MiSTer-devel/Arcade-SlapFight_MiSTer/docs/KiCAD/SlapFight/CPUA.kicad_sch

## KiCad design docs/KiCAD/SlapFight/CPUA.kicad_sch (2022-12-26)

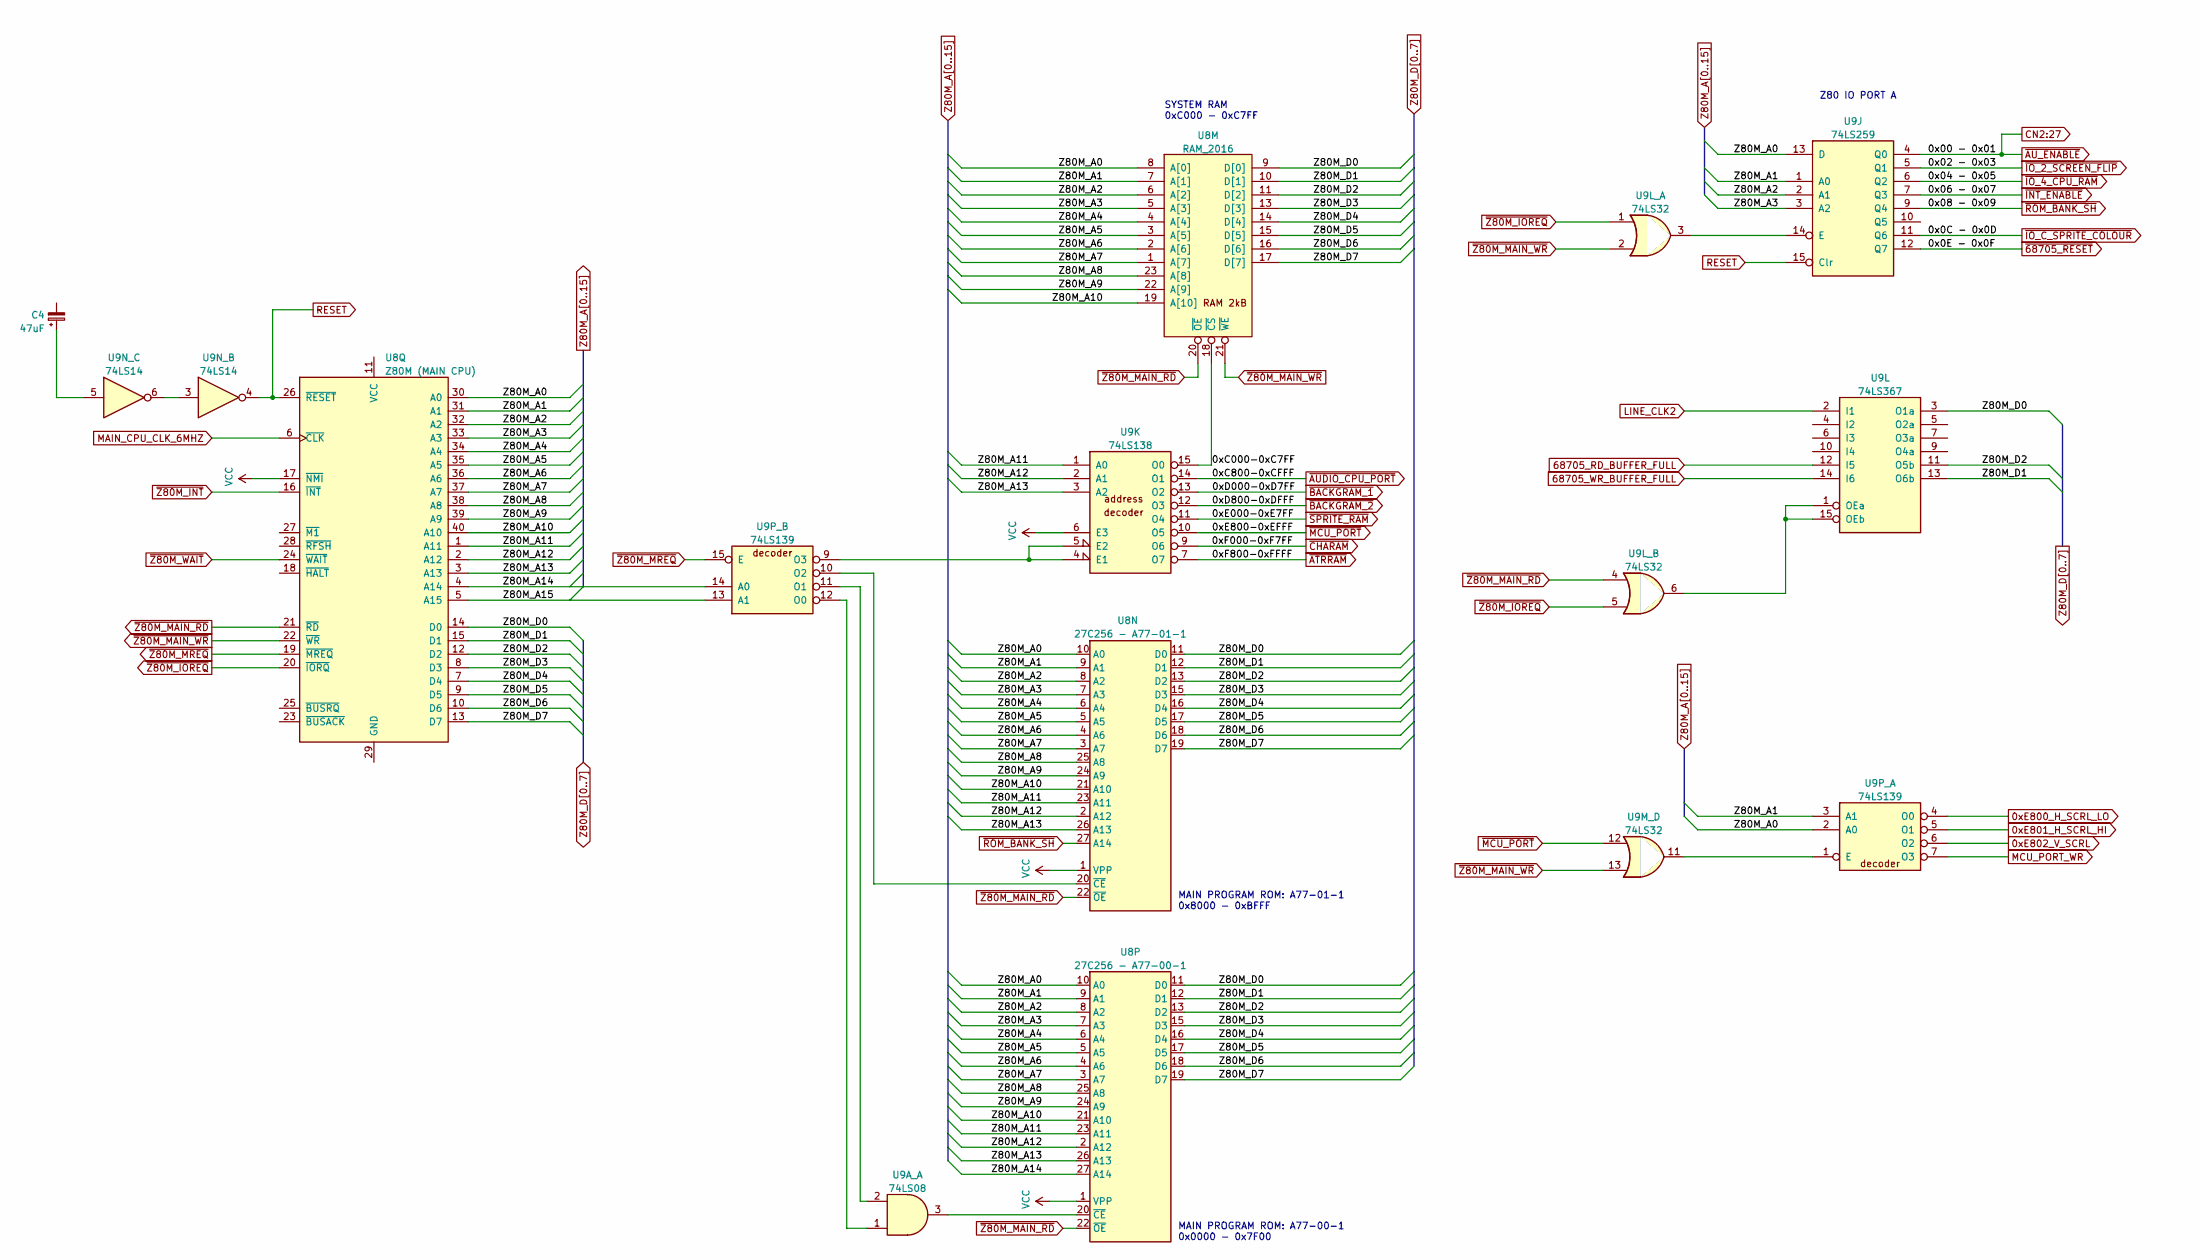
[picture p16: schematic CPUA.kicad_sch]

Parts:
C4: 47uF
U8M: RAM_2016
U8N: 27C256 - A77-01-1; DIP-28_W15.24mm
U8P: 27C256 - A77-00-1; DIP-28_W15.24mm
U8Q: Z80M (MAIN CPU)
U9A_: 74LS08
U9J: 74LS259
U9K: 74LS138
U9L: 74LS367
U9L_, U9M_: 74LS32
U9N_: 74LS14
U9P_: 74LS139

Connections:
0xC000-0xC7FF: U8M.18 (~CS), U9K.15 (O0)
0xE800_H_SCRL_LO: U9P_.4 (O0)
0xE801_H_SCRL_HI: U9P_.5 (O1)
0xE802_V_SCRL: U9P_.6 (O2)
68705_RD_BUFFER_FULL: U9L.12 (I5)
68705_WR_BUFFER_FULL: U9L.14 (I6)
CN2:27: U9J.4 (Q0)
LINE_CLK2: U9L.2 (I1)
MAIN_CPU_CLK_6MHZ: U8Q.6 (~CLK)
MCU_PORT_WR: U9P_.7 (O3)
unnamed: C4.1, U9N_.5
unnamed: U8N.20 (~CE), U9P_.10 (O2)
unnamed: U8P.20 (~CE), U9A_.3
unnamed: U9A_.1, U9P_.12 (O0)
unnamed: U9A_.2, U9P_.11 (O1)
unnamed: U9J.14 (E), U9L_.3
unnamed: U9K.4 (E1), U9K.5 (E2), U9P_.9 (O3)
unnamed: U9L.1 (OEa), U9L.15 (OEb), U9L_.6
unnamed: U9M_.11, U9P_.1 (E)
unnamed: U9N_.3, U9N_.6
RESET: U8Q.26 (~RESET), U9J.15 (Clr), U9N_.4
VCC: U8N.1 (VPP), U8P.1 (VPP), U8Q.17 (~NMI), U9K.6 (E3)
Z80M_A0: U8M.8 (A[0]), U8N.10 (A0), U8P.10 (A0), U8Q.30 (A0), U9J.13 (D), U9P_.2 (A0)
Z80M_A1: U8M.7 (A[1]), U8N.9 (A1), U8P.9 (A1), U8Q.31 (A1), U9J.1 (A0), U9P_.3 (A1)
Z80M_A2: U8M.6 (A[2]), U8N.8 (A2), U8P.8 (A2), U8Q.32 (A2), U9J.2 (A1)
Z80M_A3: U8M.5 (A[3]), U8N.7 (A3), U8P.7 (A3), U8Q.33 (A3), U9J.3 (A2)
Z80M_A4: U8M.4 (A[4]), U8N.6 (A4), U8P.6 (A4), U8Q.34 (A4)
Z80M_A5: U8M.3 (A[5]), U8N.5 (A5), U8P.5 (A5), U8Q.35 (A5)
Z80M_A6: U8M.2 (A[6]), U8N.4 (A6), U8P.4 (A6), U8Q.36 (A6)
Z80M_A7: U8M.1 (A[7]), U8N.3 (A7), U8P.3 (A7), U8Q.37 (A7)
Z80M_A8: U8M.23 (A[8]), U8N.25 (A8), U8P.25 (A8), U8Q.38 (A8)
Z80M_A9: U8M.22 (A[9]), U8N.24 (A9), U8P.24 (A9), U8Q.39 (A9)
Z80M_A10: U8M.19 (A[10]), U8N.21 (A10), U8P.21 (A10), U8Q.40 (A10)
Z80M_A11: U8N.23 (A11), U8P.23 (A11), U8Q.1 (A11), U9K.1 (A0)
Z80M_A12: U8N.2 (A12), U8P.2 (A12), U8Q.2 (A12), U9K.2 (A1)
Z80M_A13: U8N.26 (A13), U8P.26 (A13), U8Q.3 (A13), U9K.3 (A2)
Z80M_A14: U8P.27 (A14), U8Q.4 (A14), U9P_.14 (A0)
Z80M_A15: U8Q.5 (A15), U9P_.13 (A1)
Z80M_D0: U8M.9 (D[0]), U8N.11 (D0), U8P.11 (D0), U8Q.14 (D0), U9L.3 (O1a)
Z80M_D1: U8M.10 (D[1]), U8N.12 (D1), U8P.12 (D1), U8Q.15 (D1), U9L.13 (O6b)
Z80M_D2: U8M.11 (D[2]), U8N.13 (D2), U8P.13 (D2), U8Q.12 (D2), U9L.11 (O5b)
Z80M_D3: U8M.13 (D[3]), U8N.15 (D3), U8P.15 (D3), U8Q.8 (D3)
Z80M_D4: U8M.14 (D[4]), U8N.16 (D4), U8P.16 (D4), U8Q.7 (D4)
Z80M_D5: U8M.15 (D[5]), U8N.17 (D5), U8P.17 (D5), U8Q.9 (D5)
Z80M_D6: U8M.16 (D[6]), U8N.18 (D6), U8P.18 (D6), U8Q.10 (D6)
Z80M_D7: U8M.17 (D[7]), U8N.19 (D7), U8P.19 (D7), U8Q.13 (D7)
~68705_RESET: U9J.12 (Q7)
~ATRRAM: U9K.7 (O7)
~AUDIO_CPU_PORT: U9K.14 (O1)
~BACKGRAM_1: U9K.13 (O2)
~BACKGRAM_2: U9K.12 (O3)
~CHARAM: U9K.9 (O6)
~INT_ENABLE: U9J.7 (Q3)
~IO_2_SCREEN_FLIP: U9J.5 (Q1)
~IO_4_CPU_RAM: U9J.6 (Q2)
~IO_C_SPRITE_COLOUR: U9J.11 (Q6)
~MCU_PORT: U9K.10 (O5), U9M_.12
~ROM_BANK_SH: U8N.27 (A14), U9J.9 (Q4)
~SPRITE_RAM: U9K.11 (O4)
~Z80M_INT: U8Q.16 (~INT)
~Z80M_IOREQ: U8Q.20 (~IORQ), U9L_.1, U9L_.5
~Z80M_MAIN_RD: U8M.20 (~OE), U8N.22 (~OE), U8P.22 (~OE), U8Q.21 (~RD), U9L_.4
~Z80M_MAIN_WR: U8M.21 (~WE), U8Q.22 (~WR), U9L_.2, U9M_.13
~Z80M_MREQ: U8Q.19 (~MREQ), U9P_.15 (E)
~Z80M_WAIT: U8Q.24 (~WAIT)

Notes on the sheet:
MAIN PROGRAM ROM: A77-01-1 0x8000 - 0xBFFF
MAIN PROGRAM ROM: A77-00-1 0x0000 - 0x7F00
SYSTEM RAM 0xC000 - 0xC7FF
Z80 IO PORT A
