MiSTer-devel/Arcade-SlapFight_MiSTer/docs/KiCAD/SlapFight/SpriteRAM.kicad_sch

## KiCad design docs/KiCAD/SlapFight/SpriteRAM.kicad_sch (2022-12-26)

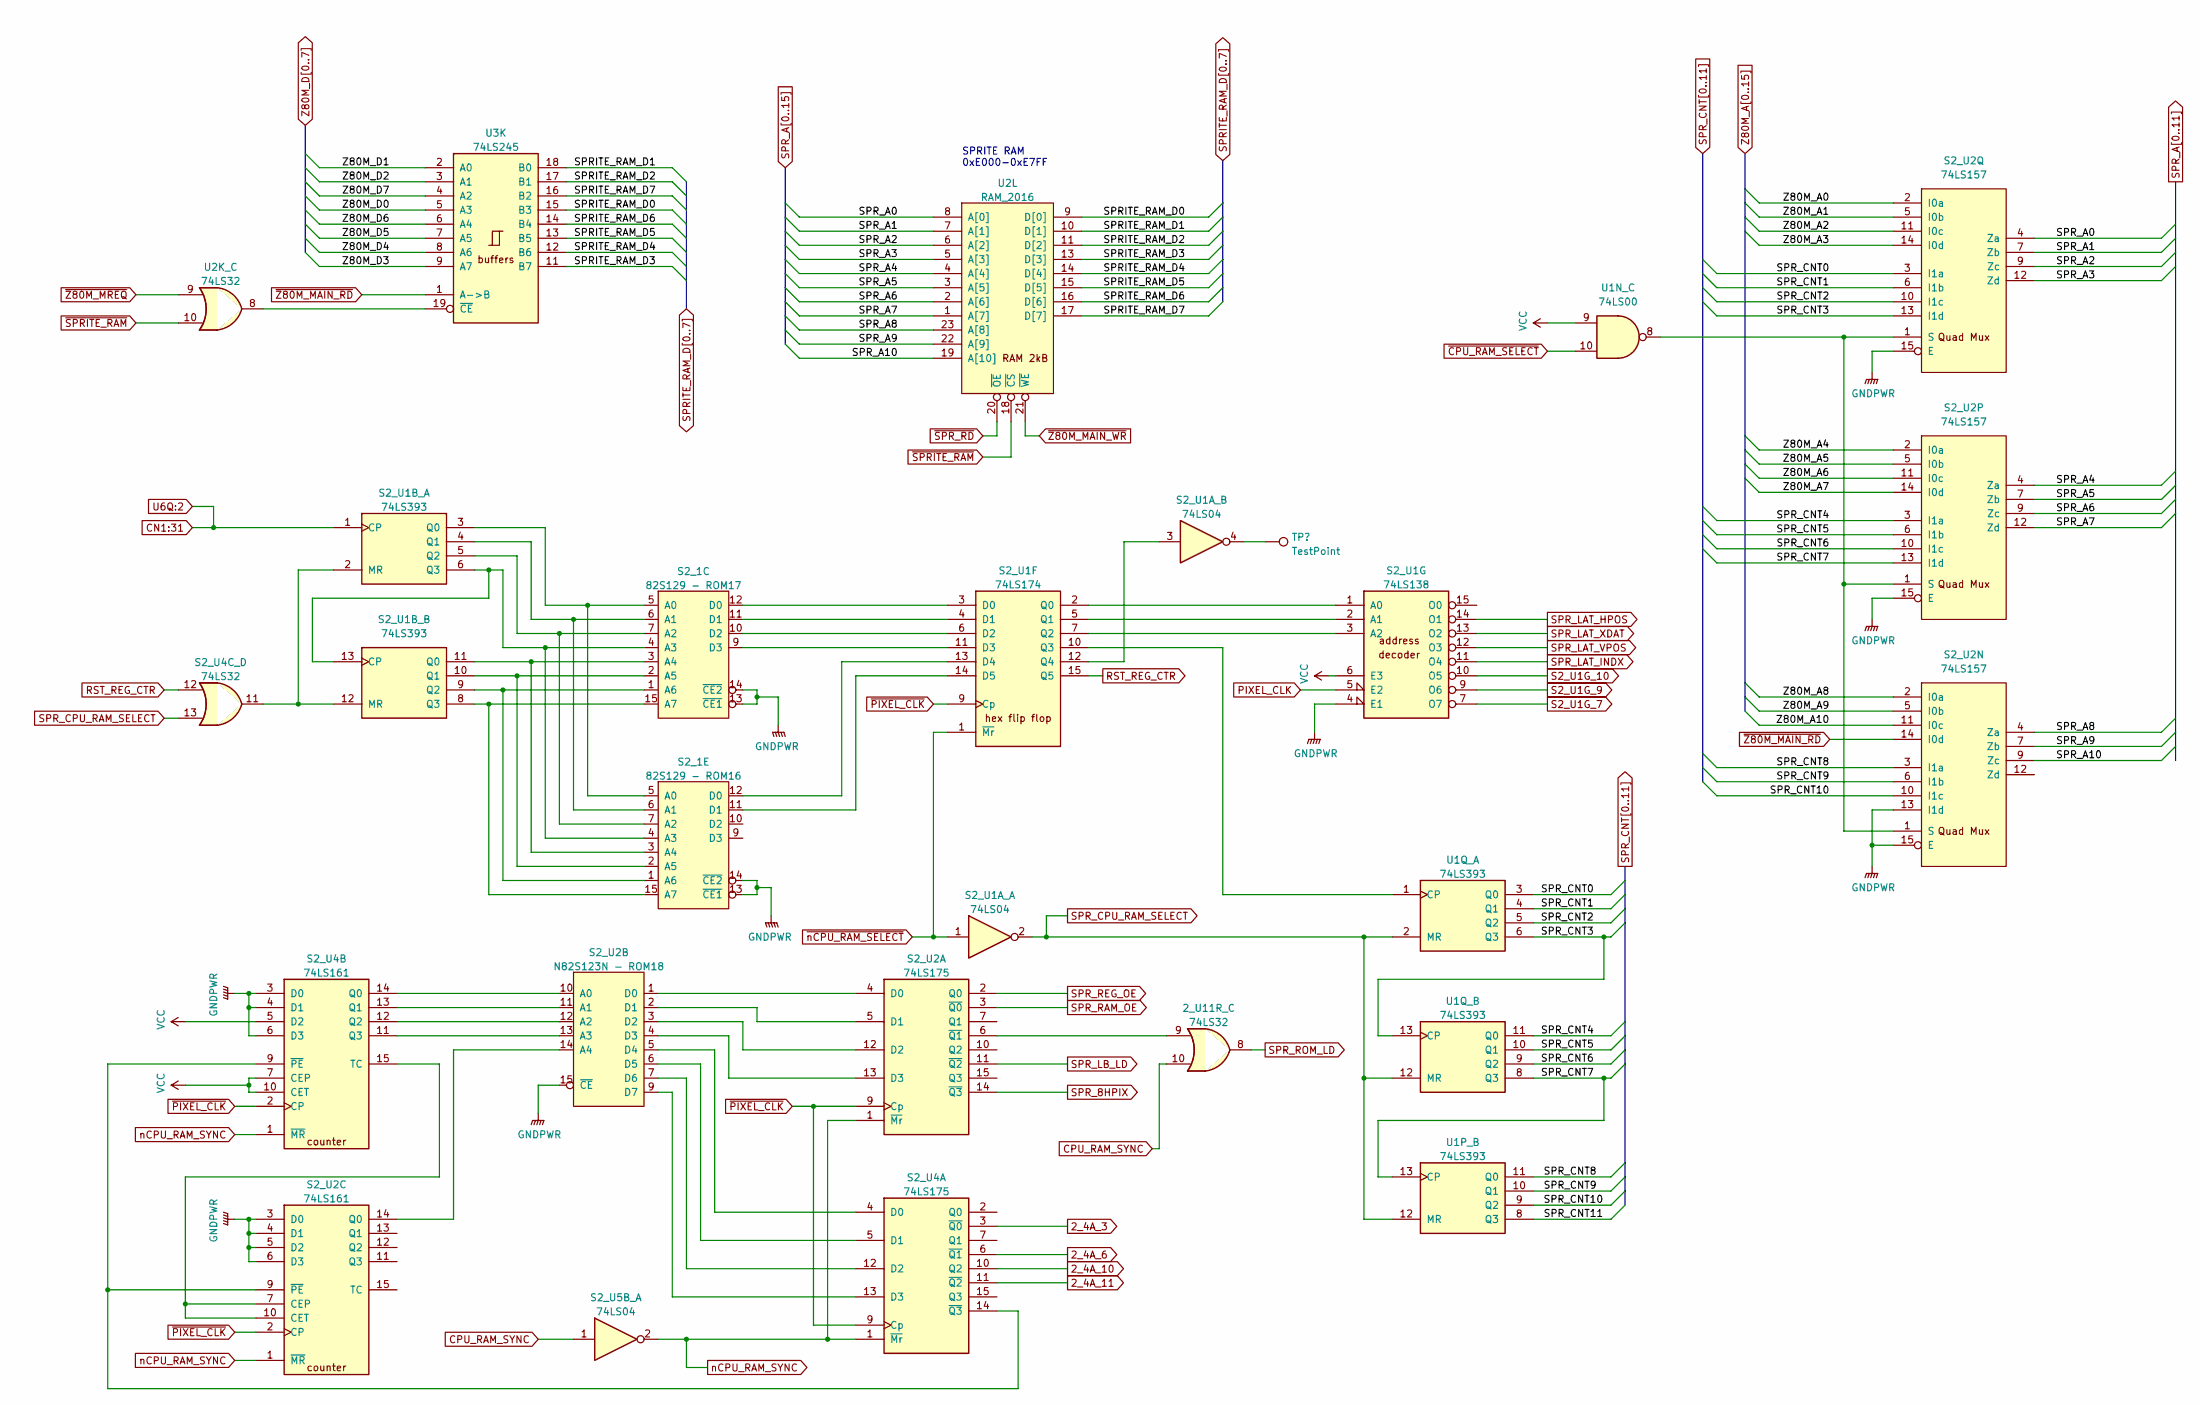
[picture p17: schematic SpriteRAM.kicad_sch]

Parts:
2_U11R_: 74LS32
S2_1C: 82S129 - ROM17
S2_1E: 82S129 - ROM16
S2_U1A_, S2_U5B_: 74LS04
S2_U1B_: 74LS393
S2_U1F: 74LS174
S2_U1G: 74LS138
S2_U2A, S2_U4A: 74LS175
S2_U2B: N82S123N - ROM18
S2_U2C, S2_U4B: 74LS161
S2_U2N, S2_U2P, S2_U2Q: 74LS157
S2_U4C_: 74LS32
U1N_: 74LS00
U1P_, U1Q_: 74LS393
U2K_: 74LS32
U2L: RAM_2016
U3K: 74LS245

Connections:
2_4A_3: S2_U4A.3 (~Q0)
2_4A_6: S2_U4A.6 (~Q1)
2_4A_10: S2_U4A.10 (Q2)
2_4A_11: S2_U4A.11 (~Q2)
CN1:31: S2_U1B_.1 (CP)
CPU_RAM_SYNC: 2_U11R_.10, S2_U5B_.1
unnamed: 2_U11R_.9, S2_U2A.6 (~Q1)
unnamed: S2_1C.1 (A6), S2_1E.1 (A6), S2_U1B_.9 (Q2)
unnamed: S2_1C.2 (A5), S2_1E.2 (A5), S2_U1B_.10 (Q1)
unnamed: S2_1C.3 (A4), S2_1E.3 (A4), S2_U1B_.11 (Q0)
unnamed: S2_1C.4 (A3), S2_1E.4 (A3), S2_U1B_.6 (Q3), S2_U1B_.13 (CP)
unnamed: S2_1C.5 (A0), S2_1E.5 (A0), S2_U1B_.3 (Q0)
unnamed: S2_1C.6 (A1), S2_1E.6 (A1), S2_U1B_.4 (Q1)
unnamed: S2_1C.7 (A2), S2_1E.7 (A2), S2_U1B_.5 (Q2)
unnamed: S2_1C.9 (D3), S2_U1F.11 (D3)
unnamed: S2_1C.10 (D2), S2_U1F.6 (D2)
unnamed: S2_1C.11 (D1), S2_U1F.4 (D1)
unnamed: S2_1C.12 (D0), S2_U1F.3 (D0)
unnamed: S2_1C.13 (~CE1), S2_1C.14 (~CE2)
unnamed: S2_1C.15 (A7), S2_1E.15 (A7), S2_U1B_.8 (Q3)
unnamed: S2_1E.11 (D1), S2_U1F.14 (D5)
unnamed: S2_1E.12 (D0), S2_U1F.13 (D4)
unnamed: S2_1E.13 (~CE1), S2_1E.14 (~CE2)
unnamed: S2_U1A_.3, S2_U1F.12 (Q4)
unnamed: S2_U1B_.2 (MR), S2_U1B_.12 (MR), S2_U4C_.11
unnamed: S2_U1F.2 (Q0), S2_U1G.1 (A0)
unnamed: S2_U1F.5 (Q1), S2_U1G.2 (A1)
unnamed: S2_U1F.7 (Q2), S2_U1G.3 (A2)
unnamed: S2_U1F.10 (Q3), U1Q_.1 (CP)
unnamed: S2_U2A.4 (D0), S2_U2B.1 (D0)
unnamed: S2_U2A.5 (D1), S2_U2B.2 (D1)
unnamed: S2_U2A.12 (D2), S2_U2B.3 (D2)
unnamed: S2_U2A.13 (D3), S2_U2B.4 (D3)
unnamed: S2_U2B.5 (D4), S2_U4A.4 (D0)
unnamed: S2_U2B.6 (D5), S2_U4A.5 (D1)
unnamed: S2_U2B.7 (D6), S2_U4A.12 (D2)
unnamed: S2_U2B.9 (D7), S2_U4A.13 (D3)
unnamed: S2_U2B.10 (A0), S2_U4B.14 (Q0)
unnamed: S2_U2B.11 (A1), S2_U4B.13 (Q1)
unnamed: S2_U2B.12 (A2), S2_U4B.12 (Q2)
unnamed: S2_U2B.13 (A3), S2_U4B.11 (Q3)
unnamed: S2_U2B.14 (A4), S2_U2C.14 (Q0)
unnamed: S2_U2C.3 (D0), S2_U2C.4 (D1), S2_U2C.5 (D2), S2_U2C.6 (D3)
unnamed: S2_U2C.9 (~PE), S2_U4A.14 (~Q3), S2_U4B.9 (~PE)
unnamed: S2_U2C.7 (CEP), S2_U2C.10 (CET), S2_U4B.15 (TC)
unnamed: S2_U2N.1 (S), S2_U2P.1 (S), S2_U2Q.1 (S), U1N_.8
unnamed: S2_U2N.13 (I1d), S2_U2N.15 (E)
unnamed: S2_U4B.3 (D0), S2_U4B.4 (D1), S2_U4B.6 (D3)
unnamed: S2_U4B.7 (CEP), S2_U4B.10 (CET)
unnamed: U2K_.8, U3K.19 (~CE)
PIXEL_CLK: S2_U1G.5 (E2)
RST_REG_CTR: S2_U1F.15 (Q5), S2_U4C_.12
S2_U1G_7: S2_U1G.7 (O7)
S2_U1G_9: S2_U1G.9 (O6)
S2_U1G_10: S2_U1G.10 (O5)
SPRITE_RAM_D0: U2L.9 (D[0]), U3K.15 (B3)
SPRITE_RAM_D1: U2L.10 (D[1]), U3K.18 (B0)
SPRITE_RAM_D2: U2L.11 (D[2]), U3K.17 (B1)
SPRITE_RAM_D3: U2L.13 (D[3]), U3K.11 (B7)
SPRITE_RAM_D4: U2L.14 (D[4]), U3K.12 (B6)
SPRITE_RAM_D5: U2L.15 (D[5]), U3K.13 (B5)
SPRITE_RAM_D6: U2L.16 (D[6]), U3K.14 (B4)
SPRITE_RAM_D7: U2L.17 (D[7]), U3K.16 (B2)
SPR_8HPIX: S2_U2A.14 (~Q3)
SPR_A0: S2_U2Q.4 (Za), U2L.8 (A[0])
SPR_A1: S2_U2Q.7 (Zb), U2L.7 (A[1])
SPR_A2: S2_U2Q.9 (Zc), U2L.6 (A[2])
SPR_A3: S2_U2Q.12 (Zd), U2L.5 (A[3])
SPR_A4: S2_U2P.4 (Za), U2L.4 (A[4])
SPR_A5: S2_U2P.7 (Zb), U2L.3 (A[5])
SPR_A6: S2_U2P.9 (Zc), U2L.2 (A[6])
SPR_A7: S2_U2P.12 (Zd), U2L.1 (A[7])
SPR_A8: S2_U2N.4 (Za), U2L.23 (A[8])
SPR_A9: S2_U2N.7 (Zb), U2L.22 (A[9])
SPR_A10: S2_U2N.9 (Zc), U2L.19 (A[10])
SPR_CNT0: S2_U2Q.3 (I1a), U1Q_.3 (Q0)
SPR_CNT1: S2_U2Q.6 (I1b), U1Q_.4 (Q1)
SPR_CNT2: S2_U2Q.10 (I1c), U1Q_.5 (Q2)
SPR_CNT3: S2_U2Q.13 (I1d), U1Q_.6 (Q3), U1Q_.13 (CP)
SPR_CNT4: S2_U2P.3 (I1a), U1Q_.11 (Q0)
SPR_CNT5: S2_U2P.6 (I1b), U1Q_.10 (Q1)
SPR_CNT6: S2_U2P.10 (I1c), U1Q_.9 (Q2)
SPR_CNT7: S2_U2P.13 (I1d), U1P_.13 (CP), U1Q_.8 (Q3)
SPR_CNT8: S2_U2N.3 (I1a), U1P_.11 (Q0)
SPR_CNT9: S2_U2N.6 (I1b), U1P_.10 (Q1)
SPR_CNT10: S2_U2N.10 (I1c), U1P_.9 (Q2)
SPR_CNT11: U1P_.8 (Q3)
SPR_CPU_RAM_SELECT: S2_U1A_.2, S2_U4C_.13, U1P_.12 (MR), U1Q_.2 (MR), U1Q_.12 (MR)
SPR_LAT_HPOS: S2_U1G.14 (O1)
SPR_LAT_INDX: S2_U1G.11 (O4)
SPR_LAT_VPOS: S2_U1G.12 (O3)
SPR_LAT_XDAT: S2_U1G.13 (O2)
SPR_LB_LD: S2_U2A.11 (~Q2)
SPR_RAM_OE: S2_U2A.3 (~Q0)
SPR_REG_OE: S2_U2A.2 (Q0)
SPR_ROM_LD: 2_U11R_.8
Z80M_A0: S2_U2Q.2 (I0a)
Z80M_A1: S2_U2Q.5 (I0b)
Z80M_A2: S2_U2Q.11 (I0c)
Z80M_A3: S2_U2Q.14 (I0d)
Z80M_A4: S2_U2P.2 (I0a)
Z80M_A5: S2_U2P.5 (I0b)
Z80M_A6: S2_U2P.11 (I0c)
Z80M_A7: S2_U2P.14 (I0d)
Z80M_A8: S2_U2N.2 (I0a)
Z80M_A9: S2_U2N.5 (I0b)
Z80M_A10: S2_U2N.11 (I0c)
Z80M_D0: U3K.5 (A3)
Z80M_D1: U3K.2 (A0)
Z80M_D2: U3K.3 (A1)
Z80M_D3: U3K.9 (A7)
Z80M_D4: U3K.8 (A6)
Z80M_D5: U3K.7 (A5)
Z80M_D6: U3K.6 (A4)
Z80M_D7: U3K.4 (A2)
nCPU_RAM_SYNC: S2_U2A.1 (~Mr), S2_U2C.1 (~MR), S2_U4A.1 (~Mr), S2_U4B.1 (~MR), S2_U5B_.2
~CPU_RAM_SELECT: U1N_.10
~PIXEL_CLK: S2_U1F.9 (Cp), S2_U2A.9 (Cp), S2_U2C.2 (CP), S2_U4A.9 (Cp), S2_U4B.2 (CP)
~SPRITE_RAM: U2K_.10, U2L.18 (~CS)
~SPR_RD: U2L.20 (~OE)
~Z80M_MAIN_RD: S2_U2N.14 (I0d), U3K.1 (A->B)
~Z80M_MAIN_WR: U2L.21 (~WE)
~Z80M_MREQ: U2K_.9
~nCPU_RAM_SELECT: S2_U1A_.1, S2_U1F.1 (~Mr)

Notes on the sheet:
SPRITE RAM 0xE000-0xE7FF
