MiSTer-devel/Arcade-SlapFight_MiSTer/docs/KiCAD/SlapFight/SpriteROM.kicad_sch

## KiCad design docs/KiCAD/SlapFight/SpriteROM.kicad_sch (2022-12-26)

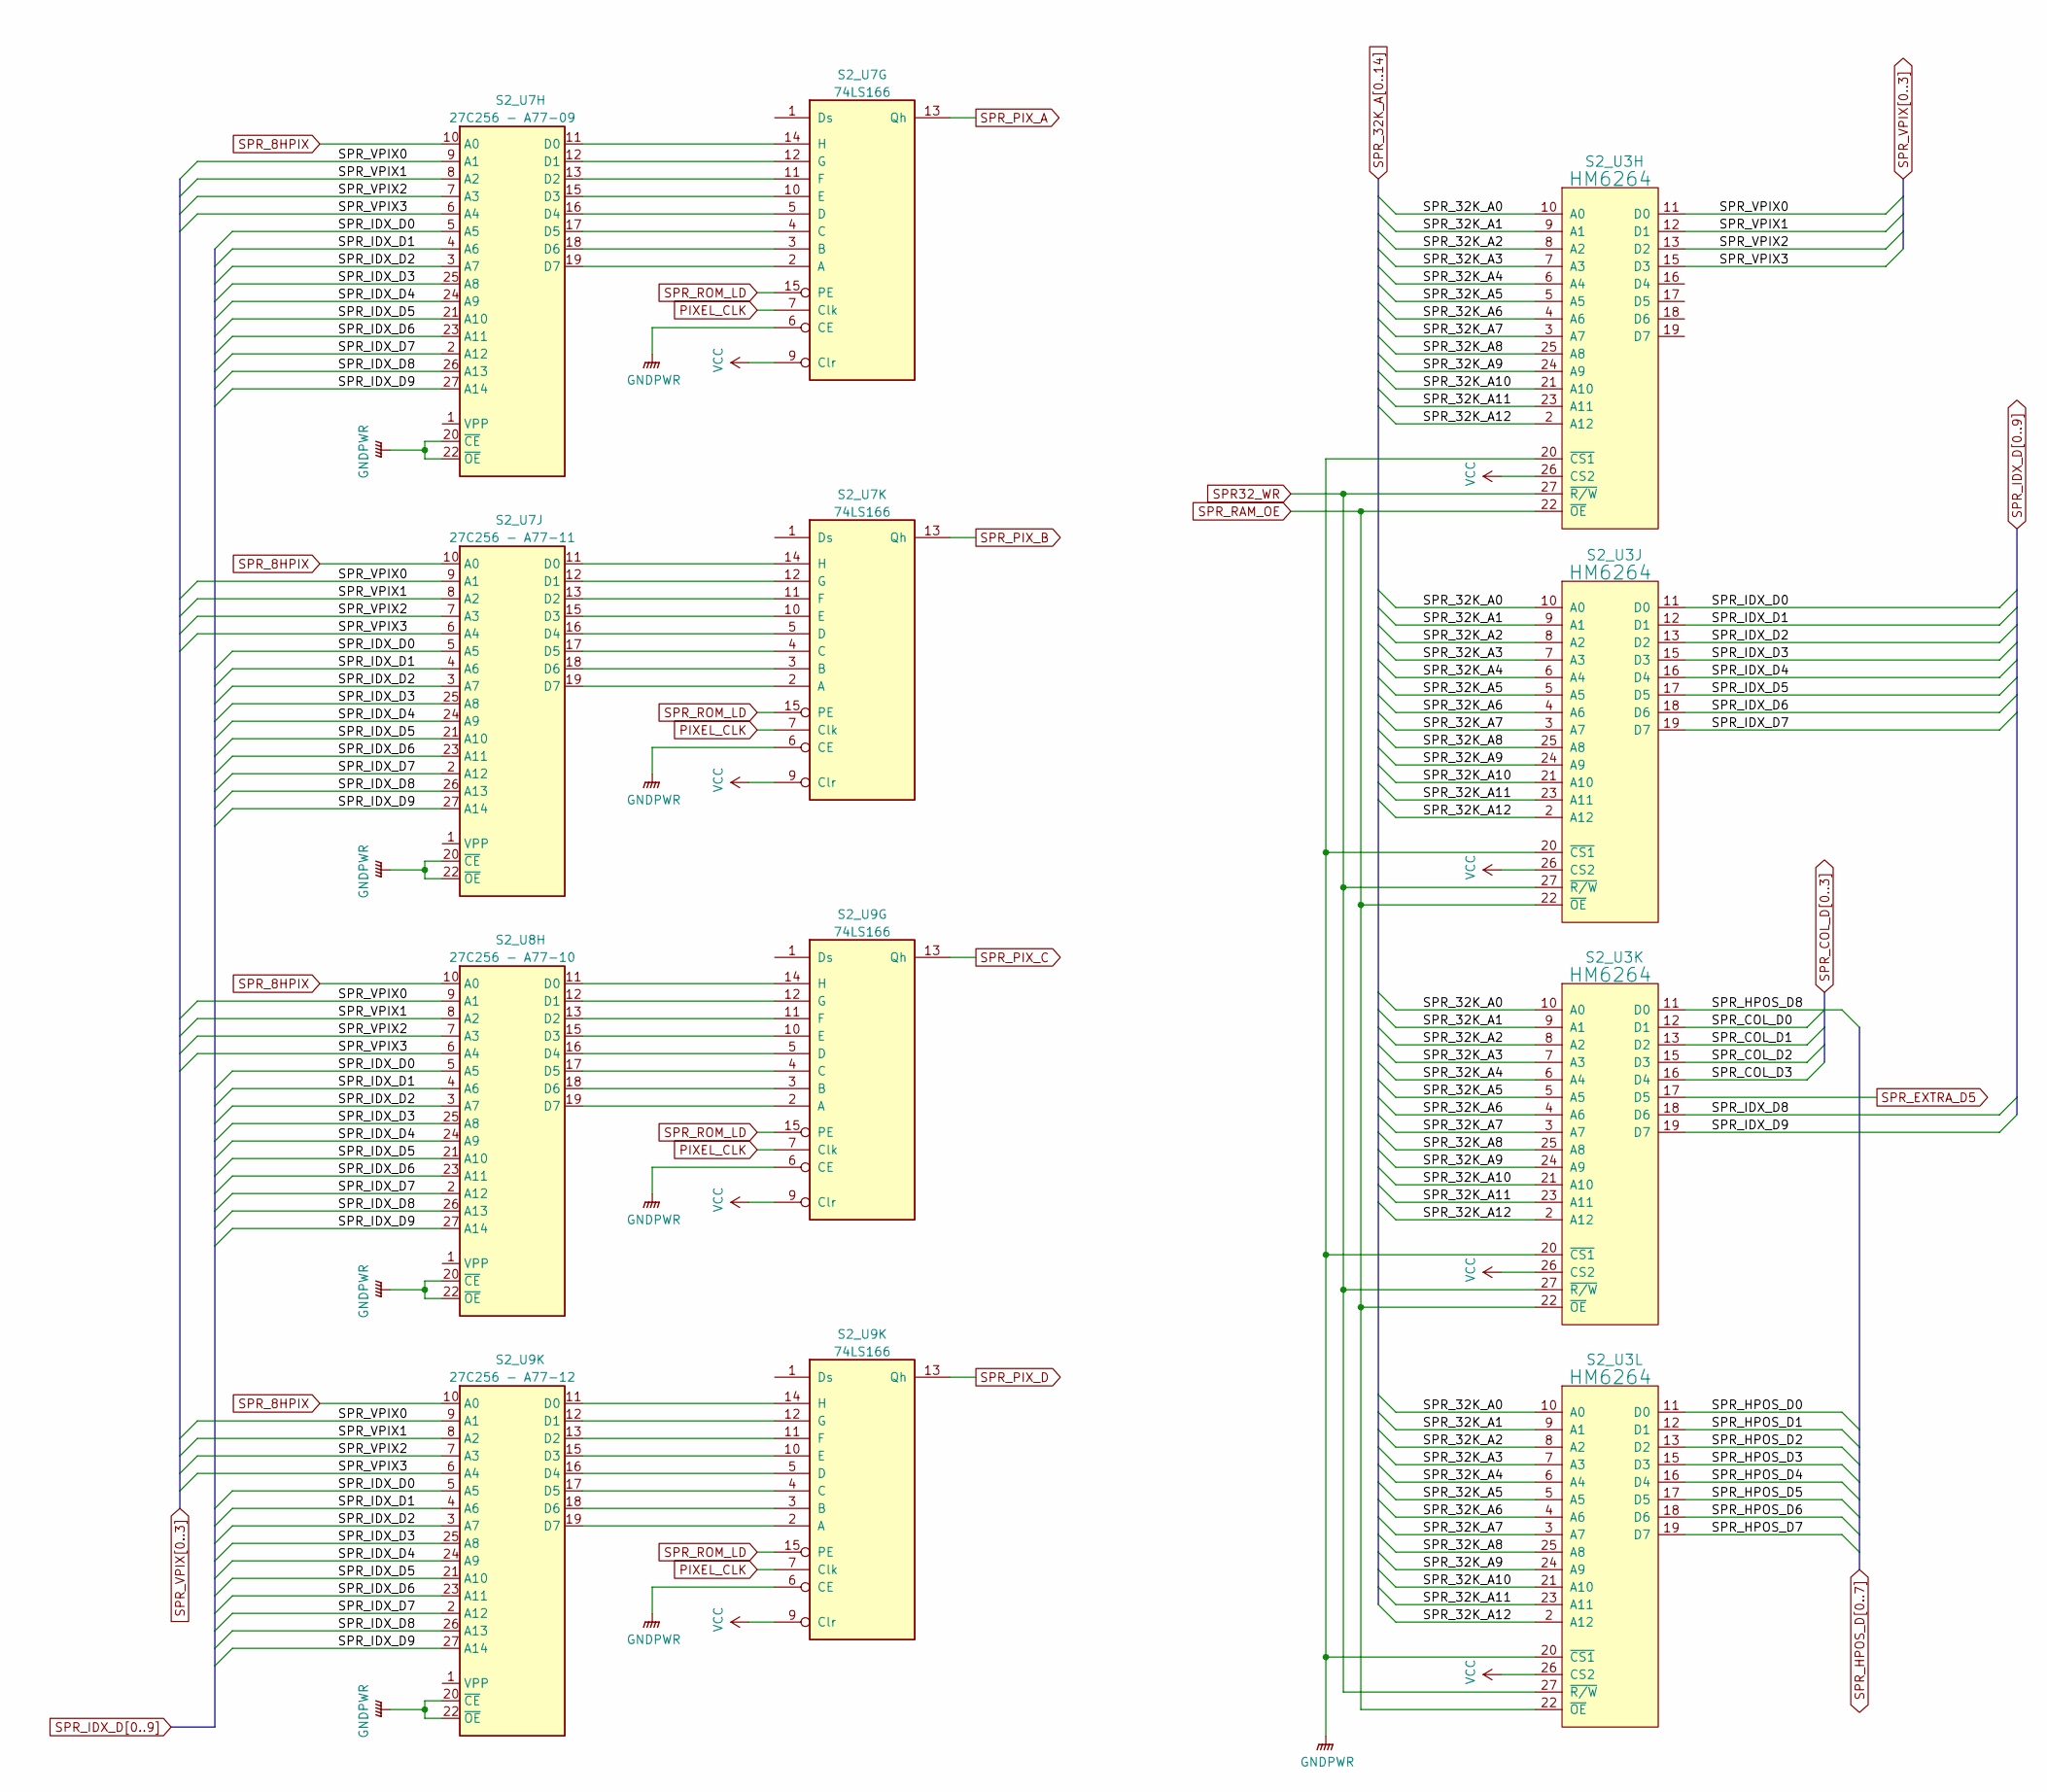
[picture p18: schematic SpriteROM.kicad_sch]

Parts:
S2_U3H, S2_U3J, S2_U3K, S2_U3L: HM6264
S2_U7G, S2_U7K, S2_U9G, S2_U9K: 74LS166
S2_U7H: 27C256 - A77-09; DIP-28_W15.24mm
S2_U7J: 27C256 - A77-11; DIP-28_W15.24mm
S2_U8H: 27C256 - A77-10; DIP-28_W15.24mm

Connections:
unnamed: S2_U3H.20 (~CS1), S2_U3J.20 (~CS1), S2_U3K.20 (~CS1), S2_U3L.20 (~CS1)
unnamed: S2_U7G.2 (A), S2_U7H.19 (D7)
unnamed: S2_U7G.3 (B), S2_U7H.18 (D6)
unnamed: S2_U7G.4 (C), S2_U7H.17 (D5)
unnamed: S2_U7G.5 (D), S2_U7H.16 (D4)
unnamed: S2_U7G.10 (E), S2_U7H.15 (D3)
unnamed: S2_U7G.11 (F), S2_U7H.13 (D2)
unnamed: S2_U7G.12 (G), S2_U7H.12 (D1)
unnamed: S2_U7G.14 (H), S2_U7H.11 (D0)
unnamed: S2_U7H.20 (~CE), S2_U7H.22 (~OE)
unnamed: S2_U7J.11 (D0), S2_U7K.14 (H)
unnamed: S2_U7J.12 (D1), S2_U7K.12 (G)
unnamed: S2_U7J.13 (D2), S2_U7K.11 (F)
unnamed: S2_U7J.15 (D3), S2_U7K.10 (E)
unnamed: S2_U7J.16 (D4), S2_U7K.5 (D)
unnamed: S2_U7J.17 (D5), S2_U7K.4 (C)
unnamed: S2_U7J.18 (D6), S2_U7K.3 (B)
unnamed: S2_U7J.19 (D7), S2_U7K.2 (A)
unnamed: S2_U7J.20 (~CE), S2_U7J.22 (~OE)
unnamed: S2_U8H.11 (D0), S2_U9G.14 (H)
unnamed: S2_U8H.12 (D1), S2_U9G.12 (G)
unnamed: S2_U8H.13 (D2), S2_U9G.11 (F)
unnamed: S2_U8H.15 (D3), S2_U9G.10 (E)
unnamed: S2_U8H.16 (D4), S2_U9G.5 (D)
unnamed: S2_U8H.17 (D5), S2_U9G.4 (C)
unnamed: S2_U8H.18 (D6), S2_U9G.3 (B)
unnamed: S2_U8H.19 (D7), S2_U9G.2 (A)
unnamed: S2_U8H.20 (~CE), S2_U8H.22 (~OE)
unnamed: S2_U9K.10 (A0), S2_U9K.15 (D3)
unnamed: S2_U9K.11 (D0), S2_U9K.13 (D2), S2_U9K.14 (GND)
unnamed: S2_U9K.5 (A5), S2_U9K.16 (D4)
unnamed: S2_U9K.4 (A6), S2_U9K.17 (D5)
unnamed: S2_U9K.3 (A7), S2_U9K.18 (D6)
unnamed: S2_U9K.2 (A12), S2_U9K.19 (D7)
unnamed: S2_U9K.20 (~CE), S2_U9K.22 (~OE)
PIXEL_CLK: S2_U7G.7 (Clk), S2_U7K.7 (Clk), S2_U9G.7 (Clk), S2_U9K.7 (A3)
SPR32_WR: S2_U3H.27 (~R/W), S2_U3J.27 (~R/W), S2_U3K.27 (~R/W), S2_U3L.27 (~R/W)
SPR_8HPIX: S2_U7H.10 (A0), S2_U7J.10 (A0), S2_U8H.10 (A0), S2_U9K.10 (A0)
SPR_32K_A0: S2_U3H.10 (A0), S2_U3J.10 (A0), S2_U3K.10 (A0), S2_U3L.10 (A0)
SPR_32K_A1: S2_U3H.9 (A1), S2_U3J.9 (A1), S2_U3K.9 (A1), S2_U3L.9 (A1)
SPR_32K_A2: S2_U3H.8 (A2), S2_U3J.8 (A2), S2_U3K.8 (A2), S2_U3L.8 (A2)
SPR_32K_A3: S2_U3H.7 (A3), S2_U3J.7 (A3), S2_U3K.7 (A3), S2_U3L.7 (A3)
SPR_32K_A4: S2_U3H.6 (A4), S2_U3J.6 (A4), S2_U3K.6 (A4), S2_U3L.6 (A4)
SPR_32K_A5: S2_U3H.5 (A5), S2_U3J.5 (A5), S2_U3K.5 (A5), S2_U3L.5 (A5)
SPR_32K_A6: S2_U3H.4 (A6), S2_U3J.4 (A6), S2_U3K.4 (A6), S2_U3L.4 (A6)
SPR_32K_A7: S2_U3H.3 (A7), S2_U3J.3 (A7), S2_U3K.3 (A7), S2_U3L.3 (A7)
SPR_32K_A8: S2_U3H.25 (A8), S2_U3J.25 (A8), S2_U3K.25 (A8), S2_U3L.25 (A8)
SPR_32K_A9: S2_U3H.24 (A9), S2_U3J.24 (A9), S2_U3K.24 (A9), S2_U3L.24 (A9)
SPR_32K_A10: S2_U3H.21 (A10), S2_U3J.21 (A10), S2_U3K.21 (A10), S2_U3L.21 (A10)
SPR_32K_A11: S2_U3H.23 (A11), S2_U3J.23 (A11), S2_U3K.23 (A11), S2_U3L.23 (A11)
SPR_32K_A12: S2_U3H.2 (A12), S2_U3J.2 (A12), S2_U3K.2 (A12), S2_U3L.2 (A12)
SPR_COL_D0: S2_U3K.12 (D1)
SPR_COL_D1: S2_U3K.13 (D2)
SPR_COL_D2: S2_U3K.15 (D3)
SPR_COL_D3: S2_U3K.16 (D4)
SPR_EXTRA_D5: S2_U3K.17 (D5)
SPR_HPOS_D0: S2_U3L.11 (D0)
SPR_HPOS_D1: S2_U3L.12 (D1)
SPR_HPOS_D2: S2_U3L.13 (D2)
SPR_HPOS_D3: S2_U3L.15 (D3)
SPR_HPOS_D4: S2_U3L.16 (D4)
SPR_HPOS_D5: S2_U3L.17 (D5)
SPR_HPOS_D6: S2_U3L.18 (D6)
SPR_HPOS_D7: S2_U3L.19 (D7)
SPR_HPOS_D8: S2_U3K.11 (D0)
SPR_IDX_D0: S2_U3J.11 (D0), S2_U7H.5 (A5), S2_U7J.5 (A5), S2_U8H.5 (A5), S2_U9K.5 (A5)
SPR_IDX_D1: S2_U3J.12 (D1), S2_U7H.4 (A6), S2_U7J.4 (A6), S2_U8H.4 (A6), S2_U9K.4 (A6)
SPR_IDX_D2: S2_U3J.13 (D2), S2_U7H.3 (A7), S2_U7J.3 (A7), S2_U8H.3 (A7), S2_U9K.3 (A7)
SPR_IDX_D3: S2_U3J.15 (D3), S2_U7H.25 (A8), S2_U7J.25 (A8), S2_U8H.25 (A8), S2_U9K.25 (A8)
SPR_IDX_D4: S2_U3J.16 (D4), S2_U7H.24 (A9), S2_U7J.24 (A9), S2_U8H.24 (A9), S2_U9K.24 (A9)
SPR_IDX_D5: S2_U3J.17 (D5), S2_U7H.21 (A10), S2_U7J.21 (A10), S2_U8H.21 (A10), S2_U9K.21 (A10)
SPR_IDX_D6: S2_U3J.18 (D6), S2_U7H.23 (A11), S2_U7J.23 (A11), S2_U8H.23 (A11), S2_U9K.23 (A11)
SPR_IDX_D7: S2_U3J.19 (D7), S2_U7H.2 (A12), S2_U7J.2 (A12), S2_U8H.2 (A12), S2_U9K.2 (A12)
SPR_IDX_D8: S2_U3K.18 (D6), S2_U7H.26 (A13), S2_U7J.26 (A13), S2_U8H.26 (A13), S2_U9K.26 (A13)
SPR_IDX_D9: S2_U3K.19 (D7), S2_U7H.27 (A14), S2_U7J.27 (A14), S2_U8H.27 (A14), S2_U9K.27 (A14)
SPR_PIX_A: S2_U7G.13 (Qh)
SPR_PIX_B: S2_U7K.13 (Qh)
SPR_PIX_C: S2_U9G.13 (Qh)
SPR_PIX_D: S2_U9K.13 (D2)
SPR_RAM_OE: S2_U3H.22 (~OE), S2_U3J.22 (~OE), S2_U3K.22 (~OE), S2_U3L.22 (~OE)
SPR_ROM_LD: S2_U7G.15 (PE), S2_U7K.15 (PE), S2_U9G.15 (PE), S2_U9K.15 (D3)
SPR_VPIX0: S2_U3H.11 (D0), S2_U7H.9 (A1), S2_U7J.9 (A1), S2_U8H.9 (A1), S2_U9K.9 (A1)
SPR_VPIX1: S2_U3H.12 (D1), S2_U7H.8 (A2), S2_U7J.8 (A2), S2_U8H.8 (A2), S2_U9K.8 (A2)
SPR_VPIX2: S2_U3H.13 (D2), S2_U7H.7 (A3), S2_U7J.7 (A3), S2_U8H.7 (A3), S2_U9K.7 (A3)
SPR_VPIX3: S2_U3H.15 (D3), S2_U7H.6 (A4), S2_U7J.6 (A4), S2_U8H.6 (A4), S2_U9K.6 (A4)
