MiSTer-devel/Arcade-SlapFight_MiSTer/docs/KiCAD/SlapFight/aucpu.kicad_sch

## KiCad design docs/KiCAD/SlapFight/aucpu.kicad_sch (2022-12-28)

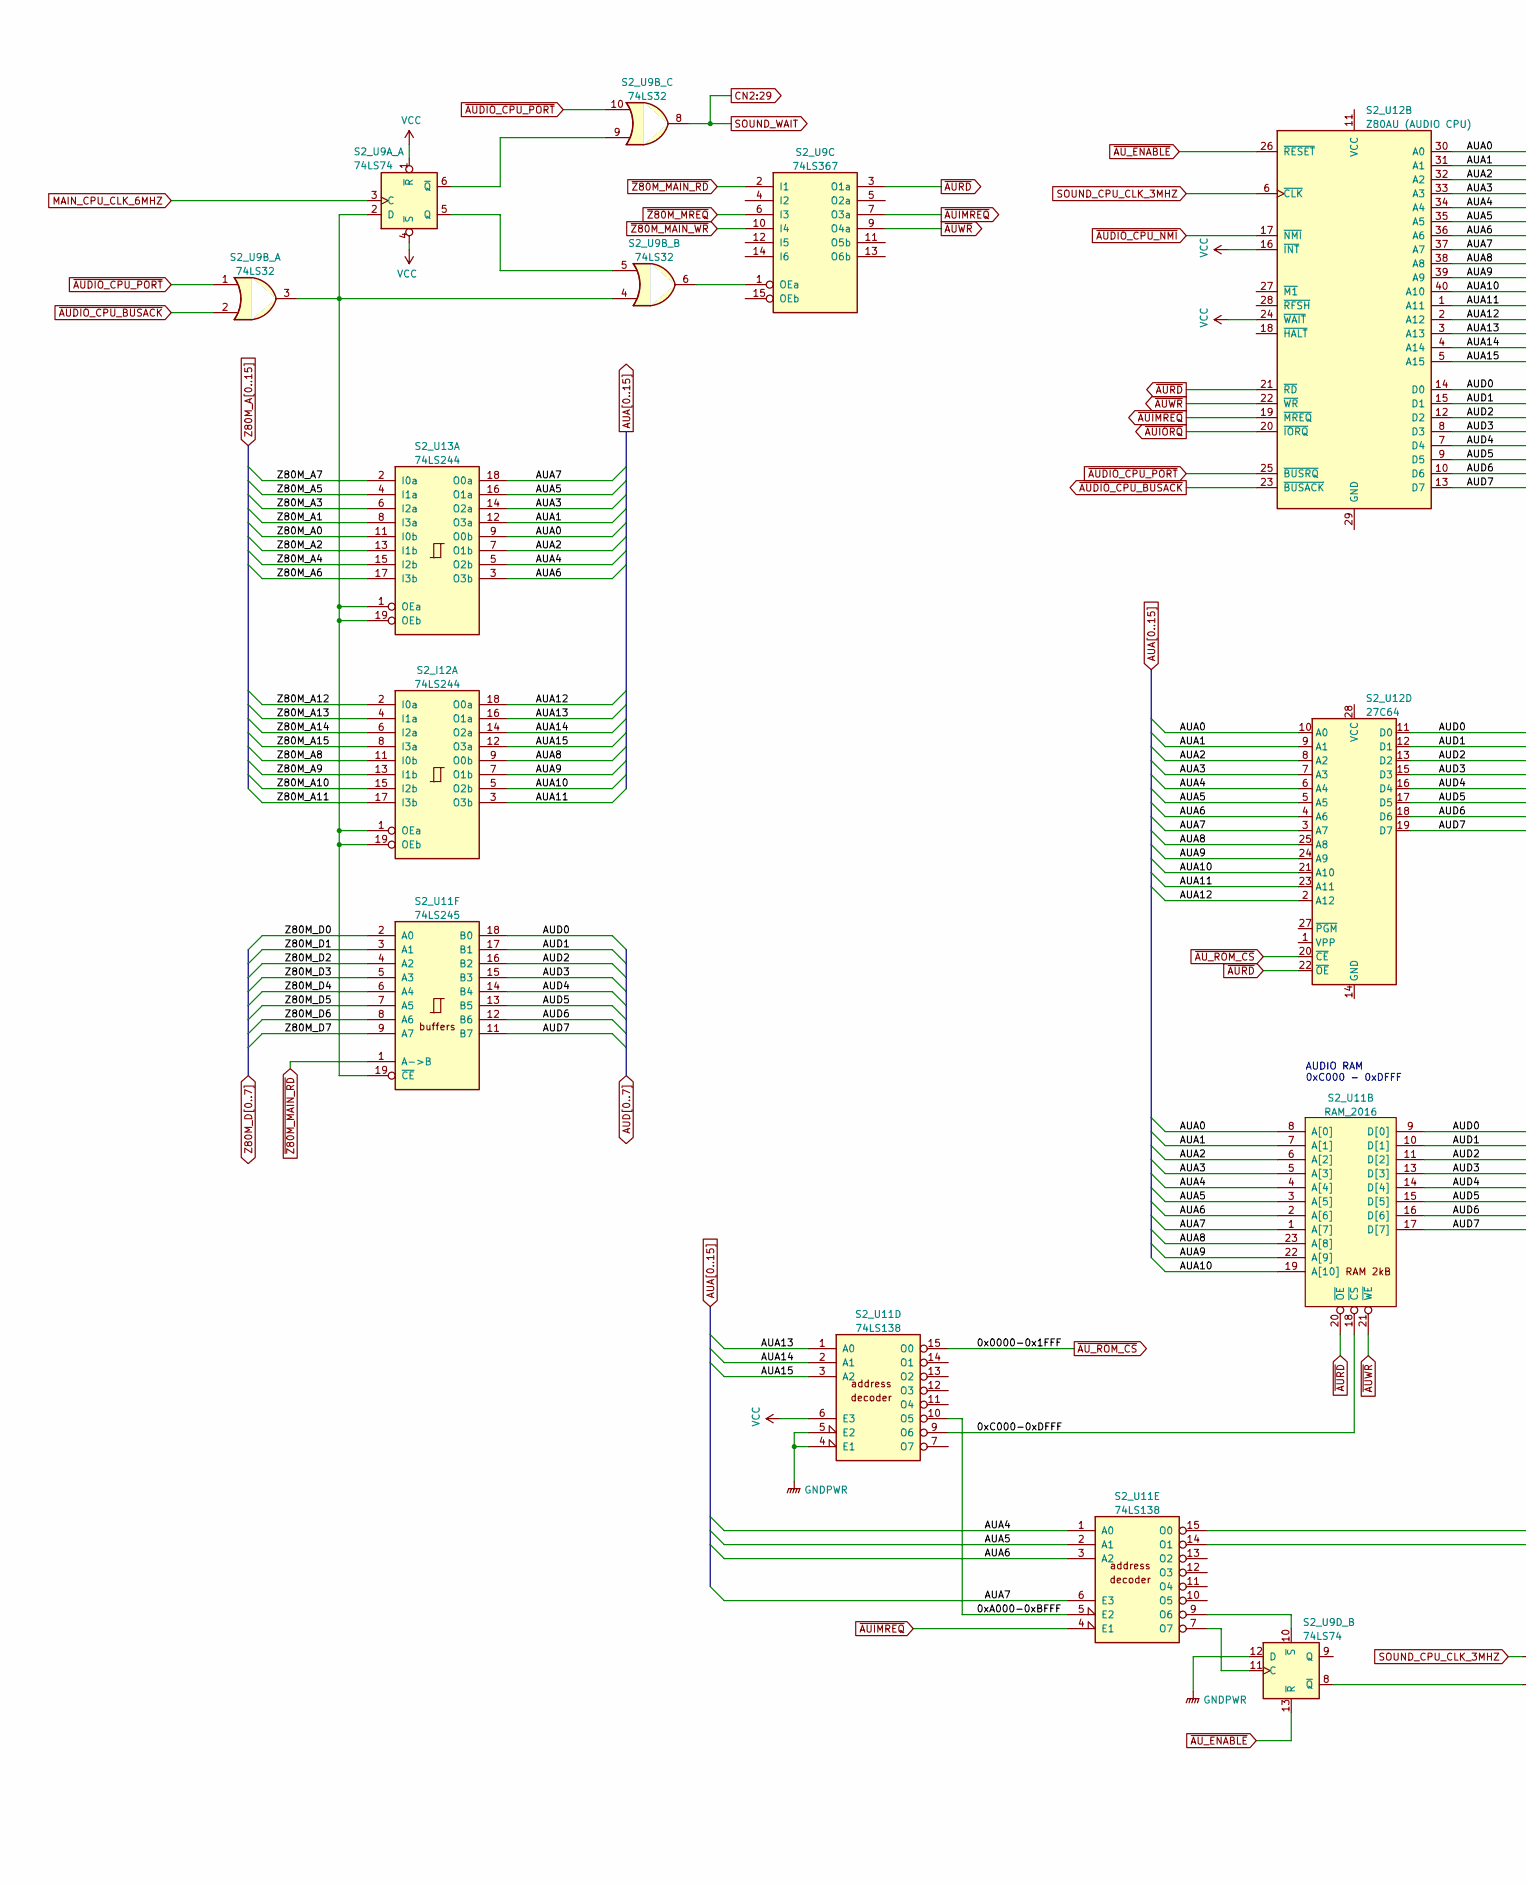
[picture p19: schematic aucpu.kicad_sch, part in row 1, column 1]

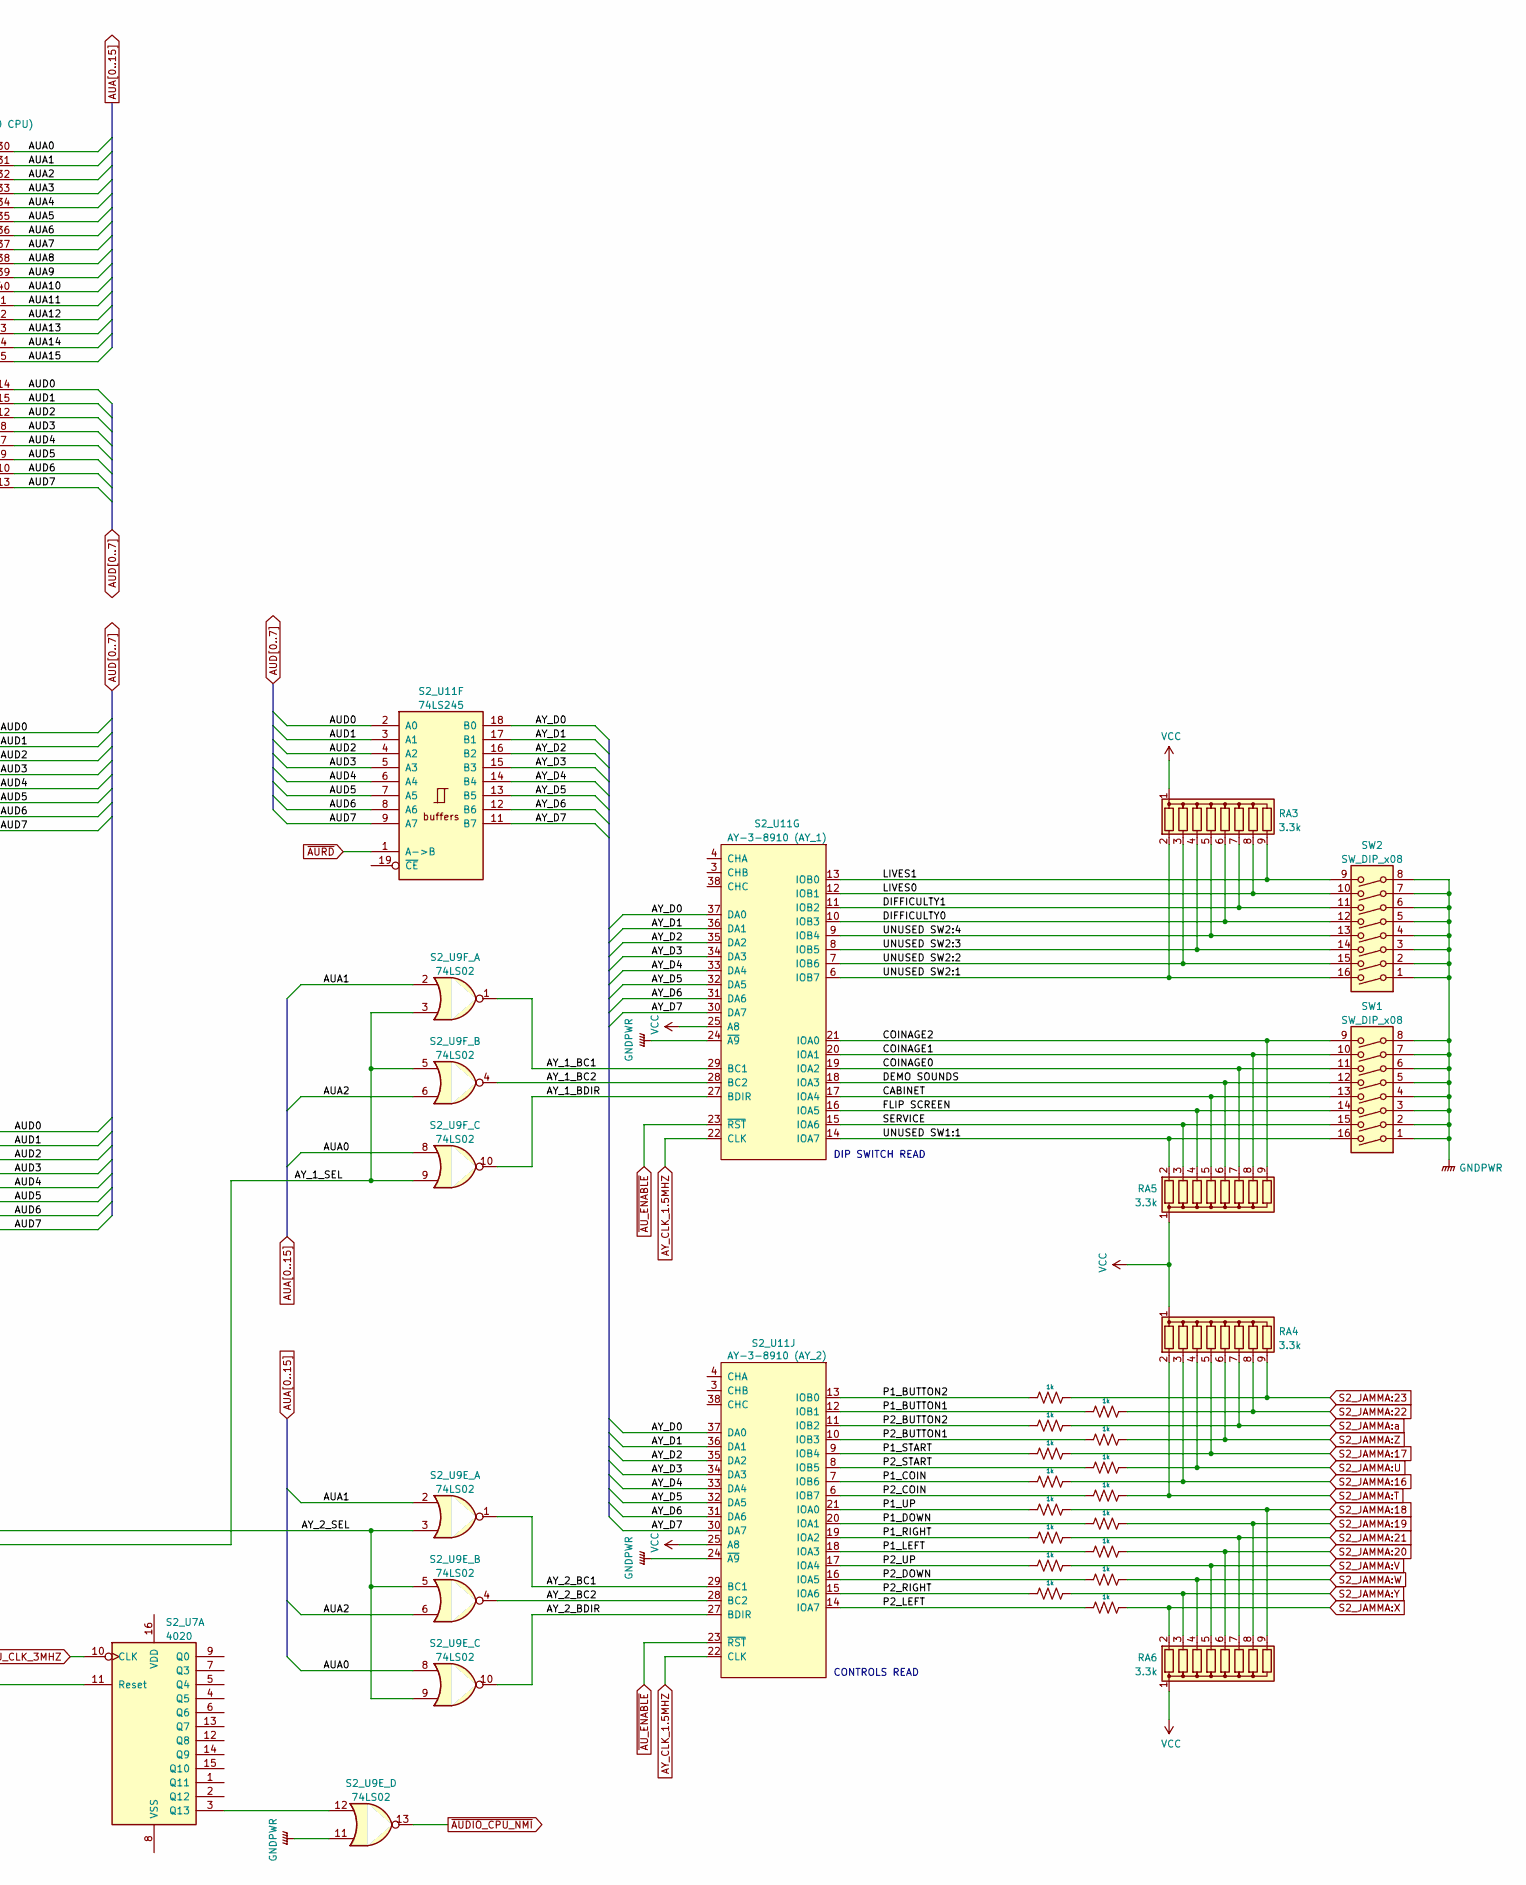
[picture p20: schematic aucpu.kicad_sch, part in row 1, column 2]

Parts:
RA3, RA4, RA5, RA6: 3.3k; R_Array_SIP9
S2_I12A, S2_U13A: 74LS244
S2_U7A: 4020
S2_U9A_, S2_U9D_: 74LS74
S2_U9B_: 74LS32
S2_U9C: 74LS367
S2_U9E_, S2_U9F_: 74LS02
S2_U11B: RAM_2016
S2_U11D, S2_U11E: 74LS138
S2_U11F: 74LS245
S2_U11G: AY-3-8910 (AY_1)
S2_U11J: AY-3-8910 (AY_2)
S2_U12B: Z80AU (AUDIO CPU)
S2_U12D: 27C64; DIP-28_W15.24mm
SW1, SW2: SW_DIP_x08

Connections:
0xA000-0xBFFF: S2_U11D.10 (O5), S2_U11E.5 (E2)
0xC000-0xDFFF: S2_U11B.18 (~CS), S2_U11D.9 (O6)
AUA0: S2_U9E_.8, S2_U9F_.8, S2_U11B.8 (A[0]), S2_U12B.30 (A0), S2_U12D.10 (A0), S2_U13A.9 (O0b)
AUA1: S2_U9E_.2, S2_U9F_.2, S2_U11B.7 (A[1]), S2_U12B.31 (A1), S2_U12D.9 (A1), S2_U13A.12 (O3a)
AUA2: S2_U9E_.6, S2_U9F_.6, S2_U11B.6 (A[2]), S2_U12B.32 (A2), S2_U12D.8 (A2), S2_U13A.7 (O1b)
AUA3: S2_U11B.5 (A[3]), S2_U12B.33 (A3), S2_U12D.7 (A3), S2_U13A.14 (O2a)
AUA4: S2_U11B.4 (A[4]), S2_U11E.1 (A0), S2_U12B.34 (A4), S2_U12D.6 (A4), S2_U13A.5 (O2b)
AUA5: S2_U11B.3 (A[5]), S2_U11E.2 (A1), S2_U12B.35 (A5), S2_U12D.5 (A5), S2_U13A.16 (O1a)
AUA6: S2_U11B.2 (A[6]), S2_U11E.3 (A2), S2_U12B.36 (A6), S2_U12D.4 (A6), S2_U13A.3 (O3b)
AUA7: S2_U11B.1 (A[7]), S2_U11E.6 (E3), S2_U12B.37 (A7), S2_U12D.3 (A7), S2_U13A.18 (O0a)
AUA8: S2_I12A.9 (O0b), S2_U11B.23 (A[8]), S2_U12B.38 (A8), S2_U12D.25 (A8)
AUA9: S2_I12A.7 (O1b), S2_U11B.22 (A[9]), S2_U12B.39 (A9), S2_U12D.24 (A9)
AUA10: S2_I12A.5 (O2b), S2_U11B.19 (A[10]), S2_U12B.40 (A10), S2_U12D.21 (A10)
AUA11: S2_I12A.3 (O3b), S2_U12B.1 (A11), S2_U12D.23 (A11)
AUA12: S2_I12A.18 (O0a), S2_U12B.2 (A12), S2_U12D.2 (A12)
AUA13: S2_I12A.16 (O1a), S2_U11D.1 (A0), S2_U12B.3 (A13)
AUA14: S2_I12A.14 (O2a), S2_U11D.2 (A1), S2_U12B.4 (A14)
AUA15: S2_I12A.12 (O3a), S2_U11D.3 (A2), S2_U12B.5 (A15)
AUD0: S2_U11B.9 (D[0]), S2_U11F.2 (A0), S2_U11F.18 (B0), S2_U12B.14 (D0), S2_U12D.11 (D0)
AUD1: S2_U11B.10 (D[1]), S2_U11F.3 (A1), S2_U11F.17 (B1), S2_U12B.15 (D1), S2_U12D.12 (D1)
AUD2: S2_U11B.11 (D[2]), S2_U11F.4 (A2), S2_U11F.16 (B2), S2_U12B.12 (D2), S2_U12D.13 (D2)
AUD3: S2_U11B.13 (D[3]), S2_U11F.5 (A3), S2_U11F.15 (B3), S2_U12B.8 (D3), S2_U12D.15 (D3)
AUD4: S2_U11B.14 (D[4]), S2_U11F.6 (A4), S2_U11F.14 (B4), S2_U12B.7 (D4), S2_U12D.16 (D4)
AUD5: S2_U11B.15 (D[5]), S2_U11F.7 (A5), S2_U11F.13 (B5), S2_U12B.9 (D5), S2_U12D.17 (D5)
AUD6: S2_U11B.16 (D[6]), S2_U11F.8 (A6), S2_U11F.12 (B6), S2_U12B.10 (D6), S2_U12D.18 (D6)
AUD7: S2_U11B.17 (D[7]), S2_U11F.9 (A7), S2_U11F.11 (B7), S2_U12B.13 (D7), S2_U12D.19 (D7)
AY_1_BC1: S2_U9F_.1, S2_U11G.29 (BC1)
AY_1_BC2: S2_U9F_.4, S2_U11G.28 (BC2)
AY_1_BDIR: S2_U9F_.10, S2_U11G.27 (BDIR)
AY_1_SEL: S2_U9F_.3, S2_U9F_.5, S2_U9F_.9, S2_U11E.14 (O1)
AY_2_BC1: S2_U9E_.1, S2_U11J.29 (BC1)
AY_2_BC2: S2_U9E_.4, S2_U11J.28 (BC2)
AY_2_BDIR: S2_U9E_.10, S2_U11J.27 (BDIR)
AY_2_SEL: S2_U9E_.3, S2_U9E_.5, S2_U9E_.9, S2_U11E.15 (O0)
AY_CLK_1.5MHZ: S2_U11G.22 (CLK), S2_U11J.22 (CLK)
AY_D0: S2_U11F.18 (B0), S2_U11G.37 (DA0), S2_U11J.37 (DA0)
AY_D1: S2_U11F.17 (B1), S2_U11G.36 (DA1), S2_U11J.36 (DA1)
AY_D2: S2_U11F.16 (B2), S2_U11G.35 (DA2), S2_U11J.35 (DA2)
AY_D3: S2_U11F.15 (B3), S2_U11G.34 (DA3), S2_U11J.34 (DA3)
AY_D4: S2_U11F.14 (B4), S2_U11G.33 (DA4), S2_U11J.33 (DA4)
AY_D5: S2_U11F.13 (B5), S2_U11G.32 (DA5), S2_U11J.32 (DA5)
AY_D6: S2_U11F.12 (B6), S2_U11G.31 (DA6), S2_U11J.31 (DA6)
AY_D7: S2_U11F.11 (B7), S2_U11G.30 (DA7), S2_U11J.30 (DA7)
CABINET: RA5.5 (R4), S2_U11G.17 (IOA4), SW1.13
CN2:29: S2_U9B_.8
COINAGE0: RA5.7 (R6), S2_U11G.19 (IOA2), SW1.11
COINAGE1: RA5.8 (R7), S2_U11G.20 (IOA1), SW1.10
COINAGE2: RA5.9 (R8), S2_U11G.21 (IOA0), SW1.9
DEMO SOUNDS: RA5.6 (R5), S2_U11G.18 (IOA3), SW1.12
DIFFICULTY0: RA3.6 (R5), S2_U11G.10 (IOB3), SW2.12
DIFFICULTY1: RA3.7 (R6), S2_U11G.11 (IOB2), SW2.11
FLIP SCREEN: RA5.4 (R3), S2_U11G.16 (IOA5), SW1.14
LIVES0: RA3.8 (R7), S2_U11G.12 (IOB1), SW2.10
LIVES1: RA3.9 (R8), S2_U11G.13 (IOB0), SW2.9
MAIN_CPU_CLK_6MHZ: S2_U9A_.3 (C)
unnamed: RA4.1 (common), RA5.1 (common)
unnamed: S2_I12A.1 (OEa), S2_I12A.19 (OEb), S2_U9A_.2 (D), S2_U9B_.3, S2_U9B_.4, S2_U11F.19 (~CE), S2_U13A.1 (OEa), S2_U13A.19 (OEb)
unnamed: S2_U7A.3 (Q13), S2_U9E_.12
unnamed: S2_U7A.11 (Reset), S2_U9D_.8 (~Q)
unnamed: S2_U9A_.5 (Q), S2_U9B_.5
unnamed: S2_U9A_.6 (~Q), S2_U9B_.9
unnamed: S2_U9B_.6, S2_U9C.1 (OEa)
unnamed: S2_U11D.4 (E1), S2_U11D.5 (E2)
unnamed: S2_U9D_.11 (C), S2_U11E.7 (O7)
unnamed: S2_U9D_.10 (~S), S2_U11E.9 (O6)
unnamed: SW1.1, SW1.2, SW1.3, SW1.4, SW1.5, SW1.6, SW1.7, SW1.8, SW2.1, SW2.2, SW2.3, SW2.4, SW2.5, SW2.6, SW2.7, SW2.8
P1_BUTTON1: S2_U11J.12 (IOB1)
P1_BUTTON2: S2_U11J.13 (IOB0)
P1_COIN: S2_U11J.7 (IOB6)
P1_DOWN: S2_U11J.20 (IOA1)
P1_LEFT: S2_U11J.18 (IOA3)
P1_RIGHT: S2_U11J.19 (IOA2)
P1_START: S2_U11J.9 (IOB4)
P1_UP: S2_U11J.21 (IOA0)
P2_BUTTON1: S2_U11J.10 (IOB3)
P2_BUTTON2: S2_U11J.11 (IOB2)
P2_COIN: S2_U11J.6 (IOB7)
P2_DOWN: S2_U11J.16 (IOA5)
P2_LEFT: S2_U11J.14 (IOA7)
P2_RIGHT: S2_U11J.15 (IOA6)
P2_START: S2_U11J.8 (IOB5)
P2_UP: S2_U11J.17 (IOA4)
S2_JAMMA:16: RA4.3 (R2)
S2_JAMMA:17: RA4.5 (R4)
S2_JAMMA:18: RA6.9 (R8)
S2_JAMMA:19: RA6.8 (R7)
S2_JAMMA:20: RA6.6 (R5)
S2_JAMMA:21: RA6.7 (R6)
S2_JAMMA:22: RA4.8 (R7)
S2_JAMMA:23: RA4.9 (R8)
S2_JAMMA:T: RA4.2 (R1)
S2_JAMMA:U: RA4.4 (R3)
S2_JAMMA:V: RA6.5 (R4)
S2_JAMMA:W: RA6.4 (R3)
S2_JAMMA:X: RA6.2 (R1)
S2_JAMMA:Y: RA6.3 (R2)
S2_JAMMA:Z: RA4.6 (R5)
S2_JAMMA:a: RA4.7 (R6)
SERVICE: RA5.3 (R2), S2_U11G.15 (IOA6), SW1.15
SOUND_CPU_CLK_3MHZ: S2_U7A.10 (CLK), S2_U12B.6 (~CLK)
UNUSED SW1:1: RA5.2 (R1), S2_U11G.14 (IOA7), SW1.16
UNUSED SW2:1: RA3.2 (R1), S2_U11G.6 (IOB7), SW2.16
UNUSED SW2:2: RA3.3 (R2), S2_U11G.7 (IOB6), SW2.15
UNUSED SW2:3: RA3.4 (R3), S2_U11G.8 (IOB5), SW2.14
UNUSED SW2:4: RA3.5 (R4), S2_U11G.9 (IOB4), SW2.13
Z80M_A0: S2_U13A.11 (I0b)
Z80M_A1: S2_U13A.8 (I3a)
Z80M_A2: S2_U13A.13 (I1b)
Z80M_A3: S2_U13A.6 (I2a)
Z80M_A4: S2_U13A.15 (I2b)
Z80M_A5: S2_U13A.4 (I1a)
Z80M_A6: S2_U13A.17 (I3b)
Z80M_A7: S2_U13A.2 (I0a)
Z80M_A8: S2_I12A.11 (I0b)
Z80M_A9: S2_I12A.13 (I1b)
Z80M_A10: S2_I12A.15 (I2b)
Z80M_A11: S2_I12A.17 (I3b)
Z80M_A12: S2_I12A.2 (I0a)
Z80M_A13: S2_I12A.4 (I1a)
Z80M_A14: S2_I12A.6 (I2a)
Z80M_A15: S2_I12A.8 (I3a)
Z80M_D0: S2_U11F.2 (A0)
Z80M_D1: S2_U11F.3 (A1)
Z80M_D2: S2_U11F.4 (A2)
Z80M_D3: S2_U11F.5 (A3)
Z80M_D4: S2_U11F.6 (A4)
Z80M_D5: S2_U11F.7 (A5)
Z80M_D6: S2_U11F.8 (A6)
Z80M_D7: S2_U11F.9 (A7)
~AUDIO_CPU_BUSACK: S2_U9B_.2, S2_U12B.23 (~BUSACK)
~AUDIO_CPU_NMI: S2_U9E_.13, S2_U12B.17 (~NMI)
~AUDIO_CPU_PORT: S2_U9B_.1, S2_U9B_.10, S2_U12B.25 (~BUSRQ)
~AUIMREQ: S2_U9C.7 (O3a), S2_U11E.4 (E1), S2_U12B.19 (~MREQ)
~AUIORQ: S2_U12B.20 (~IORQ)
~AURD: S2_U9C.3 (O1a), S2_U11B.20 (~OE), S2_U11F.1 (A->B), S2_U12B.21 (~RD), S2_U12D.22 (~OE)
~AUWR: S2_U9C.9 (O4a), S2_U11B.21 (~WE), S2_U12B.22 (~WR)
~AU_ENABLE: S2_U9D_.13 (~R), S2_U11G.23 (~RST), S2_U11J.23 (~RST), S2_U12B.26 (~RESET)
~AU_ROM_CS: S2_U11D.15 (O0), S2_U12D.20 (~CE)
~Z80M_MAIN_RD: S2_U9C.2 (I1), S2_U11F.1 (A->B)
~Z80M_MAIN_WR: S2_U9C.10 (I4)
~Z80M_MREQ: S2_U9C.6 (I3)

Notes on the sheet:
AUDIO RAM 0xC000 - 0xDFFF
CONTROLS READ
DIP SWITCH READ
