MiSTer-devel/Arcade-SlapFight_MiSTer/docs/KiCAD/SlapFight/background.kicad_sch

## KiCad design docs/KiCAD/SlapFight/background.kicad_sch (2022-12-26)

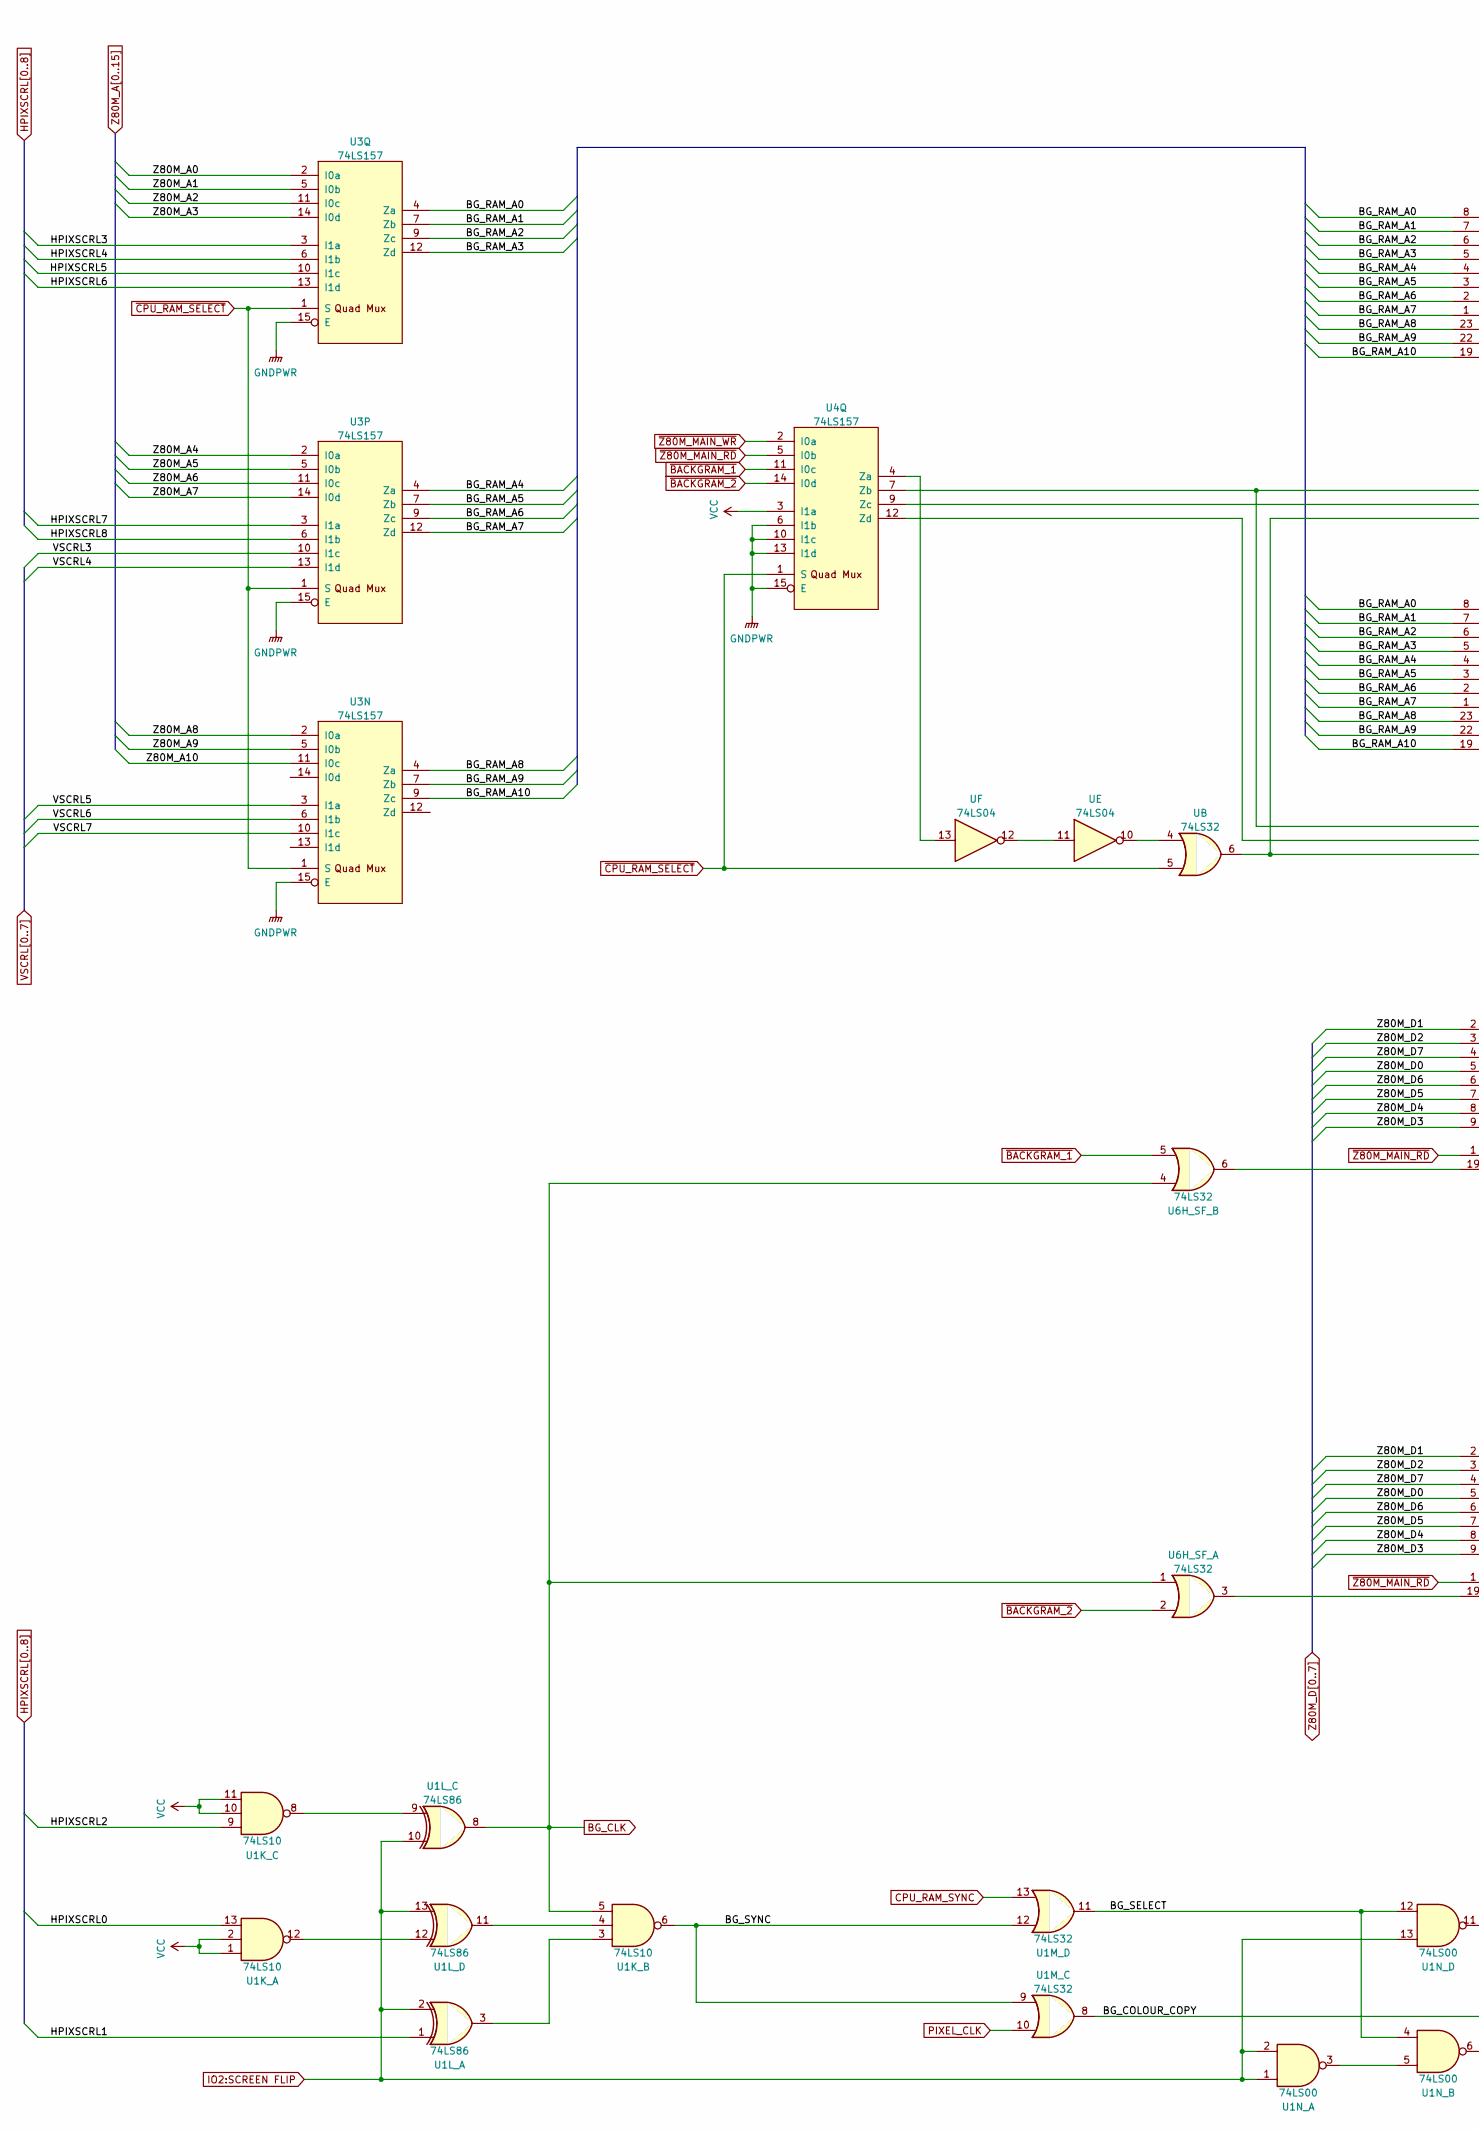
[picture p21: schematic background.kicad_sch, part in row 1, column 1]

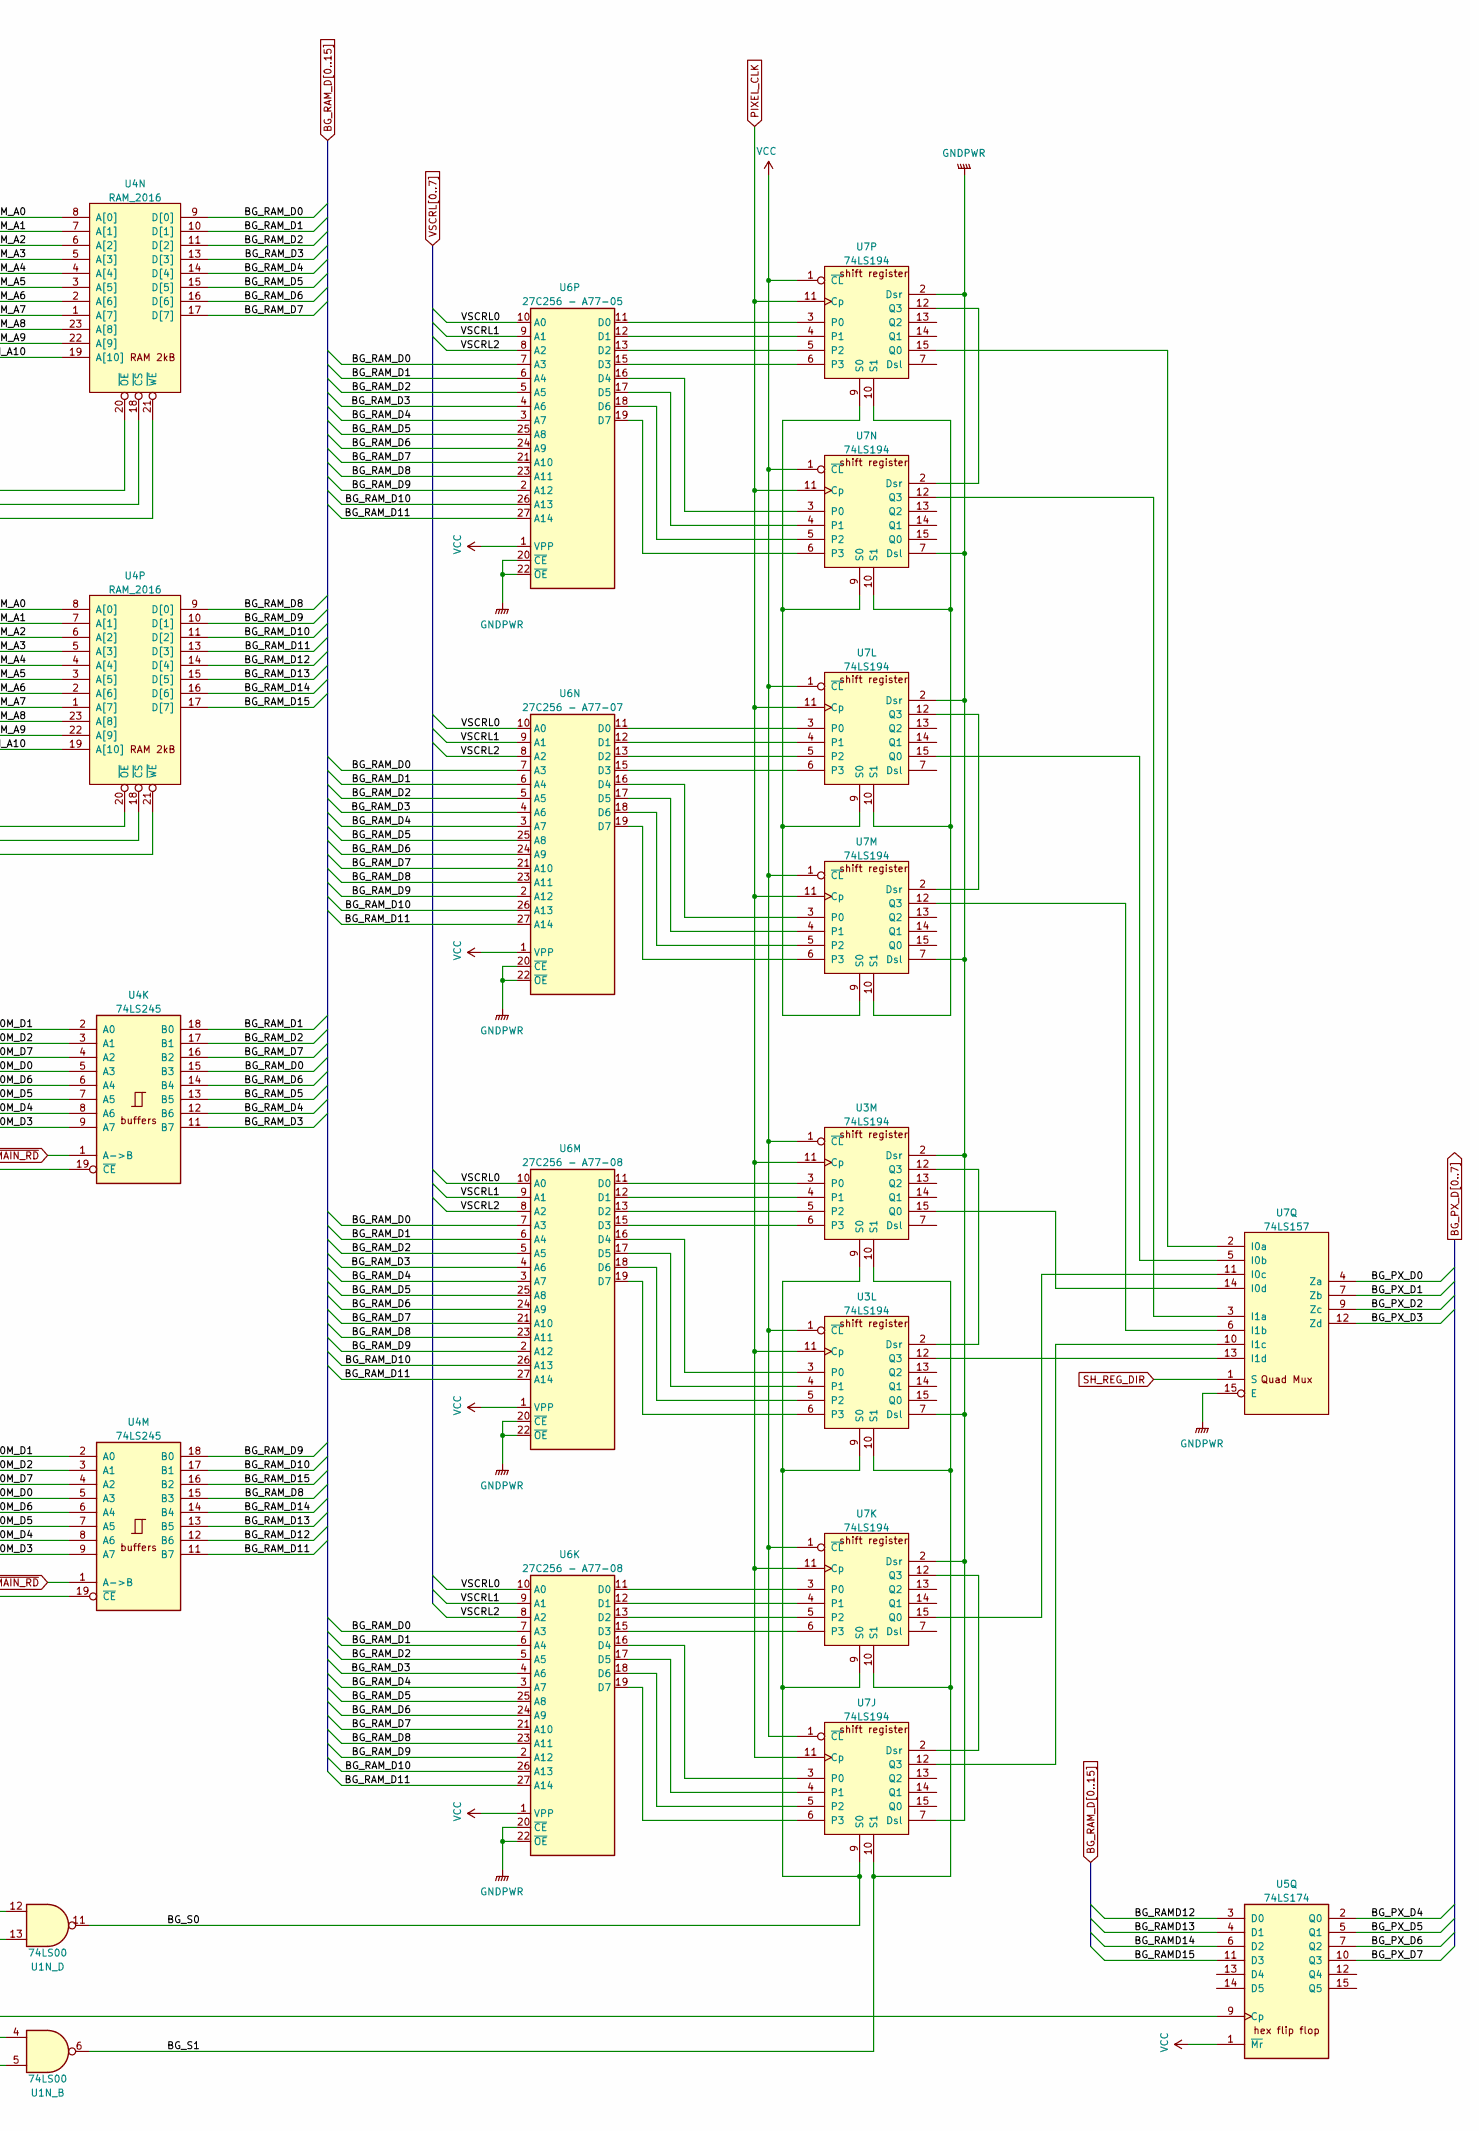
[picture p22: schematic background.kicad_sch, part in row 1, column 2]

Parts:
U: 74LS04
U1K_: 74LS10
U1L_: 74LS86
U1M_, U6H_SF_: 74LS32
U1N_: 74LS00
U3L, U3M, U7J, U7K, U7L, U7M, U7N, U7P: 74LS194
U3N, U3P, U3Q, U4Q, U7Q: 74LS157
U4K, U4M: 74LS245
U4N, U4P: RAM_2016
U5Q: 74LS174
U6K, U6M: 27C256 - A77-08; DIP-28_W15.24mm
U6N: 27C256 - A77-07; DIP-28_W15.24mm
U6P: 27C256 - A77-05; DIP-28_W15.24mm

Connections:
BG_CLK: U1K_.5, U1L_.8, U6H_SF_.1, U6H_SF_.4
BG_COLOUR_COPY: U1M_.8, U5Q.9 (Cp)
BG_PX_D0: U7Q.4 (Za)
BG_PX_D1: U7Q.7 (Zb)
BG_PX_D2: U7Q.9 (Zc)
BG_PX_D3: U7Q.12 (Zd)
BG_PX_D4: U5Q.2 (Q0)
BG_PX_D5: U5Q.5 (Q1)
BG_PX_D6: U5Q.7 (Q2)
BG_PX_D7: U5Q.10 (Q3)
BG_RAMD12: U5Q.3 (D0)
BG_RAMD13: U5Q.4 (D1)
BG_RAMD14: U5Q.6 (D2)
BG_RAMD15: U5Q.11 (D3)
BG_RAM_A0: U3Q.4 (Za), U4N.8 (A[0]), U4P.8 (A[0])
BG_RAM_A1: U3Q.7 (Zb), U4N.7 (A[1]), U4P.7 (A[1])
BG_RAM_A2: U3Q.9 (Zc), U4N.6 (A[2]), U4P.6 (A[2])
BG_RAM_A3: U3Q.12 (Zd), U4N.5 (A[3]), U4P.5 (A[3])
BG_RAM_A4: U3P.4 (Za), U4N.4 (A[4]), U4P.4 (A[4])
BG_RAM_A5: U3P.7 (Zb), U4N.3 (A[5]), U4P.3 (A[5])
BG_RAM_A6: U3P.9 (Zc), U4N.2 (A[6]), U4P.2 (A[6])
BG_RAM_A7: U3P.12 (Zd), U4N.1 (A[7]), U4P.1 (A[7])
BG_RAM_A8: U3N.4 (Za), U4N.23 (A[8]), U4P.23 (A[8])
BG_RAM_A9: U3N.7 (Zb), U4N.22 (A[9]), U4P.22 (A[9])
BG_RAM_A10: U3N.9 (Zc), U4N.19 (A[10]), U4P.19 (A[10])
BG_RAM_D0: U4K.15 (B3), U4N.9 (D[0]), U6K.7 (A3), U6M.7 (A3), U6N.7 (A3), U6P.7 (A3)
BG_RAM_D1: U4K.18 (B0), U4N.10 (D[1]), U6K.6 (A4), U6M.6 (A4), U6N.6 (A4), U6P.6 (A4)
BG_RAM_D2: U4K.17 (B1), U4N.11 (D[2]), U6K.5 (A5), U6M.5 (A5), U6N.5 (A5), U6P.5 (A5)
BG_RAM_D3: U4K.11 (B7), U4N.13 (D[3]), U6K.4 (A6), U6M.4 (A6), U6N.4 (A6), U6P.4 (A6)
BG_RAM_D4: U4K.12 (B6), U4N.14 (D[4]), U6K.3 (A7), U6M.3 (A7), U6N.3 (A7), U6P.3 (A7)
BG_RAM_D5: U4K.13 (B5), U4N.15 (D[5]), U6K.25 (A8), U6M.25 (A8), U6N.25 (A8), U6P.25 (A8)
BG_RAM_D6: U4K.14 (B4), U4N.16 (D[6]), U6K.24 (A9), U6M.24 (A9), U6N.24 (A9), U6P.24 (A9)
BG_RAM_D7: U4K.16 (B2), U4N.17 (D[7]), U6K.21 (A10), U6M.21 (A10), U6N.21 (A10), U6P.21 (A10)
BG_RAM_D8: U4M.15 (B3), U4P.9 (D[0]), U6K.23 (A11), U6M.23 (A11), U6N.23 (A11), U6P.23 (A11)
BG_RAM_D9: U4M.18 (B0), U4P.10 (D[1]), U6K.2 (A12), U6M.2 (A12), U6N.2 (A12), U6P.2 (A12)
BG_RAM_D10: U4M.17 (B1), U4P.11 (D[2]), U6K.26 (A13), U6M.26 (A13), U6N.26 (A13), U6P.26 (A13)
BG_RAM_D11: U4M.11 (B7), U4P.13 (D[3]), U6K.27 (A14), U6M.27 (A14), U6N.27 (A14), U6P.27 (A14)
BG_RAM_D12: U4M.12 (B6), U4P.14 (D[4])
BG_RAM_D13: U4M.13 (B5), U4P.15 (D[5])
BG_RAM_D14: U4M.14 (B4), U4P.16 (D[6])
BG_RAM_D15: U4M.16 (B2), U4P.17 (D[7])
BG_S0: U1N_.11, U3L.9 (S0), U3M.9 (S0), U7J.9 (S0), U7K.9 (S0)
BG_S1: U1N_.6, U3L.10 (S1), U3M.10 (S1), U7J.10 (S1), U7K.10 (S1)
BG_SELECT: U1M_.11, U1N_.4, U1N_.12
BG_SYNC: U1K_.6, U1M_.9, U1M_.12
CPU_RAM_SYNC: U1M_.13
HPIXSCRL0: U1K_.13
HPIXSCRL1: U1L_.1
HPIXSCRL2: U1K_.9
HPIXSCRL3: U3Q.3 (I1a)
HPIXSCRL4: U3Q.6 (I1b)
HPIXSCRL5: U3Q.10 (I1c)
HPIXSCRL6: U3Q.13 (I1d)
HPIXSCRL7: U3P.3 (I1a)
HPIXSCRL8: U3P.6 (I1b)
IO2:SCREEN FLIP: U1L_.2, U1L_.10, U1L_.13, U1N_.1, U1N_.2, U1N_.13
unnamed: U1K_.1, U1K_.2
unnamed: U1K_.3, U1L_.3
unnamed: U1K_.4, U1L_.11
unnamed: U1K_.8, U1L_.9
unnamed: U1K_.10, U1K_.11
unnamed: U1K_.12, U1L_.12
unnamed: U1N_.3, U1N_.5
unnamed: U3L.1 (~CL), U3M.1 (~CL), U7J.1 (~CL), U7K.1 (~CL), U7L.1 (~CL), U7M.1 (~CL), U7N.1 (~CL), U7P.1 (~CL)
unnamed: U3L.2 (Dsr), U3M.12 (Q3)
unnamed: U3L.3 (P0), U6M.16 (D4)
unnamed: U3L.4 (P1), U6M.17 (D5)
unnamed: U3L.5 (P2), U6M.18 (D6)
unnamed: U3L.6 (P3), U6M.19 (D7)
unnamed: U3L.7 (Dsl), U3M.2 (Dsr), U7J.7 (Dsl), U7K.2 (Dsr), U7L.2 (Dsr), U7M.7 (Dsl), U7N.7 (Dsl), U7P.2 (Dsr)
unnamed: U3L.12 (Q3), U7Q.13 (I1d)
unnamed: U3M.3 (P0), U6M.11 (D0)
unnamed: U3M.4 (P1), U6M.12 (D1)
unnamed: U3M.5 (P2), U6M.13 (D2)
unnamed: U3M.6 (P3), U6M.15 (D3)
unnamed: U3M.15 (Q0), U7Q.14 (I0d)
unnamed: U4K.19 (~CE), U6H_SF_.6
unnamed: U4M.19 (~CE), U6H_SF_.3
unnamed: U4N.18 (~CS), U4Q.9 (Zc)
unnamed: U4N.20 (~OE), U4P.20 (~OE), U4Q.7 (Zb)
unnamed: U4P.18 (~CS), U4Q.12 (Zd)
unnamed: U4Q.6 (I1b), U4Q.10 (I1c), U4Q.13 (I1d), U4Q.15 (E)
unnamed: U6K.11 (D0), U7K.3 (P0)
unnamed: U6K.12 (D1), U7K.4 (P1)
unnamed: U6K.13 (D2), U7K.5 (P2)
unnamed: U6K.15 (D3), U7K.6 (P3)
unnamed: U6K.16 (D4), U7J.3 (P0)
unnamed: U6K.17 (D5), U7J.4 (P1)
unnamed: U6K.18 (D6), U7J.5 (P2)
unnamed: U6K.19 (D7), U7J.6 (P3)
unnamed: U6K.20 (~CE), U6K.22 (~OE)
unnamed: U6M.20 (~CE), U6M.22 (~OE)
unnamed: U6N.11 (D0), U7L.3 (P0)
unnamed: U6N.12 (D1), U7L.4 (P1)
unnamed: U6N.13 (D2), U7L.5 (P2)
unnamed: U6N.15 (D3), U7L.6 (P3)
unnamed: U6N.16 (D4), U7M.3 (P0)
unnamed: U6N.17 (D5), U7M.4 (P1)
unnamed: U6N.18 (D6), U7M.5 (P2)
unnamed: U6N.19 (D7), U7M.6 (P3)
unnamed: U6N.20 (~CE), U6N.22 (~OE)
unnamed: U6P.11 (D0), U7P.3 (P0)
unnamed: U6P.12 (D1), U7P.4 (P1)
unnamed: U6P.13 (D2), U7P.5 (P2)
unnamed: U6P.15 (D3), U7P.6 (P3)
unnamed: U6P.16 (D4), U7N.3 (P0)
unnamed: U6P.17 (D5), U7N.4 (P1)
unnamed: U6P.18 (D6), U7N.5 (P2)
unnamed: U6P.19 (D7), U7N.6 (P3)
unnamed: U6P.20 (~CE), U6P.22 (~OE)
unnamed: U7J.2 (Dsr), U7K.12 (Q3)
unnamed: U7J.12 (Q3), U7Q.10 (I1c)
unnamed: U7K.15 (Q0), U7Q.11 (I0c)
unnamed: U7L.9 (S0), U7M.9 (S0), U7N.9 (S0), U7P.9 (S0)
unnamed: U7L.10 (S1), U7M.10 (S1), U7N.10 (S1), U7P.10 (S1)
unnamed: U7L.12 (Q3), U7M.2 (Dsr)
unnamed: U7L.15 (Q0), U7Q.5 (I0b)
unnamed: U7M.12 (Q3), U7Q.6 (I1b)
unnamed: U7N.2 (Dsr), U7P.12 (Q3)
unnamed: U7N.12 (Q3), U7Q.3 (I1a)
unnamed: U7P.15 (Q0), U7Q.2 (I0a)
unnamed: U.6, U4N.21 (~WE), U4P.21 (~WE)
unnamed: U.4, U.10
unnamed: U.11, U.12
unnamed: U.13, U4Q.4 (Za)
PIXEL_CLK: U1M_.10, U3L.11 (Cp), U3M.11 (Cp), U7J.11 (Cp), U7K.11 (Cp), U7L.11 (Cp), U7M.11 (Cp), U7N.11 (Cp), U7P.11 (Cp)
SH_REG_DIR: U7Q.1 (S)
VSCRL0: U6K.10 (A0), U6M.10 (A0), U6N.10 (A0), U6P.10 (A0)
VSCRL1: U6K.9 (A1), U6M.9 (A1), U6N.9 (A1), U6P.9 (A1)
VSCRL2: U6K.8 (A2), U6M.8 (A2), U6N.8 (A2), U6P.8 (A2)
VSCRL3: U3P.10 (I1c)
VSCRL4: U3P.13 (I1d)
VSCRL5: U3N.3 (I1a)
VSCRL6: U3N.6 (I1b)
VSCRL7: U3N.10 (I1c)
Z80M_A0: U3Q.2 (I0a)
Z80M_A1: U3Q.5 (I0b)
Z80M_A2: U3Q.11 (I0c)
Z80M_A3: U3Q.14 (I0d)
Z80M_A4: U3P.2 (I0a)
Z80M_A5: U3P.5 (I0b)
Z80M_A6: U3P.11 (I0c)
Z80M_A7: U3P.14 (I0d)
Z80M_A8: U3N.2 (I0a)
Z80M_A9: U3N.5 (I0b)
Z80M_A10: U3N.11 (I0c)
Z80M_D0: U4K.5 (A3), U4M.5 (A3)
Z80M_D1: U4K.2 (A0), U4M.2 (A0)
Z80M_D2: U4K.3 (A1), U4M.3 (A1)
Z80M_D3: U4K.9 (A7), U4M.9 (A7)
Z80M_D4: U4K.8 (A6), U4M.8 (A6)
Z80M_D5: U4K.7 (A5), U4M.7 (A5)
Z80M_D6: U4K.6 (A4), U4M.6 (A4)
Z80M_D7: U4K.4 (A2), U4M.4 (A2)
~BACKGRAM_1: U4Q.11 (I0c), U6H_SF_.5
~BACKGRAM_2: U4Q.14 (I0d), U6H_SF_.2
~CPU_RAM_SELECT: U.5, U3N.1 (S), U3P.1 (S), U3Q.1 (S), U4Q.1 (S)
~Z80M_MAIN_RD: U4K.1 (A->B), U4M.1 (A->B), U4Q.5 (I0b)
~Z80M_MAIN_WR: U4Q.2 (I0a)
