MiSTer-devel/Arcade-SlapFight_MiSTer/docs/KiCAD/SlapFight/clock.kicad_sch

## KiCad design docs/KiCAD/SlapFight/clock.kicad_sch (2022-12-26)

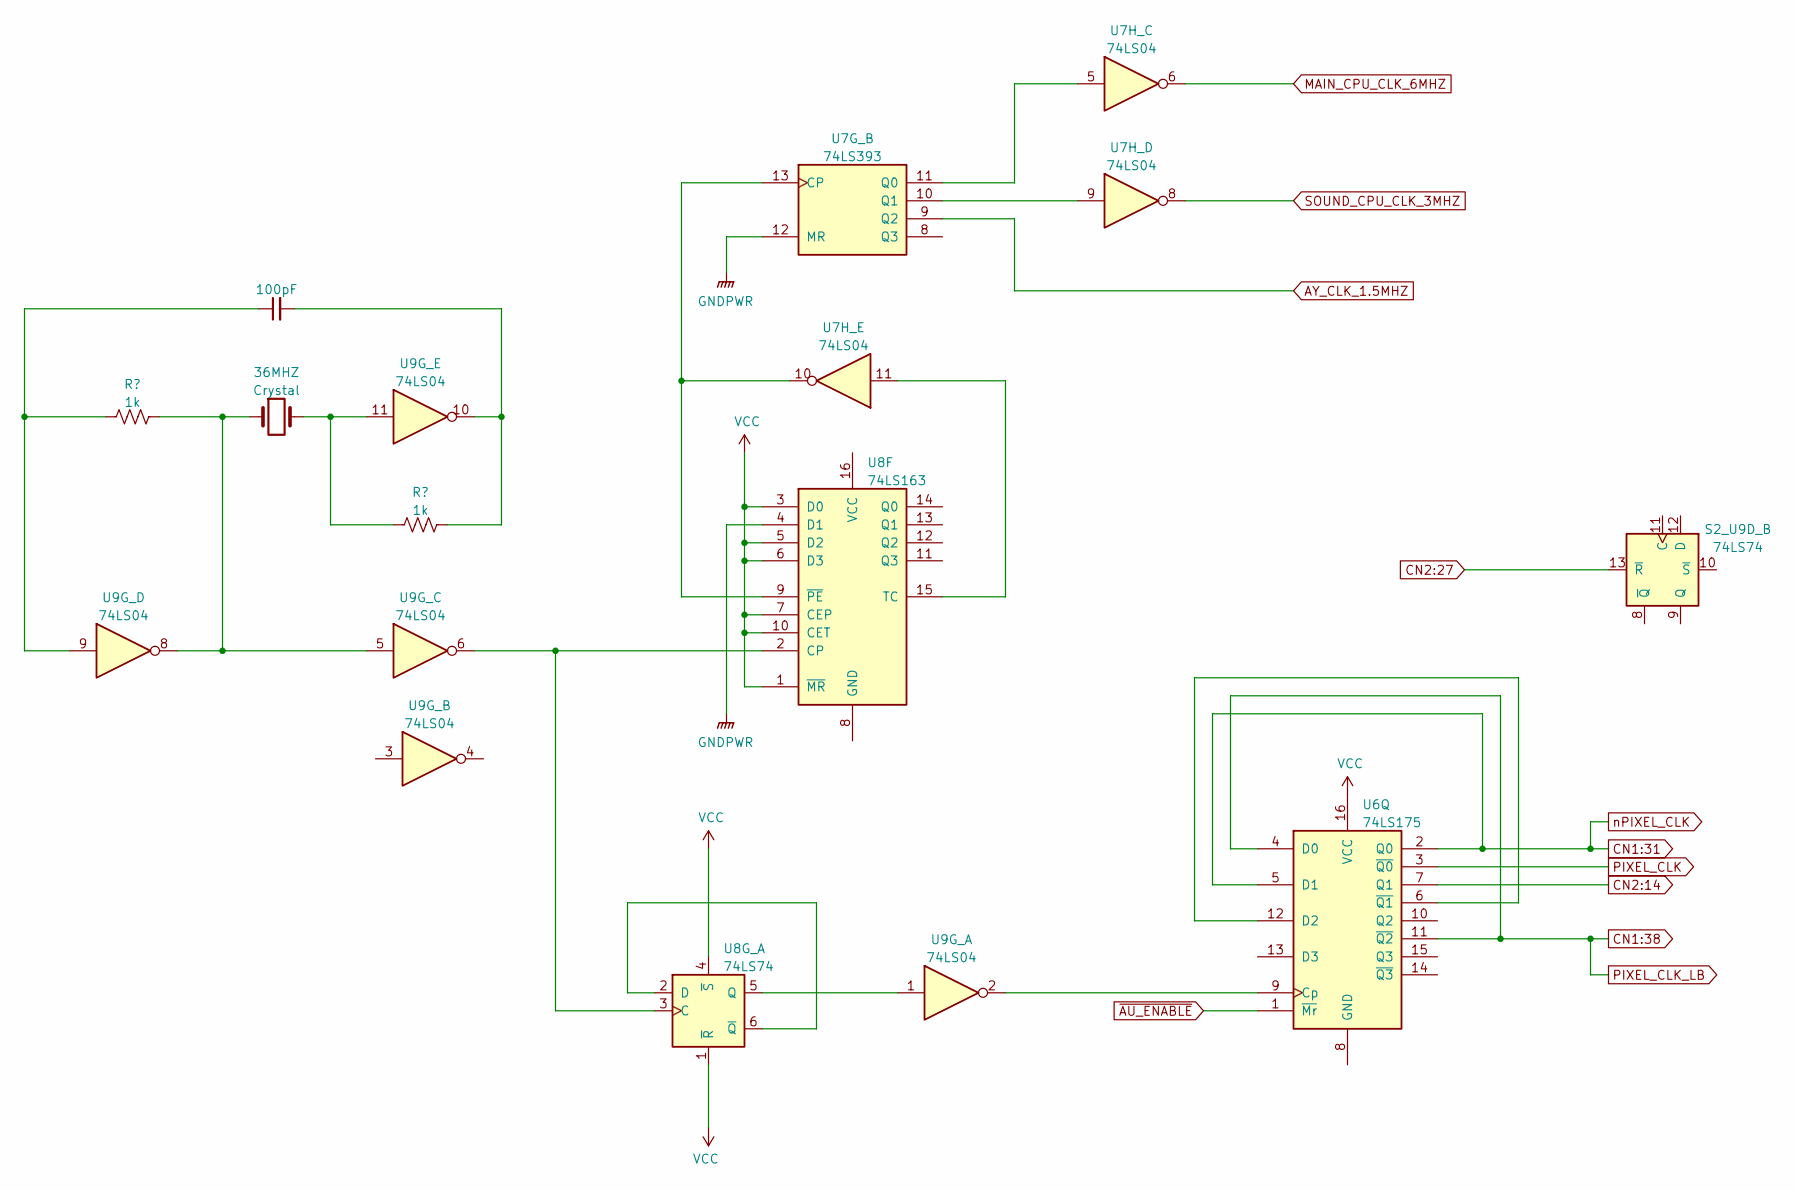
[picture p23: schematic clock.kicad_sch]

Parts:
36MHZ: Crystal
S2_U9D_: 74LS74
U6Q: 74LS175
U7G_: 74LS393
U7H_, U9G_: 74LS04
U8F: 74LS163
U8G_: 74LS74

Connections:
AY_CLK_1.5MHZ: U7G_.9 (Q2)
CN1:31: U6Q.2 (Q0), U6Q.5 (D1)
CN1:38: U6Q.4 (D0), U6Q.11 (~Q2)
CN2:14: U6Q.7 (Q1)
CN2:27: S2_U9D_.13 (~R)
GNDPWR: U7G_.12 (MR), U8F.4 (D1)
MAIN_CPU_CLK_6MHZ: U7H_.6
unnamed: 36MHZ.1, U9G_.5, U9G_.8
unnamed: 36MHZ.2, U9G_.11
unnamed: U6Q.9 (Cp), U9G_.2
unnamed: U6Q.6 (~Q1), U6Q.12 (D2)
unnamed: U7G_.10 (Q1), U7H_.9
unnamed: U7G_.11 (Q0), U7H_.5
unnamed: U7G_.13 (CP), U7H_.10, U8F.9 (~PE)
unnamed: U7H_.11, U8F.15 (TC)
unnamed: U8F.2 (CP), U8G_.3 (C), U9G_.6
unnamed: U8G_.2 (D), U8G_.6 (~Q)
unnamed: U8G_.5 (Q), U9G_.1
PIXEL_CLK: U6Q.3 (~Q0)
SOUND_CPU_CLK_3MHZ: U7H_.8
VCC: U6Q.16 (VCC), U8F.1 (~MR), U8F.3 (D0), U8F.5 (D2), U8F.6 (D3), U8F.7 (CEP), U8F.10 (CET), U8G_.1 (~R), U8G_.4 (~S)
~AU_ENABLE: U6Q.1 (~Mr)
