MiSTer-devel/Arcade-SlapFight_MiSTer/docs/KiCAD/SlapFight/cpu_wait.kicad_sch

## KiCad design docs/KiCAD/SlapFight/cpu_wait.kicad_sch (2022-12-28)

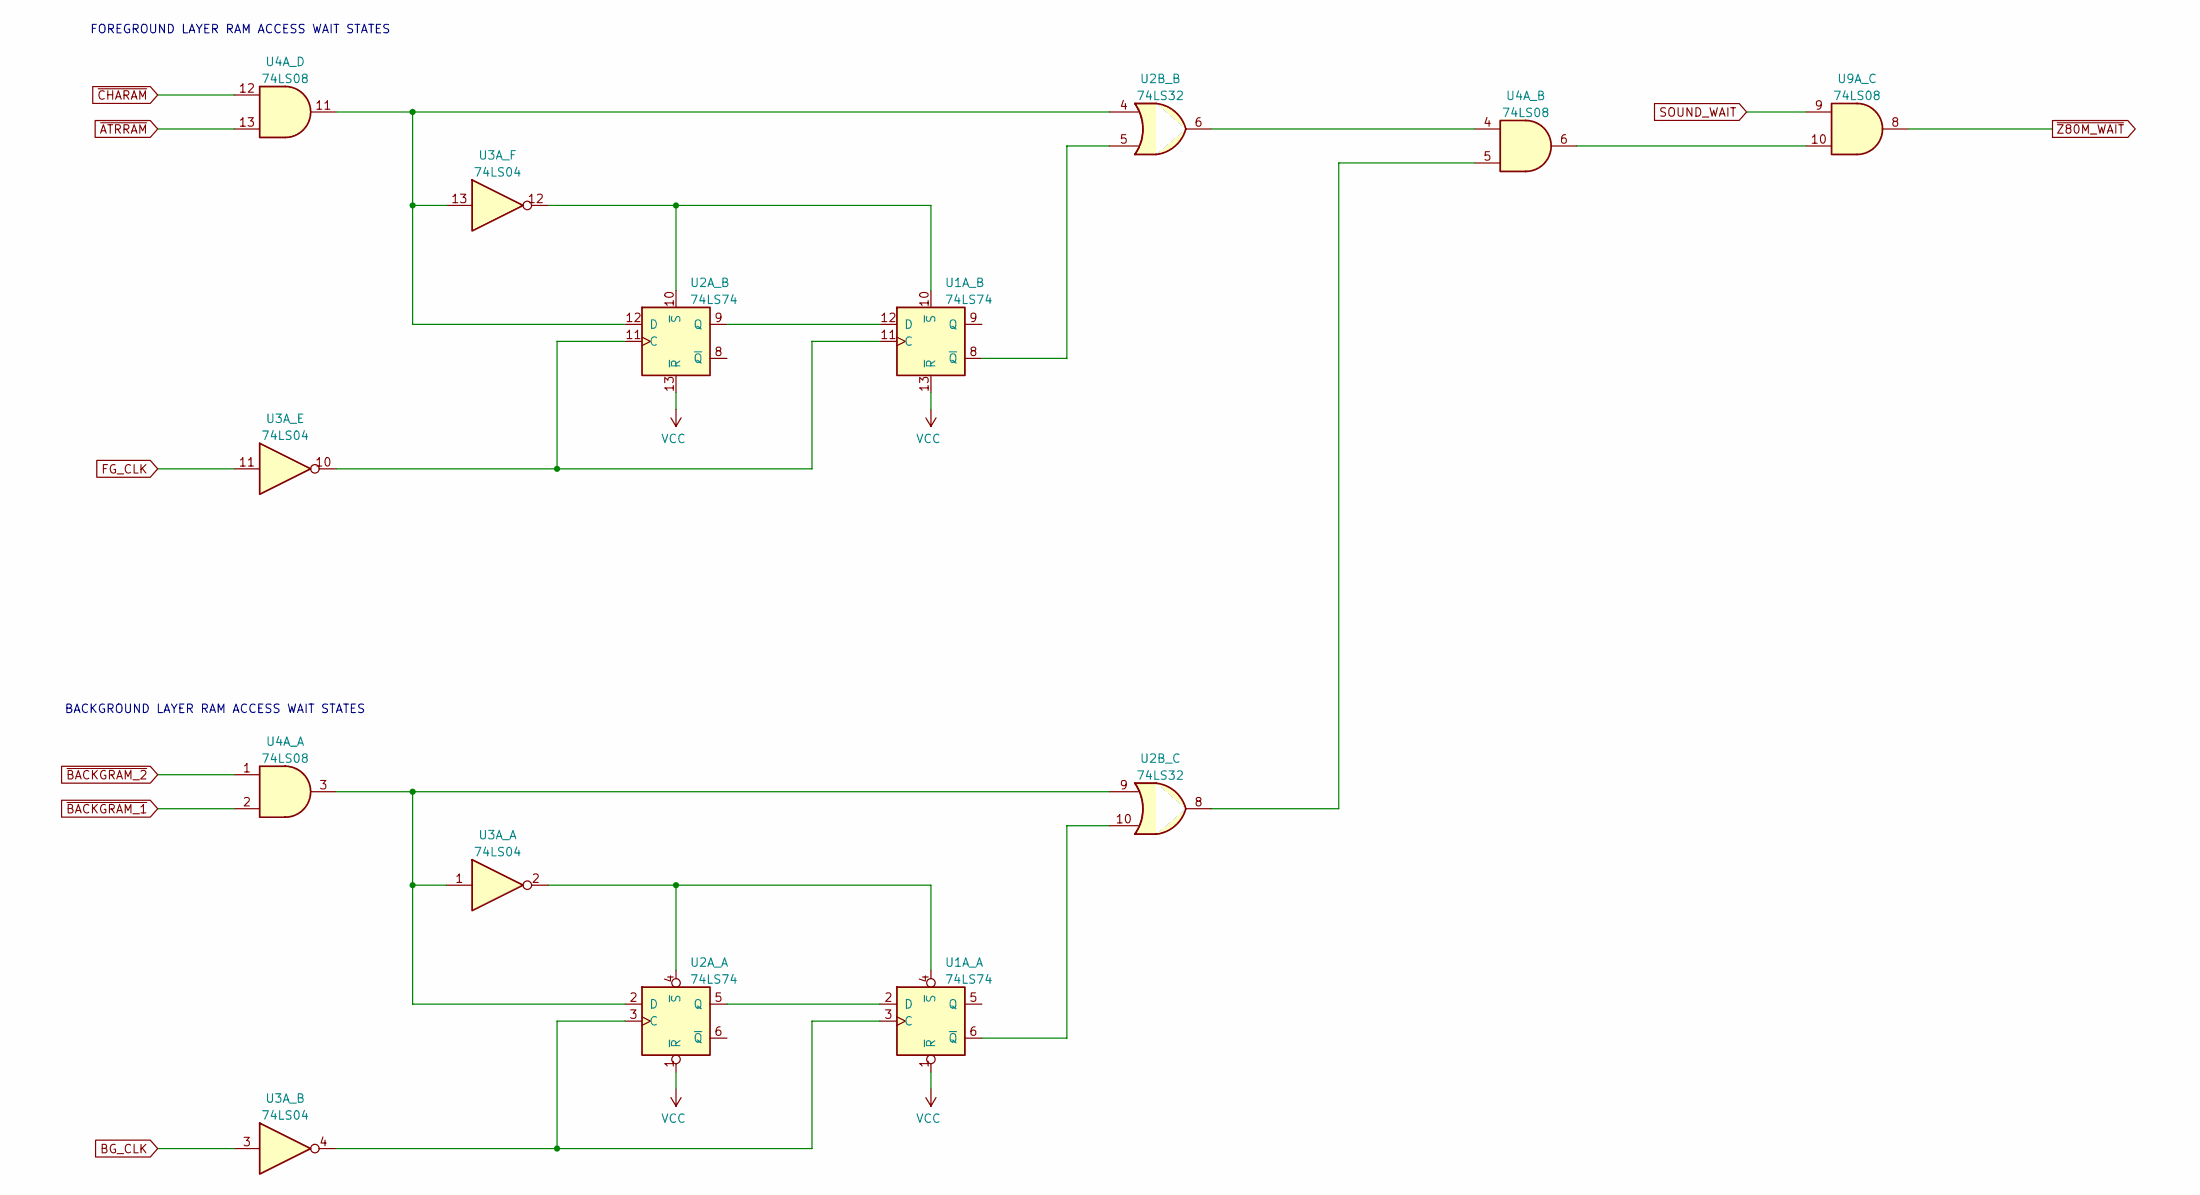
[picture p24: schematic cpu_wait.kicad_sch]

Parts:
U1A_, U2A_: 74LS74
U2B_: 74LS32
U3A_: 74LS04
U4A_, U9A_: 74LS08

Connections:
BG_CLK: U3A_.3
FG_CLK: U3A_.11
unnamed: U1A_.2 (D), U2A_.5 (Q)
unnamed: U1A_.3 (C), U2A_.3 (C), U3A_.4
unnamed: U1A_.4 (~S), U2A_.4 (~S), U3A_.2
unnamed: U1A_.6 (~Q), U2B_.10
unnamed: U1A_.8 (~Q), U2B_.5
unnamed: U1A_.10 (~S), U2A_.10 (~S), U3A_.12
unnamed: U1A_.11 (C), U2A_.11 (C), U3A_.10
unnamed: U1A_.12 (D), U2A_.9 (Q)
unnamed: U2A_.2 (D), U2B_.9, U3A_.1, U4A_.3
unnamed: U2A_.12 (D), U2B_.4, U3A_.13, U4A_.11
unnamed: U2B_.6, U4A_.4
unnamed: U2B_.8, U4A_.5
unnamed: U4A_.6, U9A_.10
SOUND_WAIT: U9A_.9
~ATRRAM: U4A_.13
~BACKGRAM_1: U4A_.2
~BACKGRAM_2: U4A_.1
~CHARAM: U4A_.12
~Z80M_WAIT: U9A_.8

Notes on the sheet:
FOREGROUND LAYER RAM ACCESS WAIT STATES
BACKGROUND LAYER RAM ACCESS WAIT STATES
