MiSTer-devel/Arcade-SlapFight_MiSTer/docs/KiCAD/SlapFight/foreground.kicad_sch

## KiCad design docs/KiCAD/SlapFight/foreground.kicad_sch (2022-12-26)

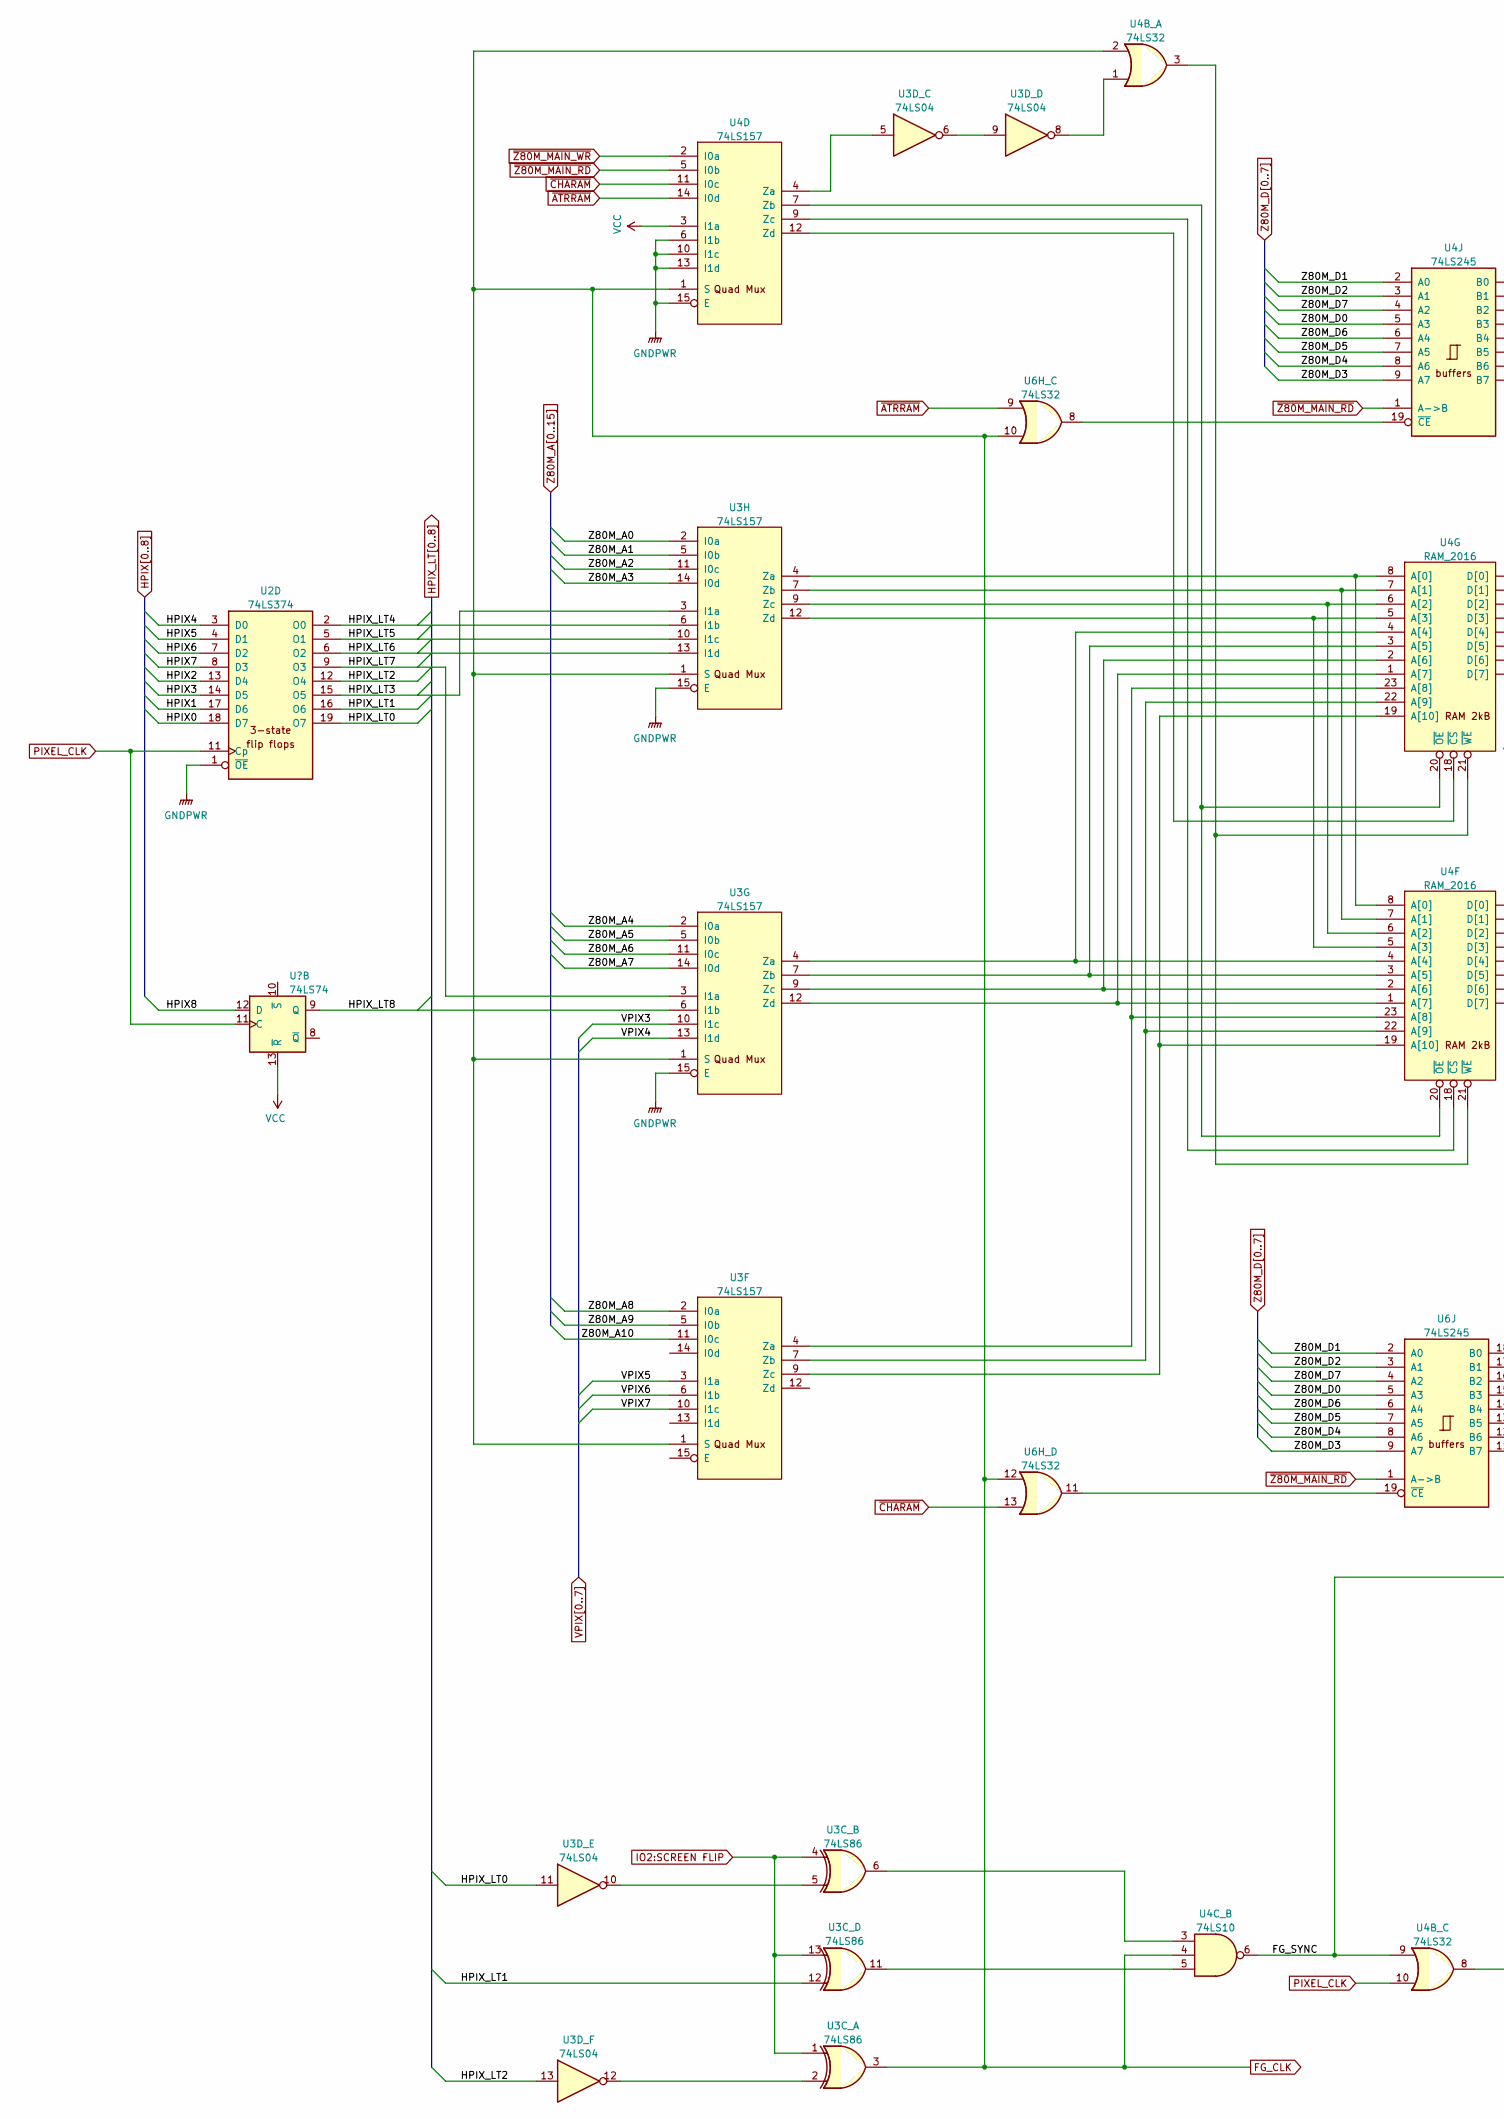
[picture p25: schematic foreground.kicad_sch, part in row 1, column 1]

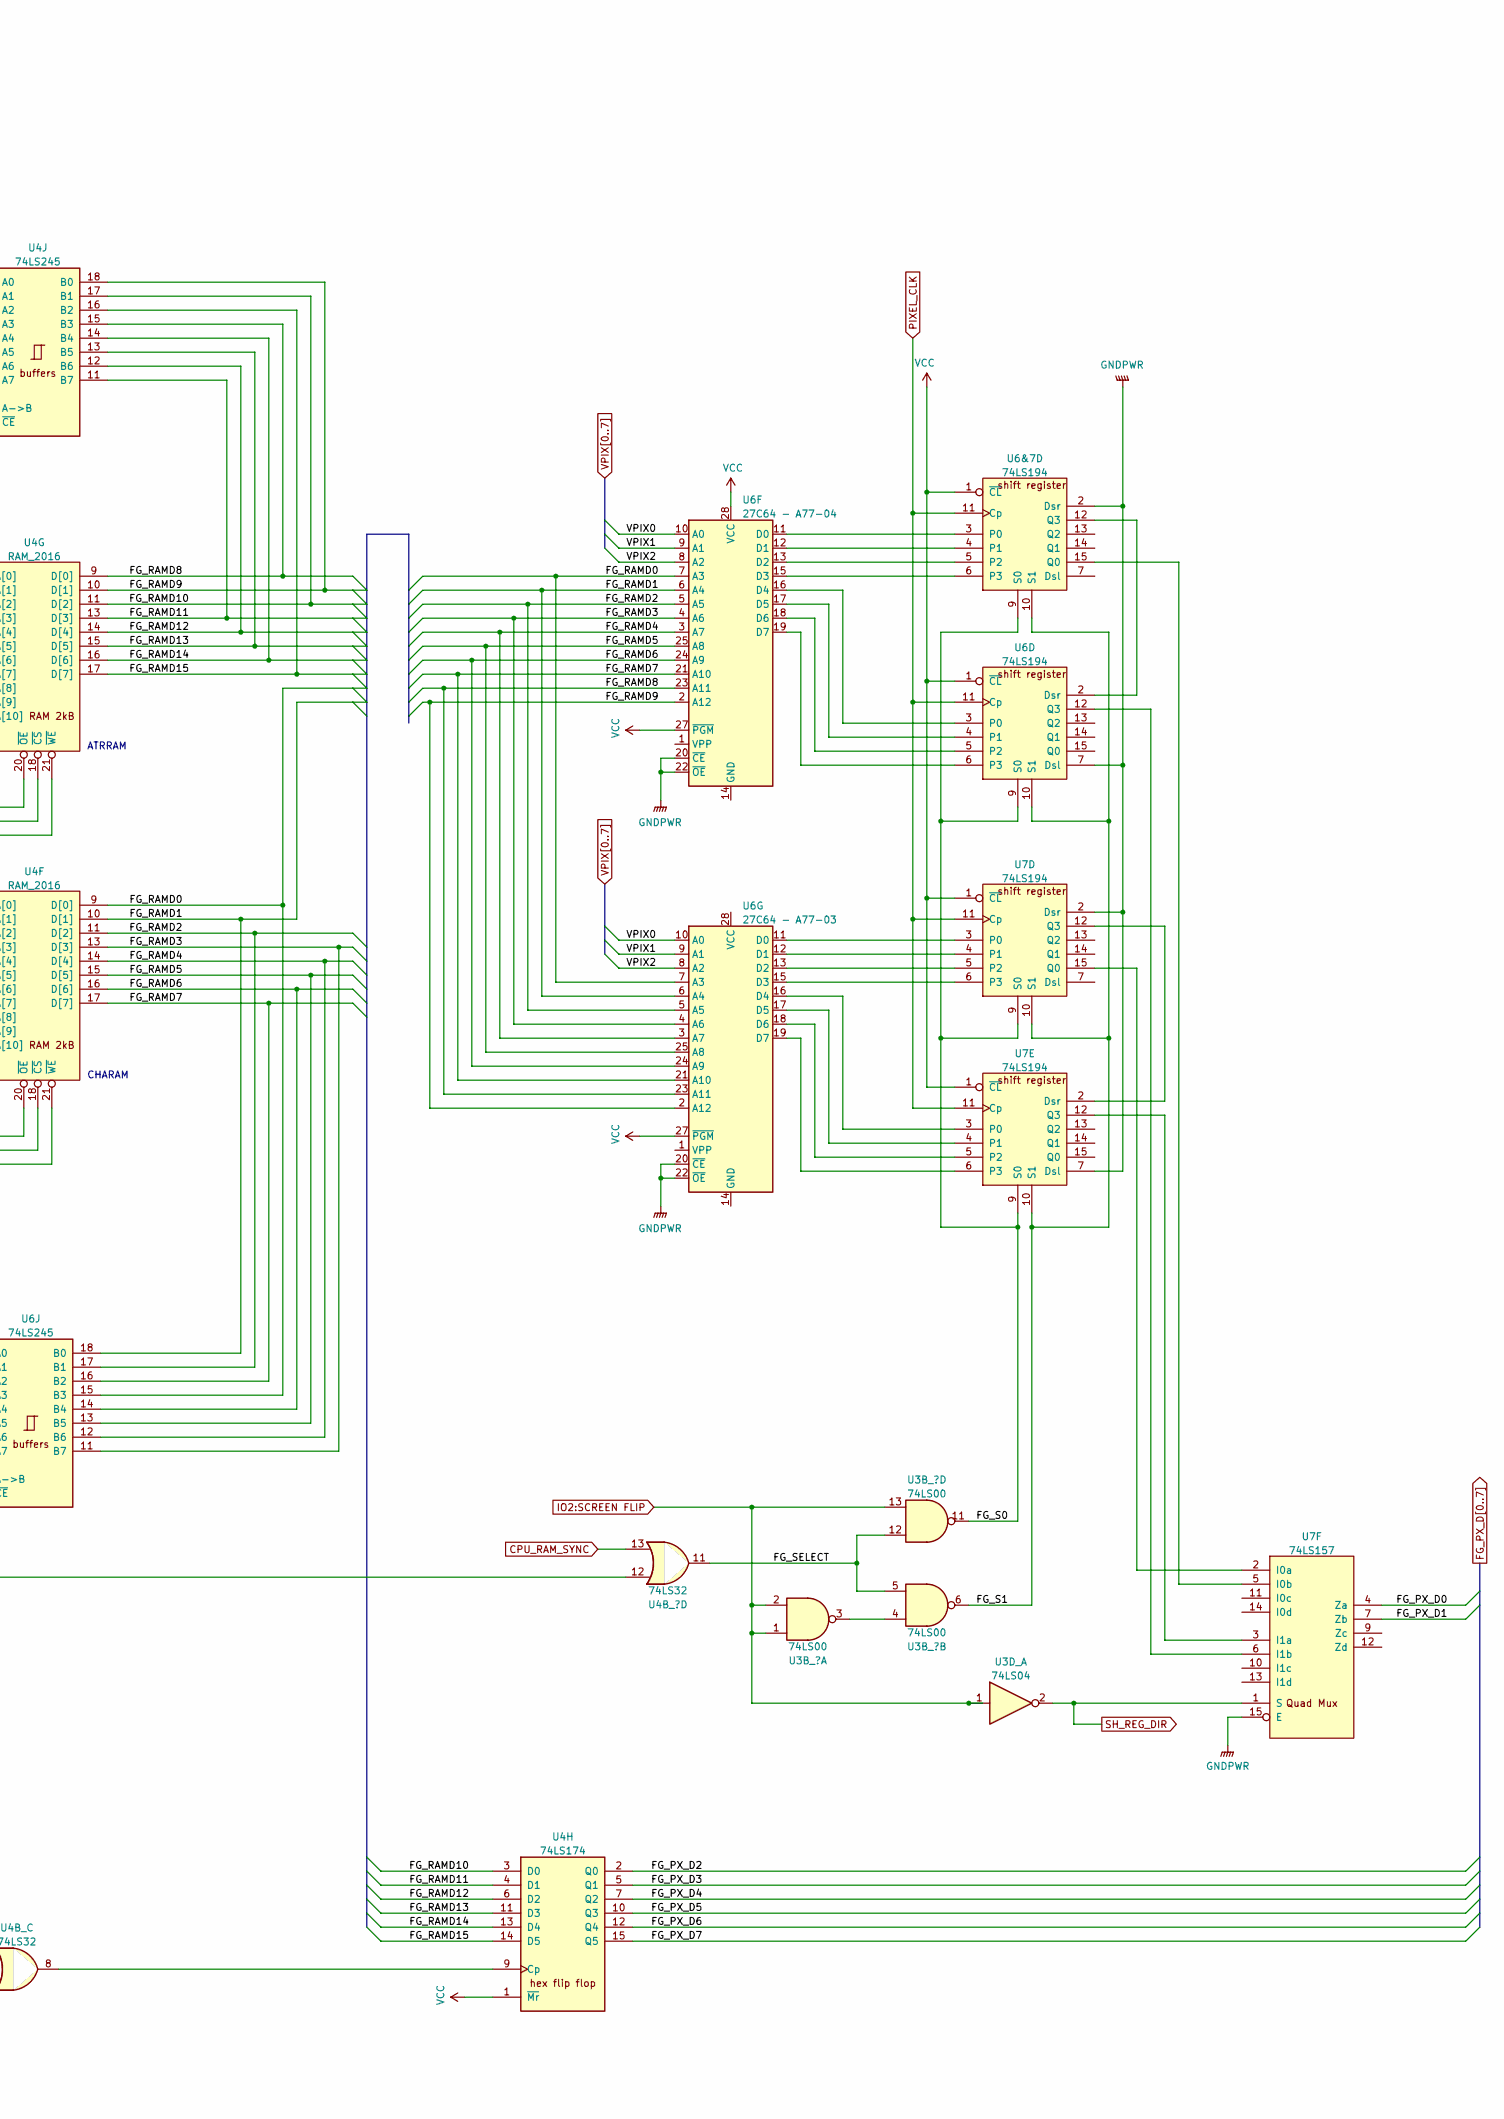
[picture p26: schematic foreground.kicad_sch, part in row 1, column 2]

Parts:
U2D: 74LS374
U3C_: 74LS86
U3D_: 74LS04
U3F, U3G, U3H, U4D, U7F: 74LS157
U4B_, U6H_: 74LS32
U4C_: 74LS10
U4F, U4G: RAM_2016
U4H: 74LS174
U4J, U6J: 74LS245
U6&7D, U6D, U7D, U7E: 74LS194
U6F: 27C64 - A77-04; DIP-28_W15.24mm
U6G: 27C64 - A77-03; DIP-28_W15.24mm

Connections:
FG_CLK: U3C_.3, U3F.1 (S), U3G.1 (S), U3H.1 (S), U4B_.2, U4C_.4, U4D.1 (S), U6H_.10, U6H_.12
FG_PX_D0: U7F.4 (Za)
FG_PX_D1: U7F.7 (Zb)
FG_PX_D2: U4H.2 (Q0)
FG_PX_D3: U4H.5 (Q1)
FG_PX_D4: U4H.7 (Q2)
FG_PX_D5: U4H.10 (Q3)
FG_PX_D6: U4H.12 (Q4)
FG_PX_D7: U4H.15 (Q5)
FG_RAMD0: U4F.9 (D[0]), U6F.7 (A3), U6G.7 (A3), U6J.15 (B3)
FG_RAMD1: U4F.10 (D[1]), U6F.6 (A4), U6G.6 (A4), U6J.18 (B0)
FG_RAMD2: U4F.11 (D[2]), U6F.5 (A5), U6G.5 (A5), U6J.17 (B1)
FG_RAMD3: U4F.13 (D[3]), U6F.4 (A6), U6G.4 (A6), U6J.11 (B7)
FG_RAMD4: U4F.14 (D[4]), U6F.3 (A7), U6G.3 (A7), U6J.12 (B6)
FG_RAMD5: U4F.15 (D[5]), U6F.25 (A8), U6G.25 (A8), U6J.13 (B5)
FG_RAMD6: U4F.16 (D[6]), U6F.24 (A9), U6G.24 (A9), U6J.14 (B4)
FG_RAMD7: U4F.17 (D[7]), U6F.21 (A10), U6G.21 (A10), U6J.16 (B2)
FG_RAMD8: U4G.9 (D[0]), U4J.15 (B3), U6F.23 (A11), U6G.23 (A11)
FG_RAMD9: U4G.10 (D[1]), U4J.18 (B0), U6F.2 (A12), U6G.2 (A12)
FG_RAMD10: U4G.11 (D[2]), U4H.3 (D0), U4J.17 (B1)
FG_RAMD11: U4G.13 (D[3]), U4H.4 (D1), U4J.11 (B7)
FG_RAMD12: U4G.14 (D[4]), U4H.6 (D2), U4J.12 (B6)
FG_RAMD13: U4G.15 (D[5]), U4H.11 (D3), U4J.13 (B5)
FG_RAMD14: U4G.16 (D[6]), U4H.13 (D4), U4J.14 (B4)
FG_RAMD15: U4G.17 (D[7]), U4H.14 (D5), U4J.16 (B2)
FG_S0: U6&7D.9 (S0), U6D.9 (S0), U7D.9 (S0), U7E.9 (S0)
FG_S1: U6&7D.10 (S1), U6D.10 (S1), U7D.10 (S1), U7E.10 (S1)
FG_SYNC: U4B_.9, U4C_.6
GNDPWR: U2D.1 (~OE), U3G.15 (E), U3H.15 (E), U4D.6 (I1b), U4D.10 (I1c), U4D.13 (I1d), U4D.15 (E), U6&7D.2 (Dsr), U6D.7 (Dsl), U6G.20 (~CE), U6G.22 (~OE), U7D.2 (Dsr), U7E.7 (Dsl), U7F.15 (E)
HPIX0: U2D.18 (D7)
HPIX1: U2D.17 (D6)
HPIX2: U2D.13 (D4)
HPIX3: U2D.14 (D5)
HPIX4: U2D.3 (D0)
HPIX5: U2D.4 (D1)
HPIX6: U2D.7 (D2)
HPIX7: U2D.8 (D3)
HPIX_LT0: U2D.19 (O7), U3D_.11
HPIX_LT1: U2D.16 (O6), U3C_.12
HPIX_LT2: U2D.12 (O4), U3D_.13
HPIX_LT3: U2D.15 (O5), U3H.3 (I1a)
HPIX_LT4: U2D.2 (O0), U3H.6 (I1b)
HPIX_LT5: U2D.5 (O1), U3H.10 (I1c)
HPIX_LT6: U2D.6 (O2), U3H.13 (I1d)
HPIX_LT7: U2D.9 (O3), U3G.3 (I1a)
HPIX_LT8: U3G.6 (I1b)
IO2:SCREEN FLIP: U3C_.1, U3C_.4, U3C_.13, U3D_.1
unnamed: U3C_.2, U3D_.12
unnamed: U3C_.5, U3D_.10
unnamed: U3C_.6, U4C_.3
unnamed: U3C_.11, U4C_.5
unnamed: U3D_.5, U4D.4 (Za)
unnamed: U3D_.6, U3D_.9
unnamed: U3D_.8, U4B_.1
unnamed: U3F.4 (Za), U4F.23 (A[8]), U4G.23 (A[8])
unnamed: U3F.7 (Zb), U4F.22 (A[9]), U4G.22 (A[9])
unnamed: U3F.9 (Zc), U4F.19 (A[10]), U4G.19 (A[10])
unnamed: U3G.4 (Za), U4F.4 (A[4]), U4G.4 (A[4])
unnamed: U3G.7 (Zb), U4F.3 (A[5]), U4G.3 (A[5])
unnamed: U3G.9 (Zc), U4F.2 (A[6]), U4G.2 (A[6])
unnamed: U3G.12 (Zd), U4F.1 (A[7]), U4G.1 (A[7])
unnamed: U3H.4 (Za), U4F.8 (A[0]), U4G.8 (A[0])
unnamed: U3H.7 (Zb), U4F.7 (A[1]), U4G.7 (A[1])
unnamed: U3H.9 (Zc), U4F.6 (A[2]), U4G.6 (A[2])
unnamed: U3H.12 (Zd), U4F.5 (A[3]), U4G.5 (A[3])
unnamed: U4B_.3, U4F.21 (~WE), U4G.21 (~WE)
unnamed: U4B_.8, U4H.9 (Cp)
unnamed: U4D.7 (Zb), U4F.20 (~OE), U4G.20 (~OE)
unnamed: U4D.9 (Zc), U4F.18 (~CS)
unnamed: U4D.12 (Zd), U4G.18 (~CS)
unnamed: U4J.19 (~CE), U6H_.8
unnamed: U6&7D.3 (P0), U6F.11 (D0)
unnamed: U6&7D.4 (P1), U6F.12 (D1)
unnamed: U6&7D.5 (P2), U6F.13 (D2)
unnamed: U6&7D.6 (P3), U6F.15 (D3)
unnamed: U6&7D.12 (Q3), U6D.2 (Dsr)
unnamed: U6&7D.15 (Q0), U7F.5 (I0b)
unnamed: U6D.3 (P0), U6F.16 (D4)
unnamed: U6D.4 (P1), U6F.17 (D5)
unnamed: U6D.5 (P2), U6F.18 (D6)
unnamed: U6D.6 (P3), U6F.19 (D7)
unnamed: U6D.12 (Q3), U7F.6 (I1b)
unnamed: U6F.20 (~CE), U6F.22 (~OE)
unnamed: U6G.11 (D0), U7D.3 (P0)
unnamed: U6G.12 (D1), U7D.4 (P1)
unnamed: U6G.13 (D2), U7D.5 (P2)
unnamed: U6G.15 (D3), U7D.6 (P3)
unnamed: U6G.16 (D4), U7E.3 (P0)
unnamed: U6G.17 (D5), U7E.4 (P1)
unnamed: U6G.18 (D6), U7E.5 (P2)
unnamed: U6G.19 (D7), U7E.6 (P3)
unnamed: U6H_.11, U6J.19 (~CE)
unnamed: U7D.12 (Q3), U7E.2 (Dsr)
unnamed: U7D.15 (Q0), U7F.2 (I0a)
unnamed: U7E.12 (Q3), U7F.3 (I1a)
PIXEL_CLK: U2D.11 (Cp), U4B_.10, U6&7D.11 (Cp), U6D.11 (Cp), U7D.11 (Cp), U7E.11 (Cp)
SH_REG_DIR: U3D_.2, U7F.1 (S)
VCC: U4D.3 (I1a), U4H.1 (~Mr), U6&7D.1 (~CL), U6D.1 (~CL), U6F.28 (VCC), U6G.27 (~PGM), U7D.1 (~CL), U7E.1 (~CL)
VPIX0: U6F.10 (A0), U6G.10 (A0)
VPIX1: U6F.9 (A1), U6G.9 (A1)
VPIX2: U6F.8 (A2), U6G.8 (A2)
VPIX3: U3G.10 (I1c)
VPIX4: U3G.13 (I1d)
VPIX5: U3F.3 (I1a)
VPIX6: U3F.6 (I1b)
VPIX7: U3F.10 (I1c)
Z80M_A0: U3H.2 (I0a)
Z80M_A1: U3H.5 (I0b)
Z80M_A2: U3H.11 (I0c)
Z80M_A3: U3H.14 (I0d)
Z80M_A4: U3G.2 (I0a)
Z80M_A5: U3G.5 (I0b)
Z80M_A6: U3G.11 (I0c)
Z80M_A7: U3G.14 (I0d)
Z80M_A8: U3F.2 (I0a)
Z80M_A9: U3F.5 (I0b)
Z80M_A10: U3F.11 (I0c)
Z80M_D0: U4J.5 (A3), U6J.5 (A3)
Z80M_D1: U4J.2 (A0), U6J.2 (A0)
Z80M_D2: U4J.3 (A1), U6J.3 (A1)
Z80M_D3: U4J.9 (A7), U6J.9 (A7)
Z80M_D4: U4J.8 (A6), U6J.8 (A6)
Z80M_D5: U4J.7 (A5), U6J.7 (A5)
Z80M_D6: U4J.6 (A4), U6J.6 (A4)
Z80M_D7: U4J.4 (A2), U6J.4 (A2)
~ATRRAM: U4D.14 (I0d), U6H_.9
~CHARAM: U4D.11 (I0c), U6H_.13
~Z80M_MAIN_RD: U4D.5 (I0b), U4J.1 (A->B), U6J.1 (A->B)
~Z80M_MAIN_WR: U4D.2 (I0a)

Notes on the sheet:
CHARAM
ATRRAM
