MiSTer-devel/Arcade-SlapFight_MiSTer/docs/KiCAD/SlapFight/pixels.kicad_sch

## KiCad design docs/KiCAD/SlapFight/pixels.kicad_sch (2022-12-26)

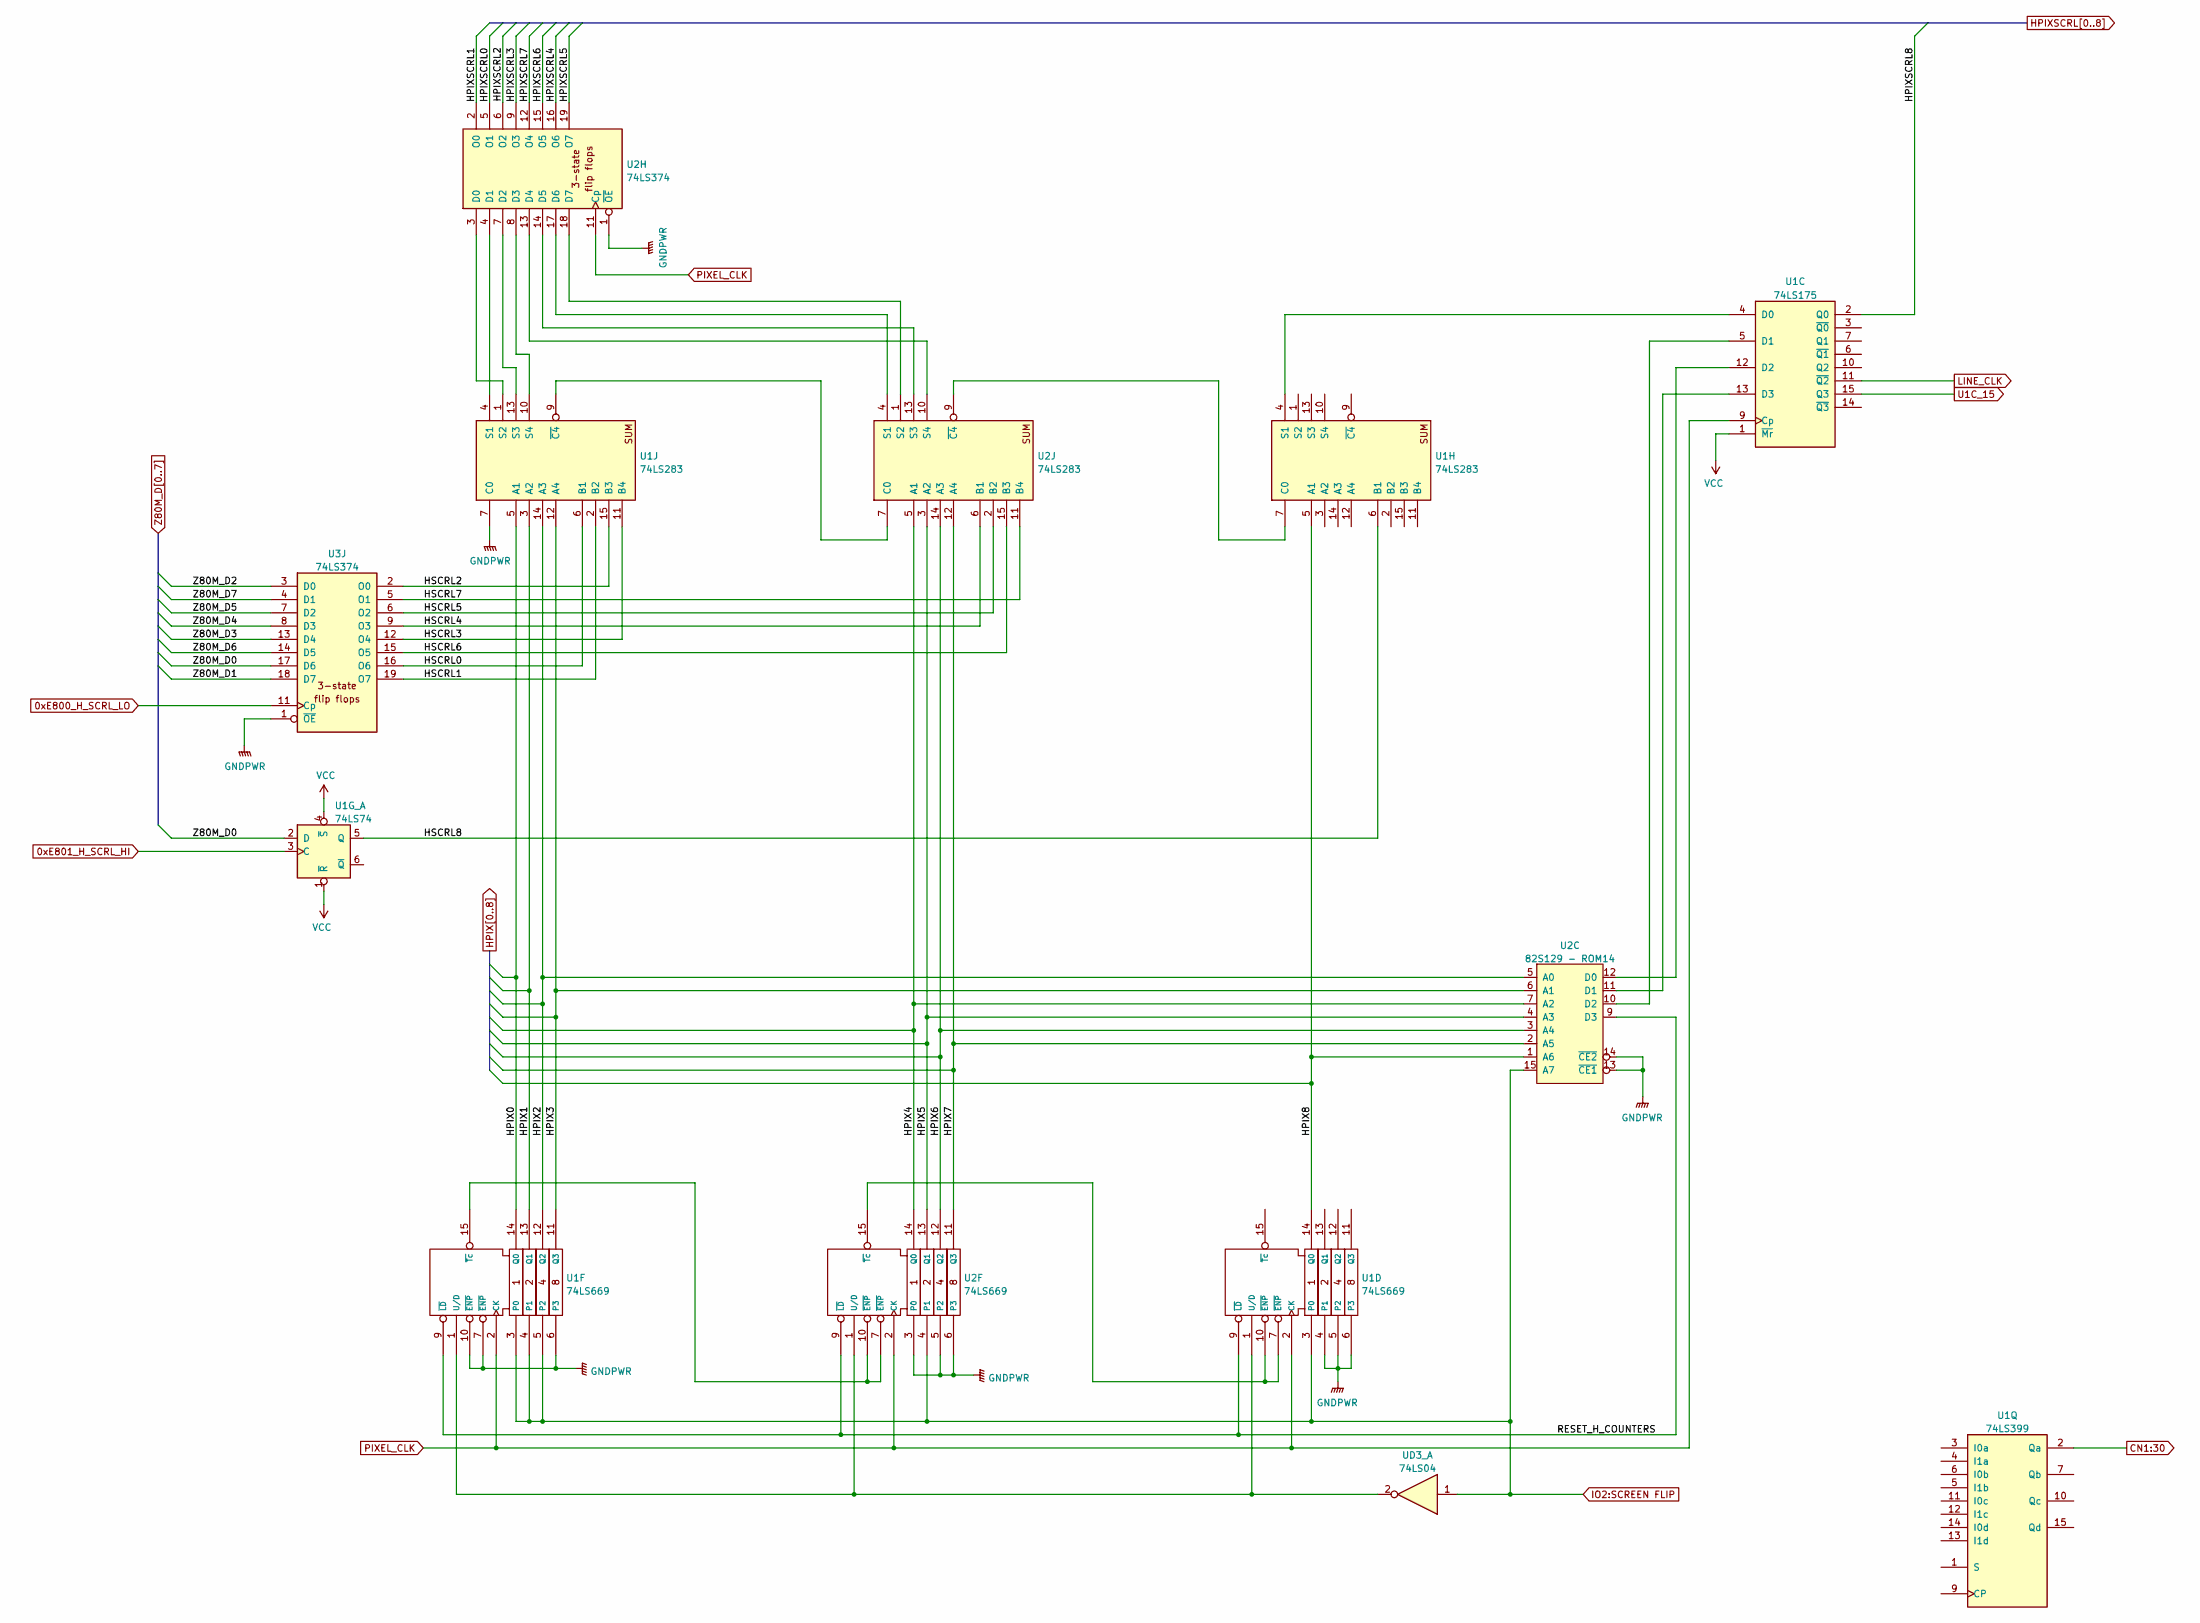
[picture p27: schematic pixels.kicad_sch]

Parts:
U1C: 74LS175
U1D, U1F, U2F: 74LS669
U1G_: 74LS74
U1H, U1J, U2J: 74LS283
U1Q: 74LS399
U2C: 82S129 - ROM14
U2H, U3J: 74LS374
UD3_: 74LS04

Connections:
0xE800_H_SCRL_LO: U3J.11 (Cp)
0xE801_H_SCRL_HI: U1G_.3 (C)
CN1:30: U1Q.2 (Qa)
GNDPWR: U1D.4 (P1), U1D.5 (P2), U1D.6 (P3), U1F.6 (P3), U1F.7 (~ENP), U1F.10 (~ENP), U2F.3 (P0), U2F.5 (P2), U2F.6 (P3), U3J.1 (~OE)
HPIX0: U1F.14 (Q0), U1J.5 (A1)
HPIX1: U1F.13 (Q1), U1J.3 (A2)
HPIX2: U1F.12 (Q2), U1J.14 (A3), U2C.5 (A0)
HPIX3: U1F.11 (Q3), U1J.12 (A4), U2C.6 (A1)
HPIX4: U2C.7 (A2), U2F.14 (Q0), U2J.5 (A1)
HPIX5: U2C.4 (A3), U2F.13 (Q1), U2J.3 (A2)
HPIX6: U2C.3 (A4), U2F.12 (Q2), U2J.14 (A3)
HPIX7: U2C.2 (A5), U2F.11 (Q3), U2J.12 (A4)
HPIX8: U1D.14 (Q0), U1H.5 (A1), U2C.1 (A6)
HPIXSCRL0: U2H.5 (O1)
HPIXSCRL1: U2H.2 (O0)
HPIXSCRL2: U2H.6 (O2)
HPIXSCRL3: U2H.9 (O3)
HPIXSCRL4: U2H.16 (O6)
HPIXSCRL5: U2H.19 (O7)
HPIXSCRL6: U2H.15 (O5)
HPIXSCRL7: U2H.12 (O4)
HPIXSCRL8: U1C.2 (Q0)
HSCRL0: U1J.6 (B1), U3J.16 (O6)
HSCRL1: U1J.2 (B2), U3J.19 (O7)
HSCRL2: U1J.15 (B3), U3J.2 (O0)
HSCRL3: U1J.11 (B4), U3J.12 (O4)
HSCRL4: U2J.6 (B1), U3J.9 (O3)
HSCRL5: U2J.2 (B2), U3J.6 (O2)
HSCRL6: U2J.15 (B3), U3J.15 (O5)
HSCRL7: U2J.11 (B4), U3J.5 (O1)
HSCRL8: U1G_.5 (Q), U1H.6 (B1)
IO2:SCREEN FLIP: U1D.3 (P0), U1F.3 (P0), U1F.4 (P1), U1F.5 (P2), U2C.15 (A7), U2F.4 (P1), UD3_.1
LINE_CLK: U1C.11 (~Q2)
unnamed: U1C.4 (D0), U1H.4 (S1)
unnamed: U1C.5 (D1), U2C.10 (D2)
unnamed: U1C.12 (D2), U2C.12 (D0)
unnamed: U1C.13 (D3), U2C.11 (D1)
unnamed: U1D.1 (U/D), U1F.1 (U/D), U2F.1 (U/D), UD3_.2
unnamed: U1D.7 (~ENP), U1D.10 (~ENP), U2F.15 (~Tc)
unnamed: U1F.15 (~Tc), U2F.7 (~ENP), U2F.10 (~ENP)
unnamed: U1H.7 (C0), U2J.9 (~C4)
unnamed: U1J.1 (S2), U2H.3 (D0)
unnamed: U1J.4 (S1), U2H.4 (D1)
unnamed: U1J.9 (~C4), U2J.7 (C0)
unnamed: U1J.10 (S4), U2H.8 (D3)
unnamed: U1J.13 (S3), U2H.7 (D2)
unnamed: U2C.13 (~CE1), U2C.14 (~CE2)
unnamed: U2H.13 (D4), U2J.10 (S4)
unnamed: U2H.14 (D5), U2J.13 (S3)
unnamed: U2H.17 (D6), U2J.4 (S1)
unnamed: U2H.18 (D7), U2J.1 (S2)
PIXEL_CLK: U1C.9 (Cp), U1D.2 (CK), U1F.2 (CK), U2F.2 (CK), U2H.11 (Cp)
RESET_H_COUNTERS: U1D.9 (~LD), U1F.9 (~LD), U2C.9 (D3), U2F.9 (~LD)
U1C_15: U1C.15 (Q3)
VCC: U1C.1 (~Mr)
Z80M_D0: U1G_.2 (D), U3J.17 (D6)
Z80M_D1: U3J.18 (D7)
Z80M_D2: U3J.3 (D0)
Z80M_D3: U3J.13 (D4)
Z80M_D4: U3J.8 (D3)
Z80M_D5: U3J.7 (D2)
Z80M_D6: U3J.14 (D5)
Z80M_D7: U3J.4 (D1)
