MiSTer-devel/Arcade-SlapFight_MiSTer/docs/KiCAD/SlapFight/spLinebuff.kicad_sch

## KiCad design docs/KiCAD/SlapFight/spLinebuff.kicad_sch (2022-12-26)

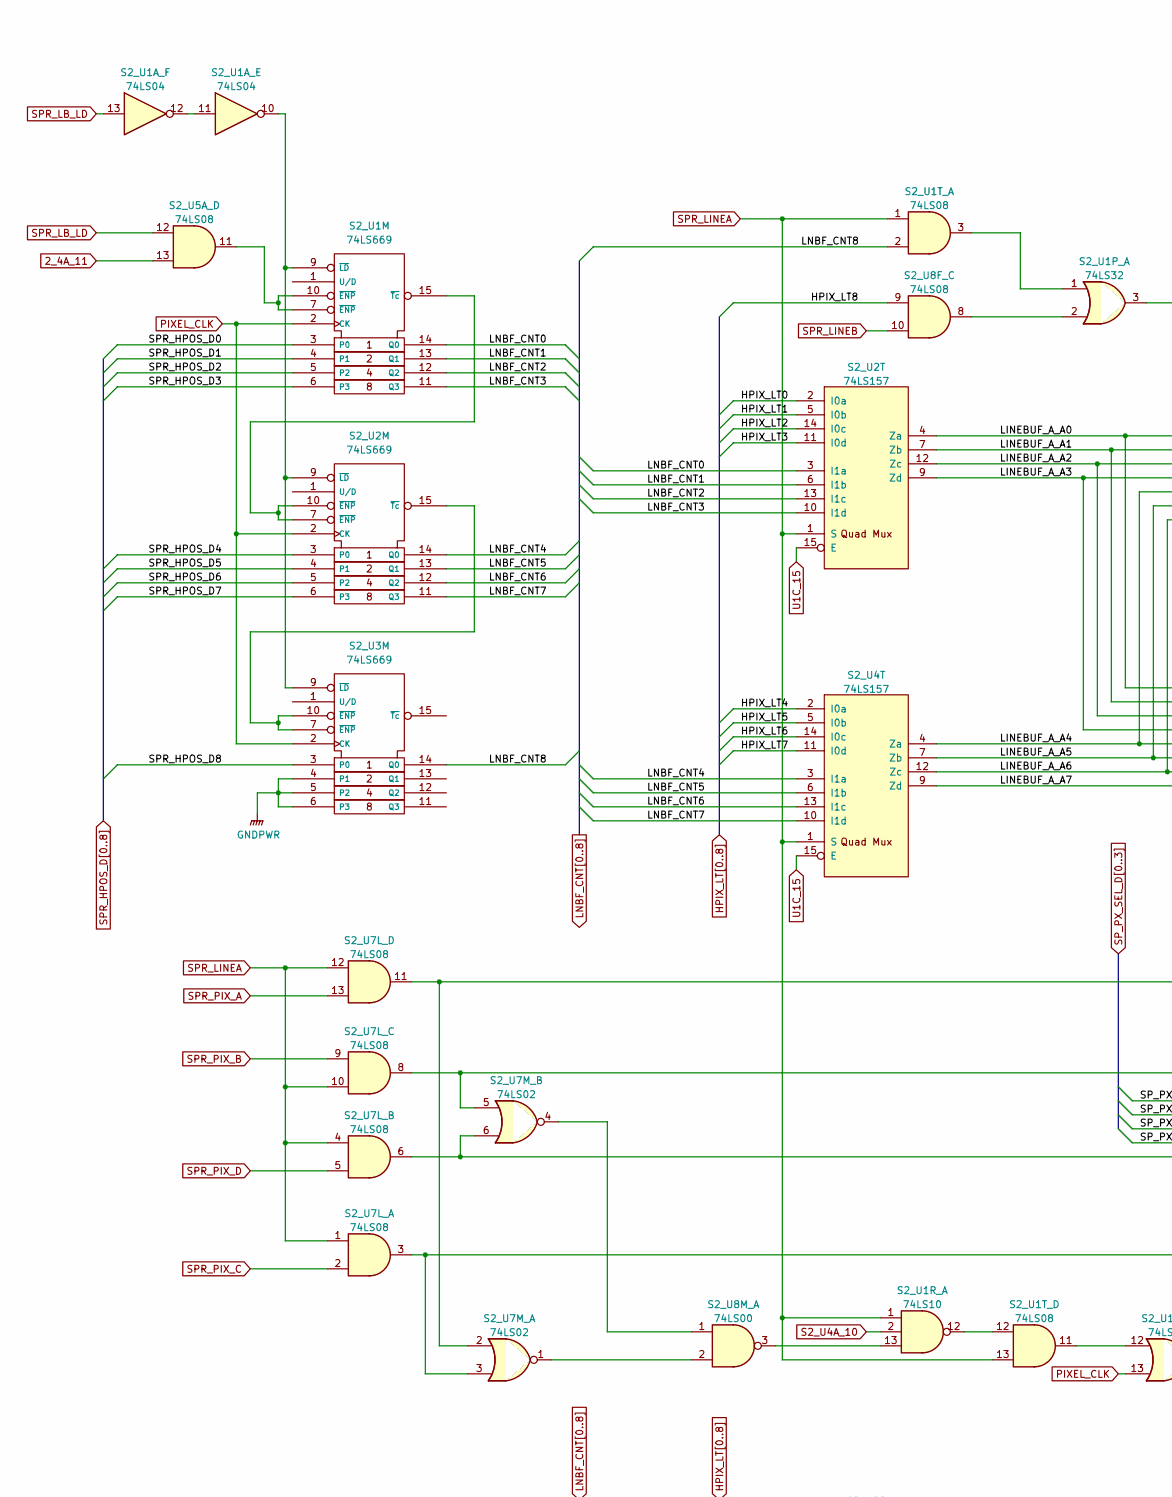
[picture p28: schematic spLinebuff.kicad_sch, part in row 1, column 1]

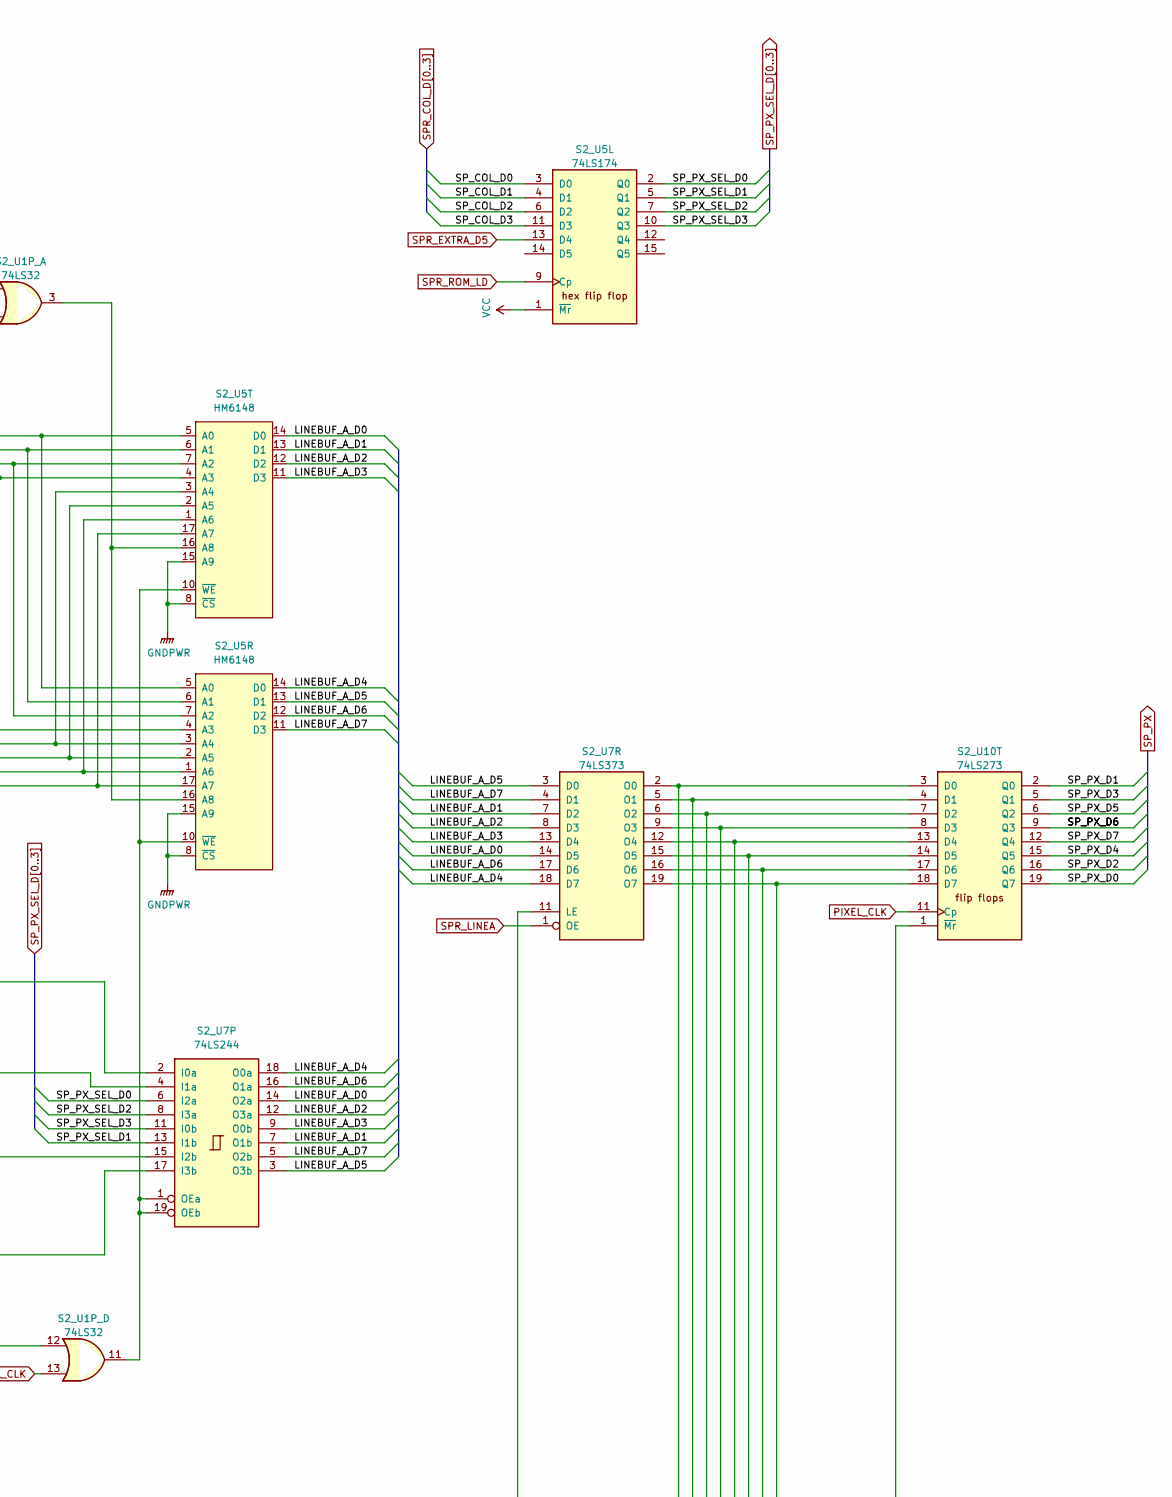
[picture p29: schematic spLinebuff.kicad_sch, part in row 1, column 2]

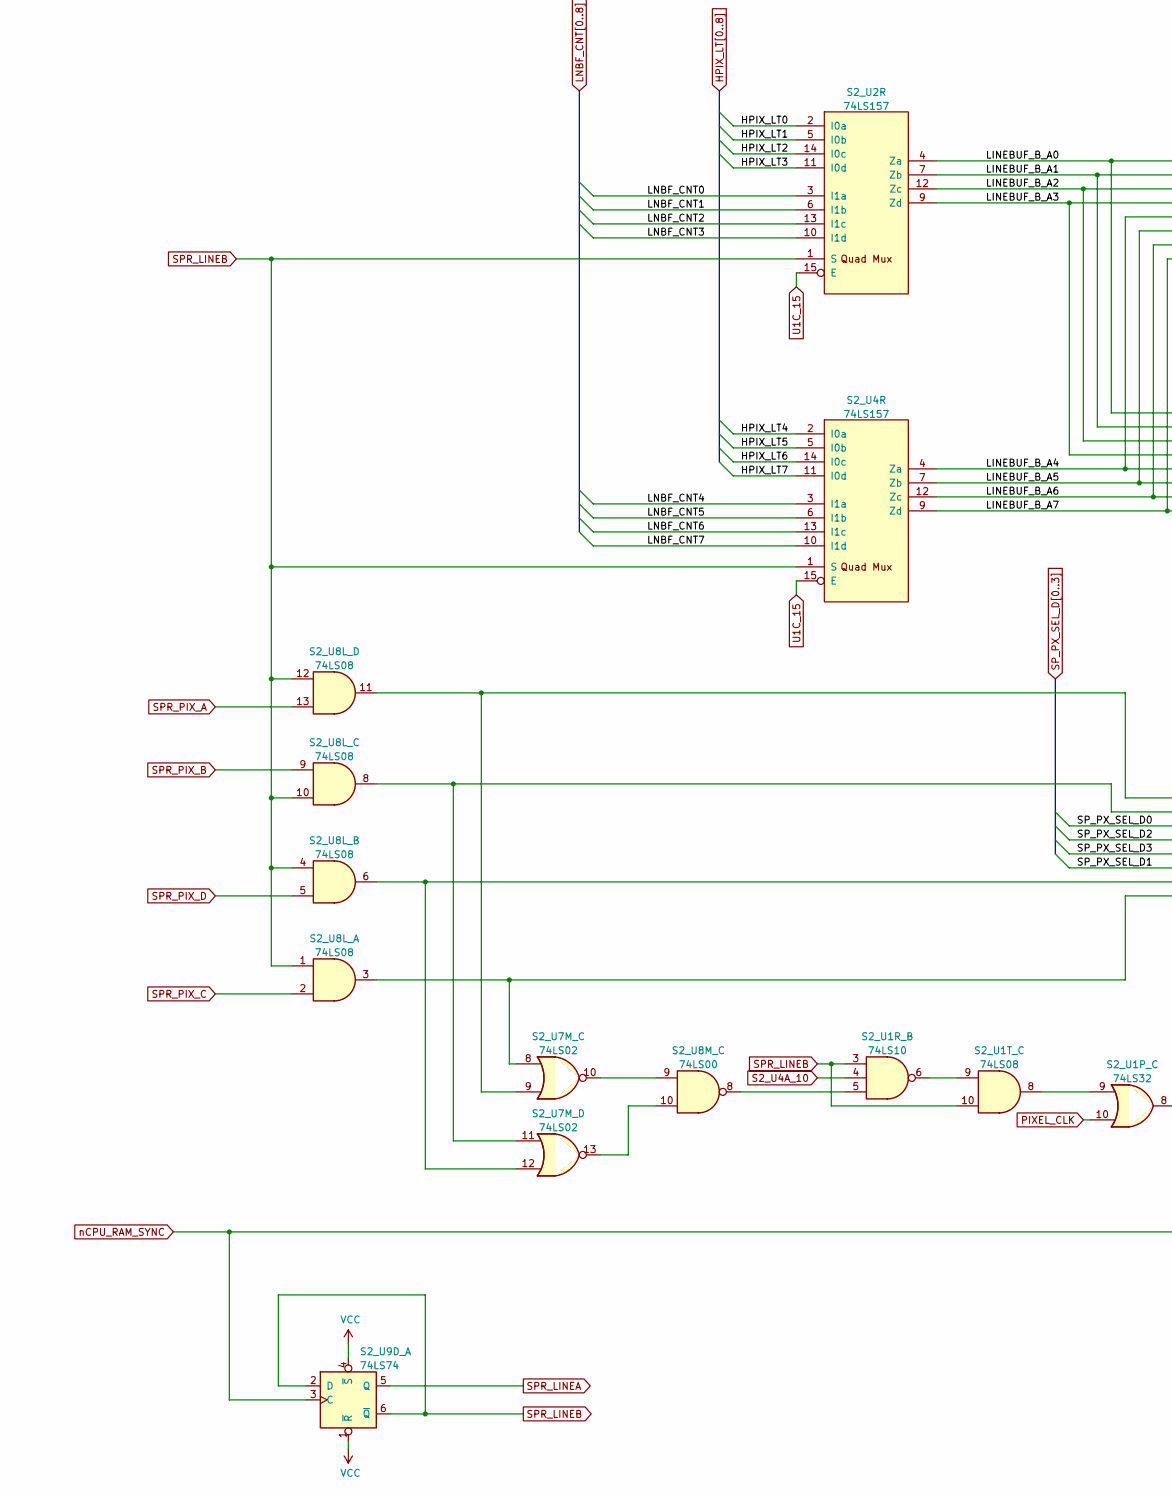
[picture p30: schematic spLinebuff.kicad_sch, part in row 2, column 1]

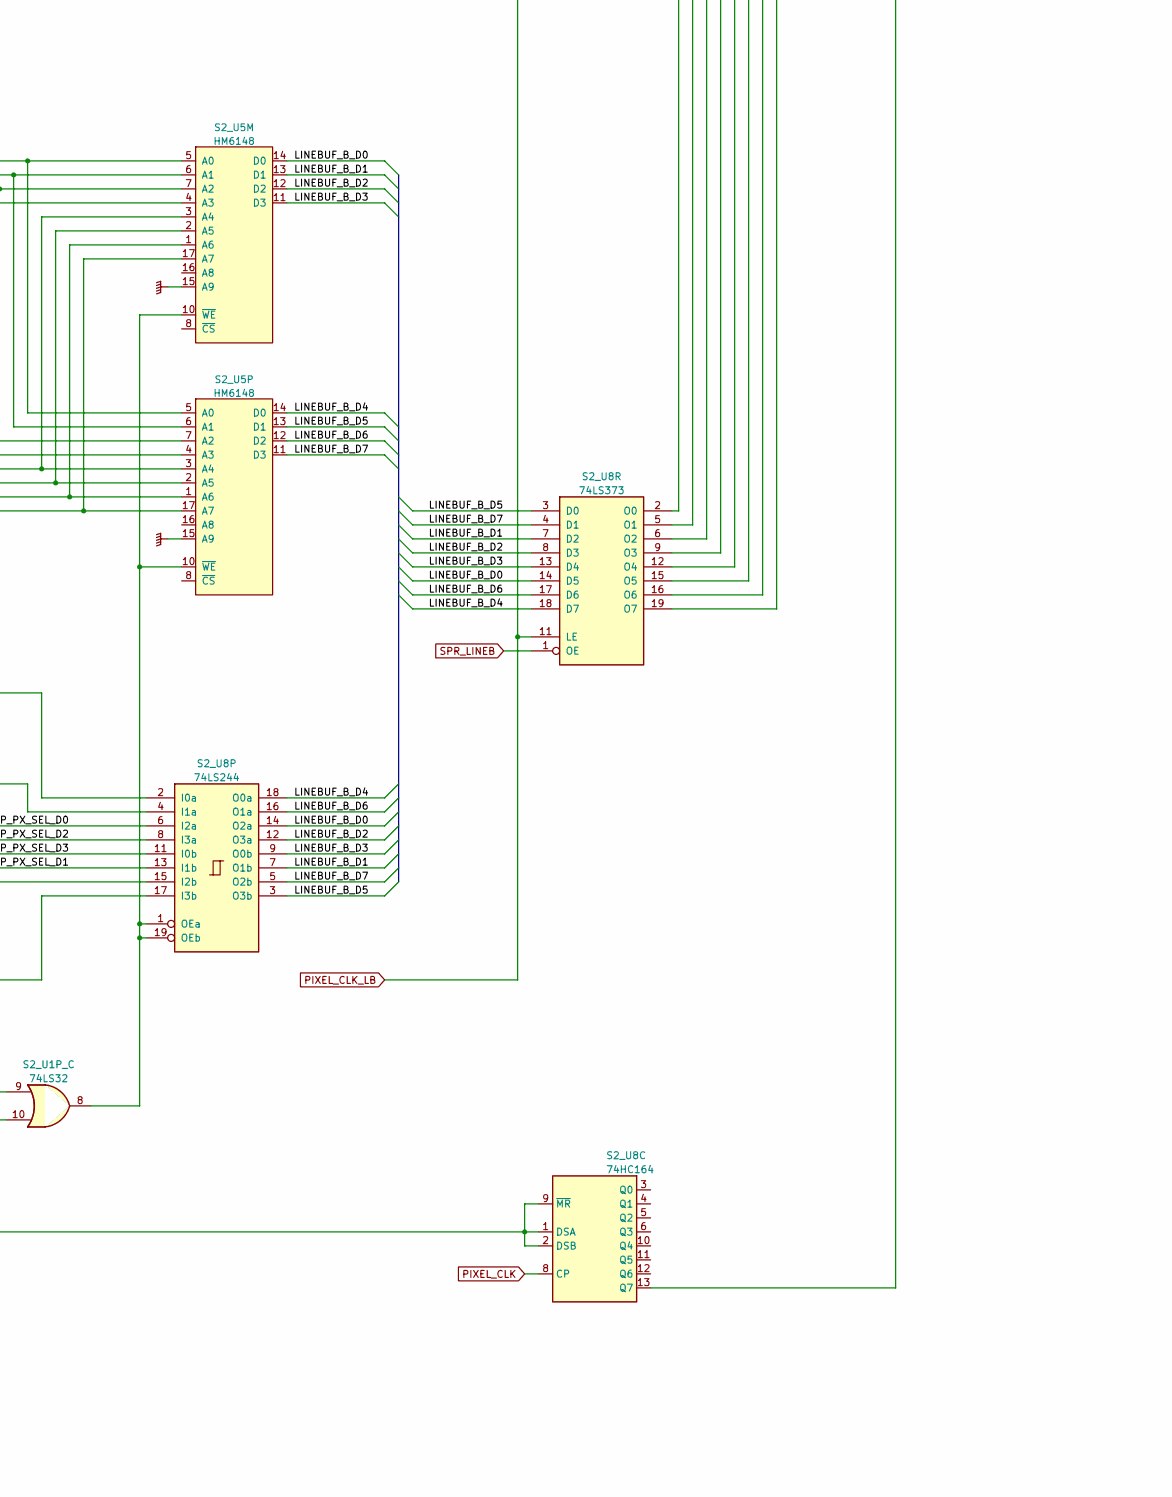
[picture p31: schematic spLinebuff.kicad_sch, part in row 2, column 2]

Parts:
S2_U1A_: 74LS04
S2_U1M, S2_U2M, S2_U3M: 74LS669
S2_U1P_: 74LS32
S2_U1R_: 74LS10
S2_U1T_, S2_U5A_, S2_U7L_, S2_U8F_, S2_U8L_: 74LS08
S2_U2R, S2_U2T, S2_U4R, S2_U4T: 74LS157
S2_U5L: 74LS174
S2_U5M, S2_U5P, S2_U5R, S2_U5T: HM6148
S2_U7M_: 74LS02
S2_U7P, S2_U8P: 74LS244
S2_U7R, S2_U8R: 74LS373
S2_U8C: 74HC164
S2_U8M_: 74LS00
S2_U9D_: 74LS74
S2_U10T: 74LS273

Connections:
2_4A_11: S2_U5A_.13
HPIX_LT0: S2_U2R.2 (I0a), S2_U2T.2 (I0a)
HPIX_LT1: S2_U2R.5 (I0b), S2_U2T.5 (I0b)
HPIX_LT2: S2_U2R.14 (I0c), S2_U2T.14 (I0c)
HPIX_LT3: S2_U2R.11 (I0d), S2_U2T.11 (I0d)
HPIX_LT4: S2_U4R.2 (I0a), S2_U4T.2 (I0a)
HPIX_LT5: S2_U4R.5 (I0b), S2_U4T.5 (I0b)
HPIX_LT6: S2_U4R.14 (I0c), S2_U4T.14 (I0c)
HPIX_LT7: S2_U4R.11 (I0d), S2_U4T.11 (I0d)
HPIX_LT8: S2_U8F_.9
LINEBUF_A_A0: S2_U2T.4 (Za), S2_U5R.5 (A0), S2_U5T.5 (A0)
LINEBUF_A_A1: S2_U2T.7 (Zb), S2_U5R.6 (A1), S2_U5T.6 (A1)
LINEBUF_A_A2: S2_U2T.12 (Zc), S2_U5R.7 (A2), S2_U5T.7 (A2)
LINEBUF_A_A3: S2_U2T.9 (Zd), S2_U5R.4 (A3), S2_U5T.4 (A3)
LINEBUF_A_A4: S2_U4T.4 (Za), S2_U5R.3 (A4), S2_U5T.3 (A4)
LINEBUF_A_A5: S2_U4T.7 (Zb), S2_U5R.2 (A5), S2_U5T.2 (A5)
LINEBUF_A_A6: S2_U4T.12 (Zc), S2_U5R.1 (A6), S2_U5T.1 (A6)
LINEBUF_A_A7: S2_U4T.9 (Zd), S2_U5R.17 (A7), S2_U5T.17 (A7)
LINEBUF_A_D0: S2_U5T.14 (D0), S2_U7P.14 (O2a), S2_U7R.14 (D5)
LINEBUF_A_D1: S2_U5T.13 (D1), S2_U7P.7 (O1b), S2_U7R.7 (D2)
LINEBUF_A_D2: S2_U5T.12 (D2), S2_U7P.12 (O3a), S2_U7R.8 (D3)
LINEBUF_A_D3: S2_U5T.11 (D3), S2_U7P.9 (O0b), S2_U7R.13 (D4)
LINEBUF_A_D4: S2_U5R.14 (D0), S2_U7P.18 (O0a), S2_U7R.18 (D7)
LINEBUF_A_D5: S2_U5R.13 (D1), S2_U7P.3 (O3b), S2_U7R.3 (D0)
LINEBUF_A_D6: S2_U5R.12 (D2), S2_U7P.16 (O1a), S2_U7R.17 (D6)
LINEBUF_A_D7: S2_U5R.11 (D3), S2_U7P.5 (O2b), S2_U7R.4 (D1)
LINEBUF_B_A0: S2_U2R.4 (Za), S2_U5M.5 (A0), S2_U5P.5 (A0)
LINEBUF_B_A1: S2_U2R.7 (Zb), S2_U5M.6 (A1), S2_U5P.6 (A1)
LINEBUF_B_A2: S2_U2R.12 (Zc), S2_U5M.7 (A2), S2_U5P.7 (A2)
LINEBUF_B_A3: S2_U2R.9 (Zd), S2_U5M.4 (A3), S2_U5P.4 (A3)
LINEBUF_B_A4: S2_U4R.4 (Za), S2_U5M.3 (A4), S2_U5P.3 (A4)
LINEBUF_B_A5: S2_U4R.7 (Zb), S2_U5M.2 (A5), S2_U5P.2 (A5)
LINEBUF_B_A6: S2_U4R.12 (Zc), S2_U5M.1 (A6), S2_U5P.1 (A6)
LINEBUF_B_A7: S2_U4R.9 (Zd), S2_U5M.17 (A7), S2_U5P.17 (A7)
LINEBUF_B_D0: S2_U5M.14 (D0), S2_U8P.14 (O2a), S2_U8R.14 (D5)
LINEBUF_B_D1: S2_U5M.13 (D1), S2_U8P.7 (O1b), S2_U8R.7 (D2)
LINEBUF_B_D2: S2_U5M.12 (D2), S2_U8P.12 (O3a), S2_U8R.8 (D3)
LINEBUF_B_D3: S2_U5M.11 (D3), S2_U8P.9 (O0b), S2_U8R.13 (D4)
LINEBUF_B_D4: S2_U5P.14 (D0), S2_U8P.18 (O0a), S2_U8R.18 (D7)
LINEBUF_B_D5: S2_U5P.13 (D1), S2_U8P.3 (O3b), S2_U8R.3 (D0)
LINEBUF_B_D6: S2_U5P.12 (D2), S2_U8P.16 (O1a), S2_U8R.17 (D6)
LINEBUF_B_D7: S2_U5P.11 (D3), S2_U8P.5 (O2b), S2_U8R.4 (D1)
LNBF_CNT0: S2_U1M.14 (Q0), S2_U2R.3 (I1a), S2_U2T.3 (I1a)
LNBF_CNT1: S2_U1M.13 (Q1), S2_U2R.6 (I1b), S2_U2T.6 (I1b)
LNBF_CNT2: S2_U1M.12 (Q2), S2_U2R.13 (I1c), S2_U2T.13 (I1c)
LNBF_CNT3: S2_U1M.11 (Q3), S2_U2R.10 (I1d), S2_U2T.10 (I1d)
LNBF_CNT4: S2_U2M.14 (Q0), S2_U4R.3 (I1a), S2_U4T.3 (I1a)
LNBF_CNT5: S2_U2M.13 (Q1), S2_U4R.6 (I1b), S2_U4T.6 (I1b)
LNBF_CNT6: S2_U2M.12 (Q2), S2_U4R.13 (I1c), S2_U4T.13 (I1c)
LNBF_CNT7: S2_U2M.11 (Q3), S2_U4R.10 (I1d), S2_U4T.10 (I1d)
LNBF_CNT8: S2_U1T_.2, S2_U3M.14 (Q0)
unnamed: S2_U1A_.10, S2_U1M.9 (~LD), S2_U2M.9 (~LD), S2_U3M.9 (~LD)
unnamed: S2_U1A_.11, S2_U1A_.12
unnamed: S2_U1M.7 (~ENP), S2_U1M.10 (~ENP), S2_U5A_.11
unnamed: S2_U1M.15 (~Tc), S2_U2M.7 (~ENP), S2_U2M.10 (~ENP)
unnamed: S2_U1P_.1, S2_U1T_.3
unnamed: S2_U1P_.2, S2_U8F_.8
unnamed: S2_U1P_.3, S2_U5R.16 (A8), S2_U5T.16 (A8)
unnamed: S2_U1P_.8, S2_U5M.10 (~WE), S2_U5P.10 (~WE), S2_U8P.1 (OEa), S2_U8P.19 (OEb)
unnamed: S2_U1P_.9, S2_U1T_.8
unnamed: S2_U1P_.11, S2_U5R.10 (~WE), S2_U5T.10 (~WE), S2_U7P.1 (OEa), S2_U7P.19 (OEb)
unnamed: S2_U1P_.12, S2_U1T_.11
unnamed: S2_U1R_.5, S2_U8M_.8
unnamed: S2_U1R_.6, S2_U1T_.9
unnamed: S2_U1R_.12, S2_U1T_.12
unnamed: S2_U1R_.13, S2_U8M_.3
unnamed: S2_U2M.15 (~Tc), S2_U3M.7 (~ENP), S2_U3M.10 (~ENP)
unnamed: S2_U3M.4 (P1), S2_U3M.5 (P2), S2_U3M.6 (P3)
unnamed: S2_U5R.8 (~CS), S2_U5R.15 (A9)
unnamed: S2_U5T.8 (~CS), S2_U5T.15 (A9)
unnamed: S2_U7L_.3, S2_U7M_.3, S2_U7P.17 (I3b)
unnamed: S2_U7L_.6, S2_U7M_.6, S2_U7P.15 (I2b)
unnamed: S2_U7L_.8, S2_U7M_.5, S2_U7P.4 (I1a)
unnamed: S2_U7L_.11, S2_U7M_.2, S2_U7P.2 (I0a)
unnamed: S2_U7M_.1, S2_U8M_.2
unnamed: S2_U7M_.4, S2_U8M_.1
unnamed: S2_U7M_.8, S2_U8L_.3, S2_U8P.17 (I3b)
unnamed: S2_U7M_.9, S2_U8L_.11, S2_U8P.2 (I0a)
unnamed: S2_U7M_.10, S2_U8M_.9
unnamed: S2_U7M_.11, S2_U8L_.8, S2_U8P.4 (I1a)
unnamed: S2_U7M_.12, S2_U8L_.6, S2_U8P.15 (I2b)
unnamed: S2_U7M_.13, S2_U8M_.10
unnamed: S2_U8C.13 (Q7), S2_U10T.1 (~Mr)
unnamed: S2_U7R.2 (O0), S2_U8R.2 (O0), S2_U10T.3 (D0)
unnamed: S2_U7R.5 (O1), S2_U8R.5 (O1), S2_U10T.4 (D1)
unnamed: S2_U7R.6 (O2), S2_U8R.6 (O2), S2_U10T.7 (D2)
unnamed: S2_U7R.9 (O3), S2_U8R.9 (O3), S2_U10T.8 (D3)
unnamed: S2_U7R.12 (O4), S2_U8R.12 (O4), S2_U10T.13 (D4)
unnamed: S2_U7R.15 (O5), S2_U8R.15 (O5), S2_U10T.14 (D5)
unnamed: S2_U7R.16 (O6), S2_U8R.16 (O6), S2_U10T.17 (D6)
unnamed: S2_U7R.19 (O7), S2_U8R.19 (O7), S2_U10T.18 (D7)
PIXEL_CLK: S2_U1M.2 (CK), S2_U1P_.10, S2_U1P_.13, S2_U2M.2 (CK), S2_U3M.2 (CK), S2_U8C.8 (CP), S2_U10T.11 (Cp)
PIXEL_CLK_LB: S2_U7R.11 (LE), S2_U8R.11 (LE)
S2_U4A_10: S2_U1R_.2, S2_U1R_.4
SPR_EXTRA_D5: S2_U5L.13 (D4)
SPR_HPOS_D0: S2_U1M.3 (P0)
SPR_HPOS_D1: S2_U1M.4 (P1)
SPR_HPOS_D2: S2_U1M.5 (P2)
SPR_HPOS_D3: S2_U1M.6 (P3)
SPR_HPOS_D4: S2_U2M.3 (P0)
SPR_HPOS_D5: S2_U2M.4 (P1)
SPR_HPOS_D6: S2_U2M.5 (P2)
SPR_HPOS_D7: S2_U2M.6 (P3)
SPR_HPOS_D8: S2_U3M.3 (P0)
SPR_LB_LD: S2_U1A_.13, S2_U5A_.12
SPR_LINEA: S2_U1R_.1, S2_U1T_.1, S2_U1T_.13, S2_U2T.1 (S), S2_U4T.1 (S), S2_U7L_.1, S2_U7L_.4, S2_U7L_.10, S2_U7L_.12, S2_U7R.1 (OE), S2_U9D_.5 (Q)
SPR_LINEB: S2_U1R_.3, S2_U1T_.10, S2_U2R.1 (S), S2_U4R.1 (S), S2_U8F_.10, S2_U8L_.1, S2_U8L_.4, S2_U8L_.10, S2_U8L_.12, S2_U8R.1 (OE), S2_U9D_.2 (D), S2_U9D_.6 (~Q)
SPR_PIX_A: S2_U7L_.13, S2_U8L_.13
SPR_PIX_B: S2_U7L_.9, S2_U8L_.9
SPR_PIX_C: S2_U7L_.2, S2_U8L_.2
SPR_PIX_D: S2_U7L_.5, S2_U8L_.5
SPR_ROM_LD: S2_U5L.9 (Cp)
SP_COL_D0: S2_U5L.3 (D0)
SP_COL_D1: S2_U5L.4 (D1)
SP_COL_D2: S2_U5L.6 (D2)
SP_COL_D3: S2_U5L.11 (D3)
SP_PX_D0: S2_U10T.19 (Q7)
SP_PX_D1: S2_U10T.2 (Q0)
SP_PX_D2: S2_U10T.16 (Q6)
SP_PX_D3: S2_U10T.5 (Q1)
SP_PX_D4: S2_U10T.15 (Q5)
SP_PX_D5: S2_U10T.6 (Q2)
SP_PX_D6: S2_U10T.9 (Q3)
SP_PX_D7: S2_U10T.12 (Q4)
SP_PX_SEL_D0: S2_U5L.2 (Q0), S2_U7P.6 (I2a), S2_U8P.6 (I2a)
SP_PX_SEL_D1: S2_U5L.5 (Q1), S2_U7P.13 (I1b), S2_U8P.13 (I1b)
SP_PX_SEL_D2: S2_U5L.7 (Q2), S2_U7P.8 (I3a), S2_U8P.8 (I3a)
SP_PX_SEL_D3: S2_U5L.10 (Q3), S2_U7P.11 (I0b), S2_U8P.11 (I0b)
U1C_15: S2_U2R.15 (E), S2_U2T.15 (E), S2_U4R.15 (E), S2_U4T.15 (E)
nCPU_RAM_SYNC: S2_U8C.1 (DSA), S2_U8C.2 (DSB), S2_U8C.9 (~MR), S2_U9D_.3 (C)
