MiSTer-devel/Arcade-SlapFight_MiSTer/docs/KiCAD/SlapFight/spradd.kicad_sch

## KiCad design docs/KiCAD/SlapFight/spradd.kicad_sch (2022-12-26)

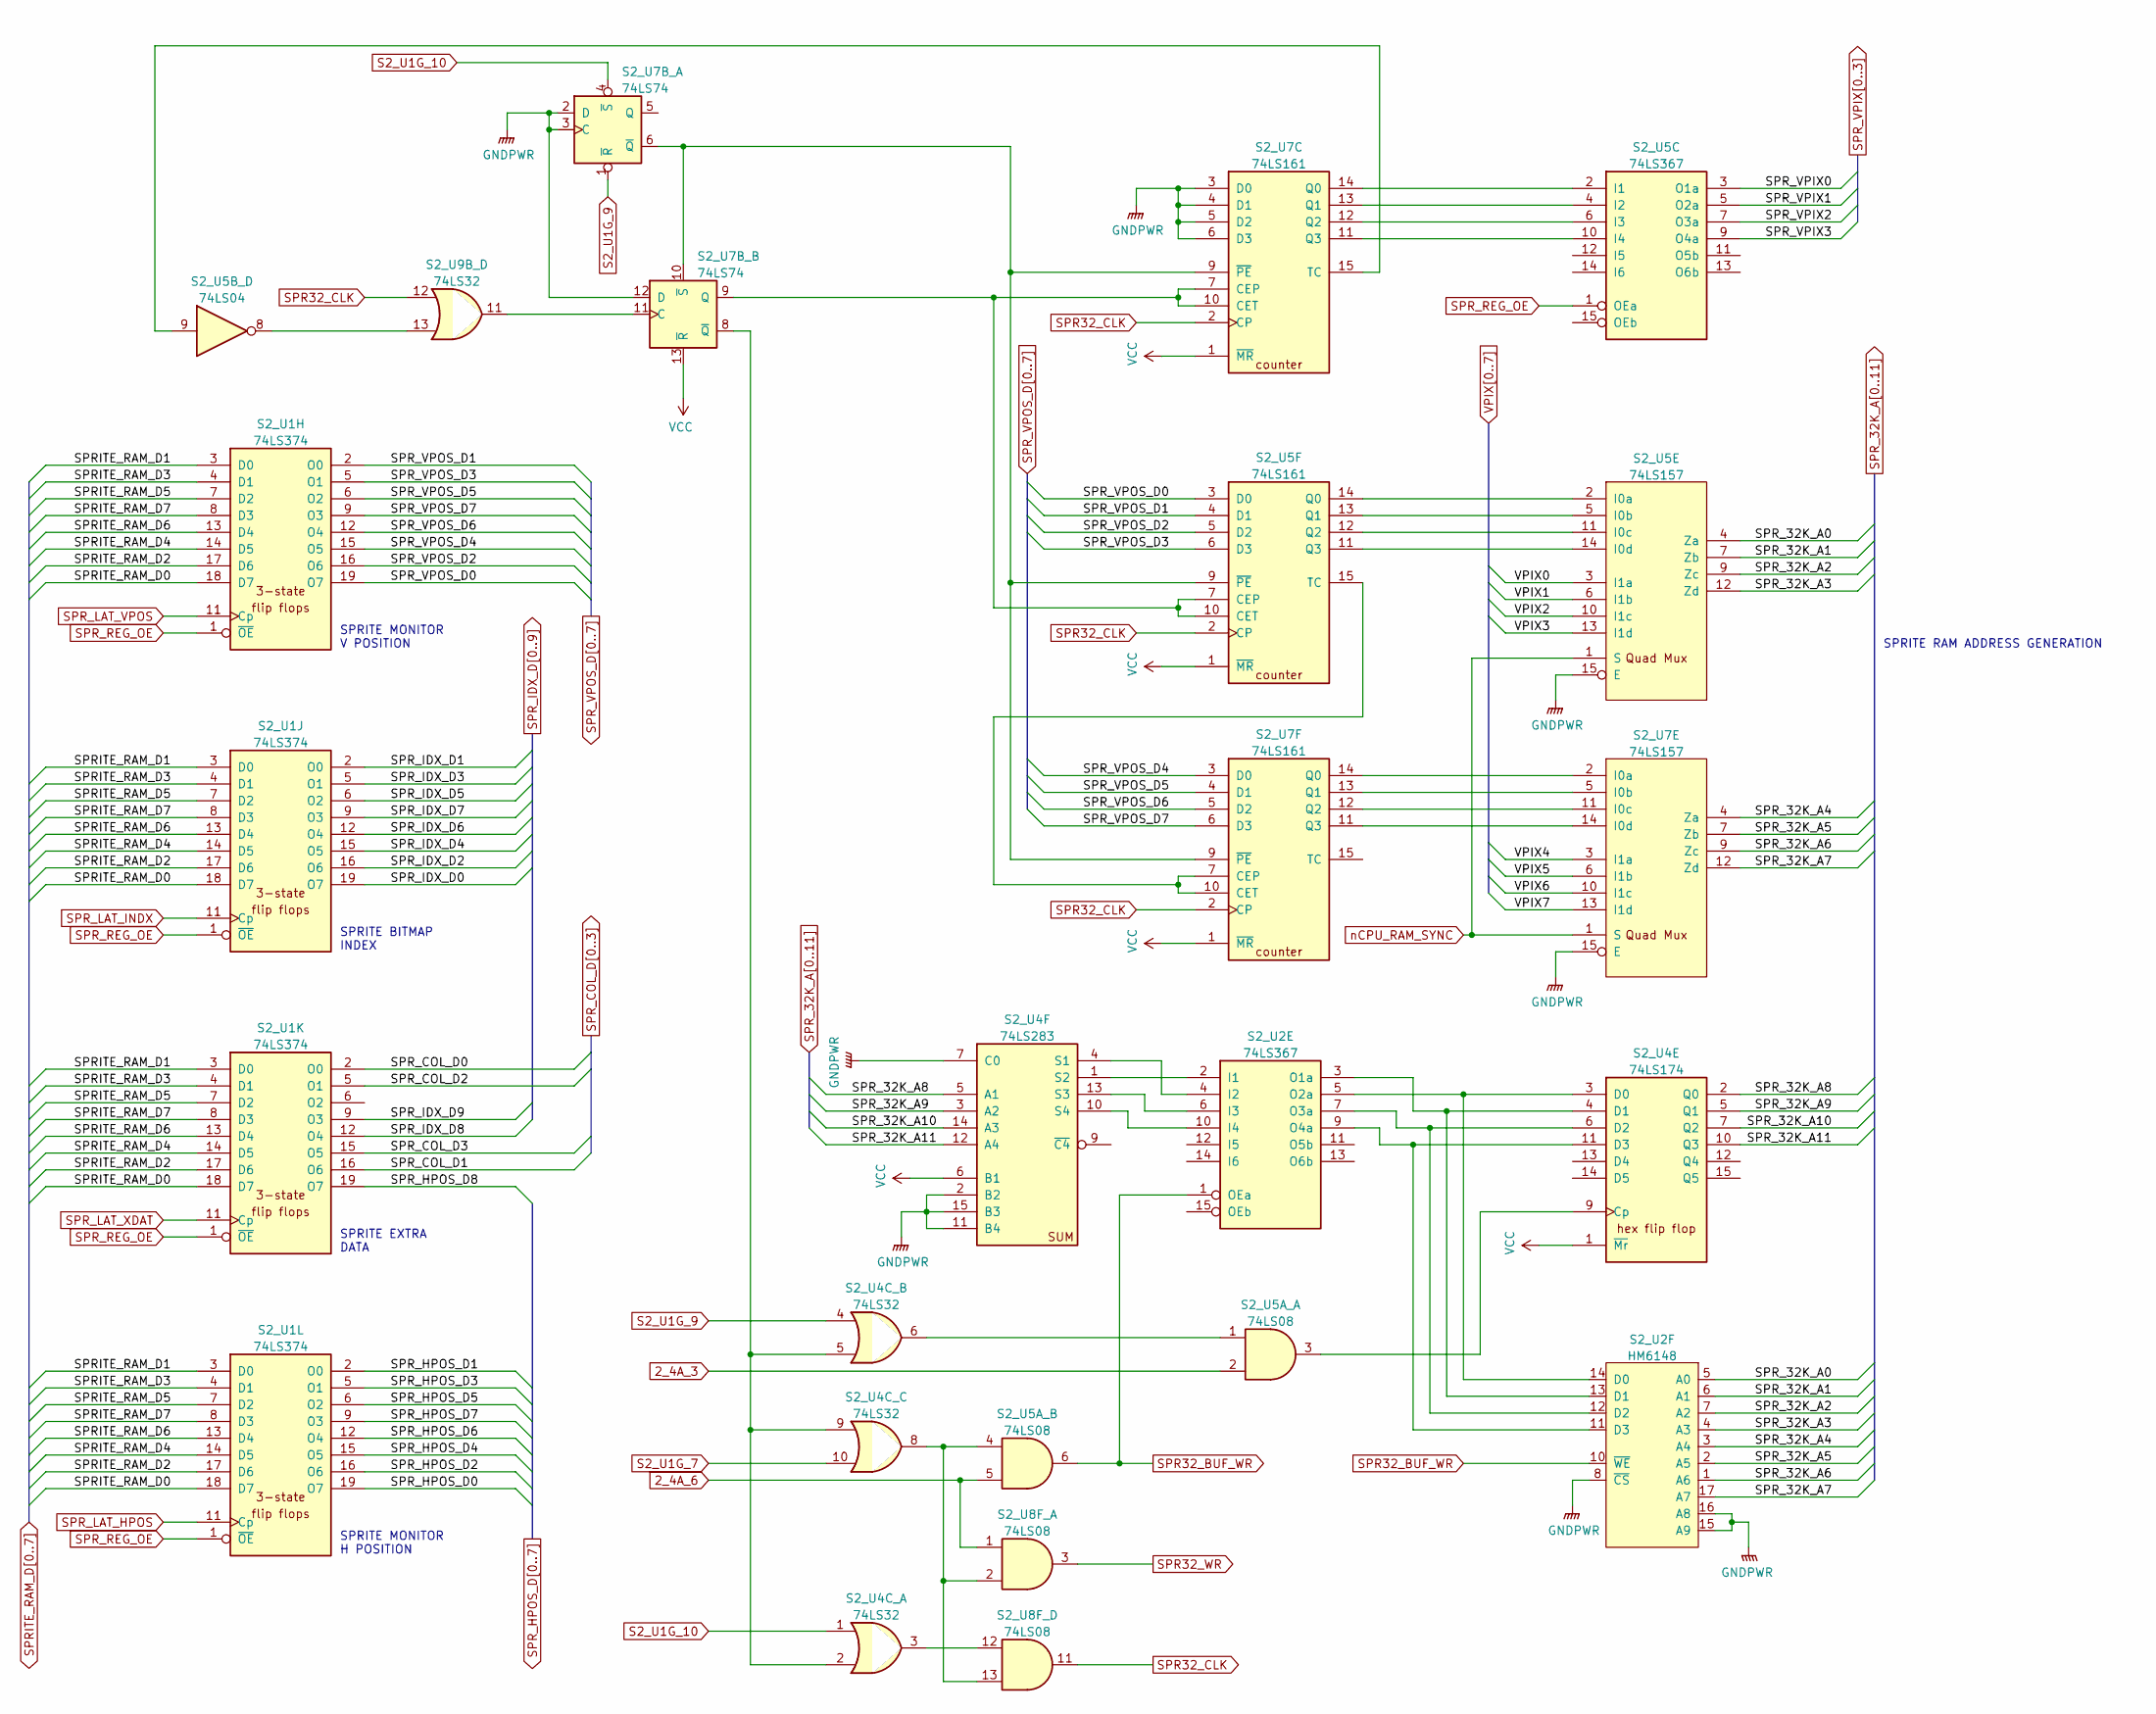
[picture p32: schematic spradd.kicad_sch]

Parts:
S2_U1H, S2_U1J, S2_U1K, S2_U1L: 74LS374
S2_U2E, S2_U5C: 74LS367
S2_U2F: HM6148
S2_U4C_, S2_U9B_: 74LS32
S2_U4E: 74LS174
S2_U4F: 74LS283
S2_U5A_, S2_U8F_: 74LS08
S2_U5B_: 74LS04
S2_U5E, S2_U7E: 74LS157
S2_U5F, S2_U7C, S2_U7F: 74LS161
S2_U7B_: 74LS74

Connections:
2_4A_3: S2_U5A_.2
2_4A_6: S2_U5A_.5, S2_U8F_.1
unnamed: S2_U2E.2 (I1), S2_U4F.1 (S2)
unnamed: S2_U2E.3 (O1a), S2_U2F.13 (D1), S2_U4E.4 (D1)
unnamed: S2_U2E.4 (I2), S2_U4F.4 (S1)
unnamed: S2_U2E.5 (O2a), S2_U2F.14 (D0), S2_U4E.3 (D0)
unnamed: S2_U2E.6 (I3), S2_U4F.13 (S3)
unnamed: S2_U2E.7 (O3a), S2_U2F.12 (D2), S2_U4E.6 (D2)
unnamed: S2_U2E.9 (O4a), S2_U2F.11 (D3), S2_U4E.11 (D3)
unnamed: S2_U2E.10 (I4), S2_U4F.10 (S4)
unnamed: S2_U2F.15 (A9), S2_U2F.16 (A8)
unnamed: S2_U4C_.2, S2_U4C_.5, S2_U4C_.9, S2_U7B_.8 (~Q)
unnamed: S2_U4C_.3, S2_U8F_.12
unnamed: S2_U4C_.6, S2_U5A_.1
unnamed: S2_U4C_.8, S2_U5A_.4, S2_U8F_.2, S2_U8F_.13
unnamed: S2_U4E.9 (Cp), S2_U5A_.3
unnamed: S2_U4F.2 (B2), S2_U4F.11 (B4), S2_U4F.15 (B3)
unnamed: S2_U5B_.8, S2_U9B_.13
unnamed: S2_U5B_.9, S2_U7C.15 (TC)
unnamed: S2_U5C.2 (I1), S2_U7C.14 (Q0)
unnamed: S2_U5C.4 (I2), S2_U7C.13 (Q1)
unnamed: S2_U5C.6 (I3), S2_U7C.12 (Q2)
unnamed: S2_U5C.10 (I4), S2_U7C.11 (Q3)
unnamed: S2_U5E.2 (I0a), S2_U5F.14 (Q0)
unnamed: S2_U5E.5 (I0b), S2_U5F.13 (Q1)
unnamed: S2_U5E.11 (I0c), S2_U5F.12 (Q2)
unnamed: S2_U5E.14 (I0d), S2_U5F.11 (Q3)
unnamed: S2_U5F.9 (~PE), S2_U7B_.6 (~Q), S2_U7B_.10 (~S), S2_U7C.9 (~PE), S2_U7F.9 (~PE)
unnamed: S2_U5F.7 (CEP), S2_U5F.10 (CET), S2_U7B_.9 (Q), S2_U7C.7 (CEP), S2_U7C.10 (CET)
unnamed: S2_U5F.15 (TC), S2_U7F.7 (CEP), S2_U7F.10 (CET)
unnamed: S2_U7B_.11 (C), S2_U9B_.11
unnamed: S2_U7B_.2 (D), S2_U7B_.3 (C), S2_U7B_.12 (D)
unnamed: S2_U7C.3 (D0), S2_U7C.4 (D1), S2_U7C.5 (D2), S2_U7C.6 (D3)
unnamed: S2_U7E.2 (I0a), S2_U7F.14 (Q0)
unnamed: S2_U7E.5 (I0b), S2_U7F.13 (Q1)
unnamed: S2_U7E.11 (I0c), S2_U7F.12 (Q2)
unnamed: S2_U7E.14 (I0d), S2_U7F.11 (Q3)
S2_U1G_7: S2_U4C_.10
S2_U1G_9: S2_U4C_.4, S2_U7B_.1 (~R)
S2_U1G_10: S2_U4C_.1, S2_U7B_.4 (~S)
SPR32_BUF_WR: S2_U2E.1 (OEa), S2_U2F.10 (~WE), S2_U5A_.6
SPR32_CLK: S2_U5F.2 (CP), S2_U7C.2 (CP), S2_U7F.2 (CP), S2_U8F_.11, S2_U9B_.12
SPR32_WR: S2_U8F_.3
SPRITE_RAM_D0: S2_U1H.18 (D7), S2_U1J.18 (D7), S2_U1K.18 (D7), S2_U1L.18 (D7)
SPRITE_RAM_D1: S2_U1H.3 (D0), S2_U1J.3 (D0), S2_U1K.3 (D0), S2_U1L.3 (D0)
SPRITE_RAM_D2: S2_U1H.17 (D6), S2_U1J.17 (D6), S2_U1K.17 (D6), S2_U1L.17 (D6)
SPRITE_RAM_D3: S2_U1H.4 (D1), S2_U1J.4 (D1), S2_U1K.4 (D1), S2_U1L.4 (D1)
SPRITE_RAM_D4: S2_U1H.14 (D5), S2_U1J.14 (D5), S2_U1K.14 (D5), S2_U1L.14 (D5)
SPRITE_RAM_D5: S2_U1H.7 (D2), S2_U1J.7 (D2), S2_U1K.7 (D2), S2_U1L.7 (D2)
SPRITE_RAM_D6: S2_U1H.13 (D4), S2_U1J.13 (D4), S2_U1K.13 (D4), S2_U1L.13 (D4)
SPRITE_RAM_D7: S2_U1H.8 (D3), S2_U1J.8 (D3), S2_U1K.8 (D3), S2_U1L.8 (D3)
SPR_32K_A0: S2_U2F.5 (A0), S2_U5E.4 (Za)
SPR_32K_A1: S2_U2F.6 (A1), S2_U5E.7 (Zb)
SPR_32K_A2: S2_U2F.7 (A2), S2_U5E.9 (Zc)
SPR_32K_A3: S2_U2F.4 (A3), S2_U5E.12 (Zd)
SPR_32K_A4: S2_U2F.3 (A4), S2_U7E.4 (Za)
SPR_32K_A5: S2_U2F.2 (A5), S2_U7E.7 (Zb)
SPR_32K_A6: S2_U2F.1 (A6), S2_U7E.9 (Zc)
SPR_32K_A7: S2_U2F.17 (A7), S2_U7E.12 (Zd)
SPR_32K_A8: S2_U4E.2 (Q0), S2_U4F.5 (A1)
SPR_32K_A9: S2_U4E.5 (Q1), S2_U4F.3 (A2)
SPR_32K_A10: S2_U4E.7 (Q2), S2_U4F.14 (A3)
SPR_32K_A11: S2_U4E.10 (Q3), S2_U4F.12 (A4)
SPR_COL_D0: S2_U1K.2 (O0)
SPR_COL_D1: S2_U1K.16 (O6)
SPR_COL_D2: S2_U1K.5 (O1)
SPR_COL_D3: S2_U1K.15 (O5)
SPR_HPOS_D0: S2_U1L.19 (O7)
SPR_HPOS_D1: S2_U1L.2 (O0)
SPR_HPOS_D2: S2_U1L.16 (O6)
SPR_HPOS_D3: S2_U1L.5 (O1)
SPR_HPOS_D4: S2_U1L.15 (O5)
SPR_HPOS_D5: S2_U1L.6 (O2)
SPR_HPOS_D6: S2_U1L.12 (O4)
SPR_HPOS_D7: S2_U1L.9 (O3)
SPR_HPOS_D8: S2_U1K.19 (O7)
SPR_IDX_D0: S2_U1J.19 (O7)
SPR_IDX_D1: S2_U1J.2 (O0)
SPR_IDX_D2: S2_U1J.16 (O6)
SPR_IDX_D3: S2_U1J.5 (O1)
SPR_IDX_D4: S2_U1J.15 (O5)
SPR_IDX_D5: S2_U1J.6 (O2)
SPR_IDX_D6: S2_U1J.12 (O4)
SPR_IDX_D7: S2_U1J.9 (O3)
SPR_IDX_D8: S2_U1K.12 (O4)
SPR_IDX_D9: S2_U1K.9 (O3)
SPR_LAT_HPOS: S2_U1L.11 (Cp)
SPR_LAT_INDX: S2_U1J.11 (Cp)
SPR_LAT_VPOS: S2_U1H.11 (Cp)
SPR_LAT_XDAT: S2_U1K.11 (Cp)
SPR_REG_OE: S2_U1H.1 (~OE), S2_U1J.1 (~OE), S2_U1K.1 (~OE), S2_U1L.1 (~OE), S2_U5C.1 (OEa)
SPR_VPIX0: S2_U5C.3 (O1a)
SPR_VPIX1: S2_U5C.5 (O2a)
SPR_VPIX2: S2_U5C.7 (O3a)
SPR_VPIX3: S2_U5C.9 (O4a)
SPR_VPOS_D0: S2_U1H.19 (O7), S2_U5F.3 (D0)
SPR_VPOS_D1: S2_U1H.2 (O0), S2_U5F.4 (D1)
SPR_VPOS_D2: S2_U1H.16 (O6), S2_U5F.5 (D2)
SPR_VPOS_D3: S2_U1H.5 (O1), S2_U5F.6 (D3)
SPR_VPOS_D4: S2_U1H.15 (O5), S2_U7F.3 (D0)
SPR_VPOS_D5: S2_U1H.6 (O2), S2_U7F.4 (D1)
SPR_VPOS_D6: S2_U1H.12 (O4), S2_U7F.5 (D2)
SPR_VPOS_D7: S2_U1H.9 (O3), S2_U7F.6 (D3)
VPIX0: S2_U5E.3 (I1a)
VPIX1: S2_U5E.6 (I1b)
VPIX2: S2_U5E.10 (I1c)
VPIX3: S2_U5E.13 (I1d)
VPIX4: S2_U7E.3 (I1a)
VPIX5: S2_U7E.6 (I1b)
VPIX6: S2_U7E.10 (I1c)
VPIX7: S2_U7E.13 (I1d)
nCPU_RAM_SYNC: S2_U5E.1 (S), S2_U7E.1 (S)

Notes on the sheet:
SPRITE BITMAP INDEX
SPRITE MONITOR H POSITION
SPRITE EXTRA DATA
SPRITE MONITOR V POSITION
SPRITE RAM ADDRESS GENERATION
