MiSTer-devel/Arcade-SlapFight_MiSTer/docs/KiCAD/SlapFight/video_out.kicad_sch

## KiCad design docs/KiCAD/SlapFight/video_out.kicad_sch (2022-12-26)

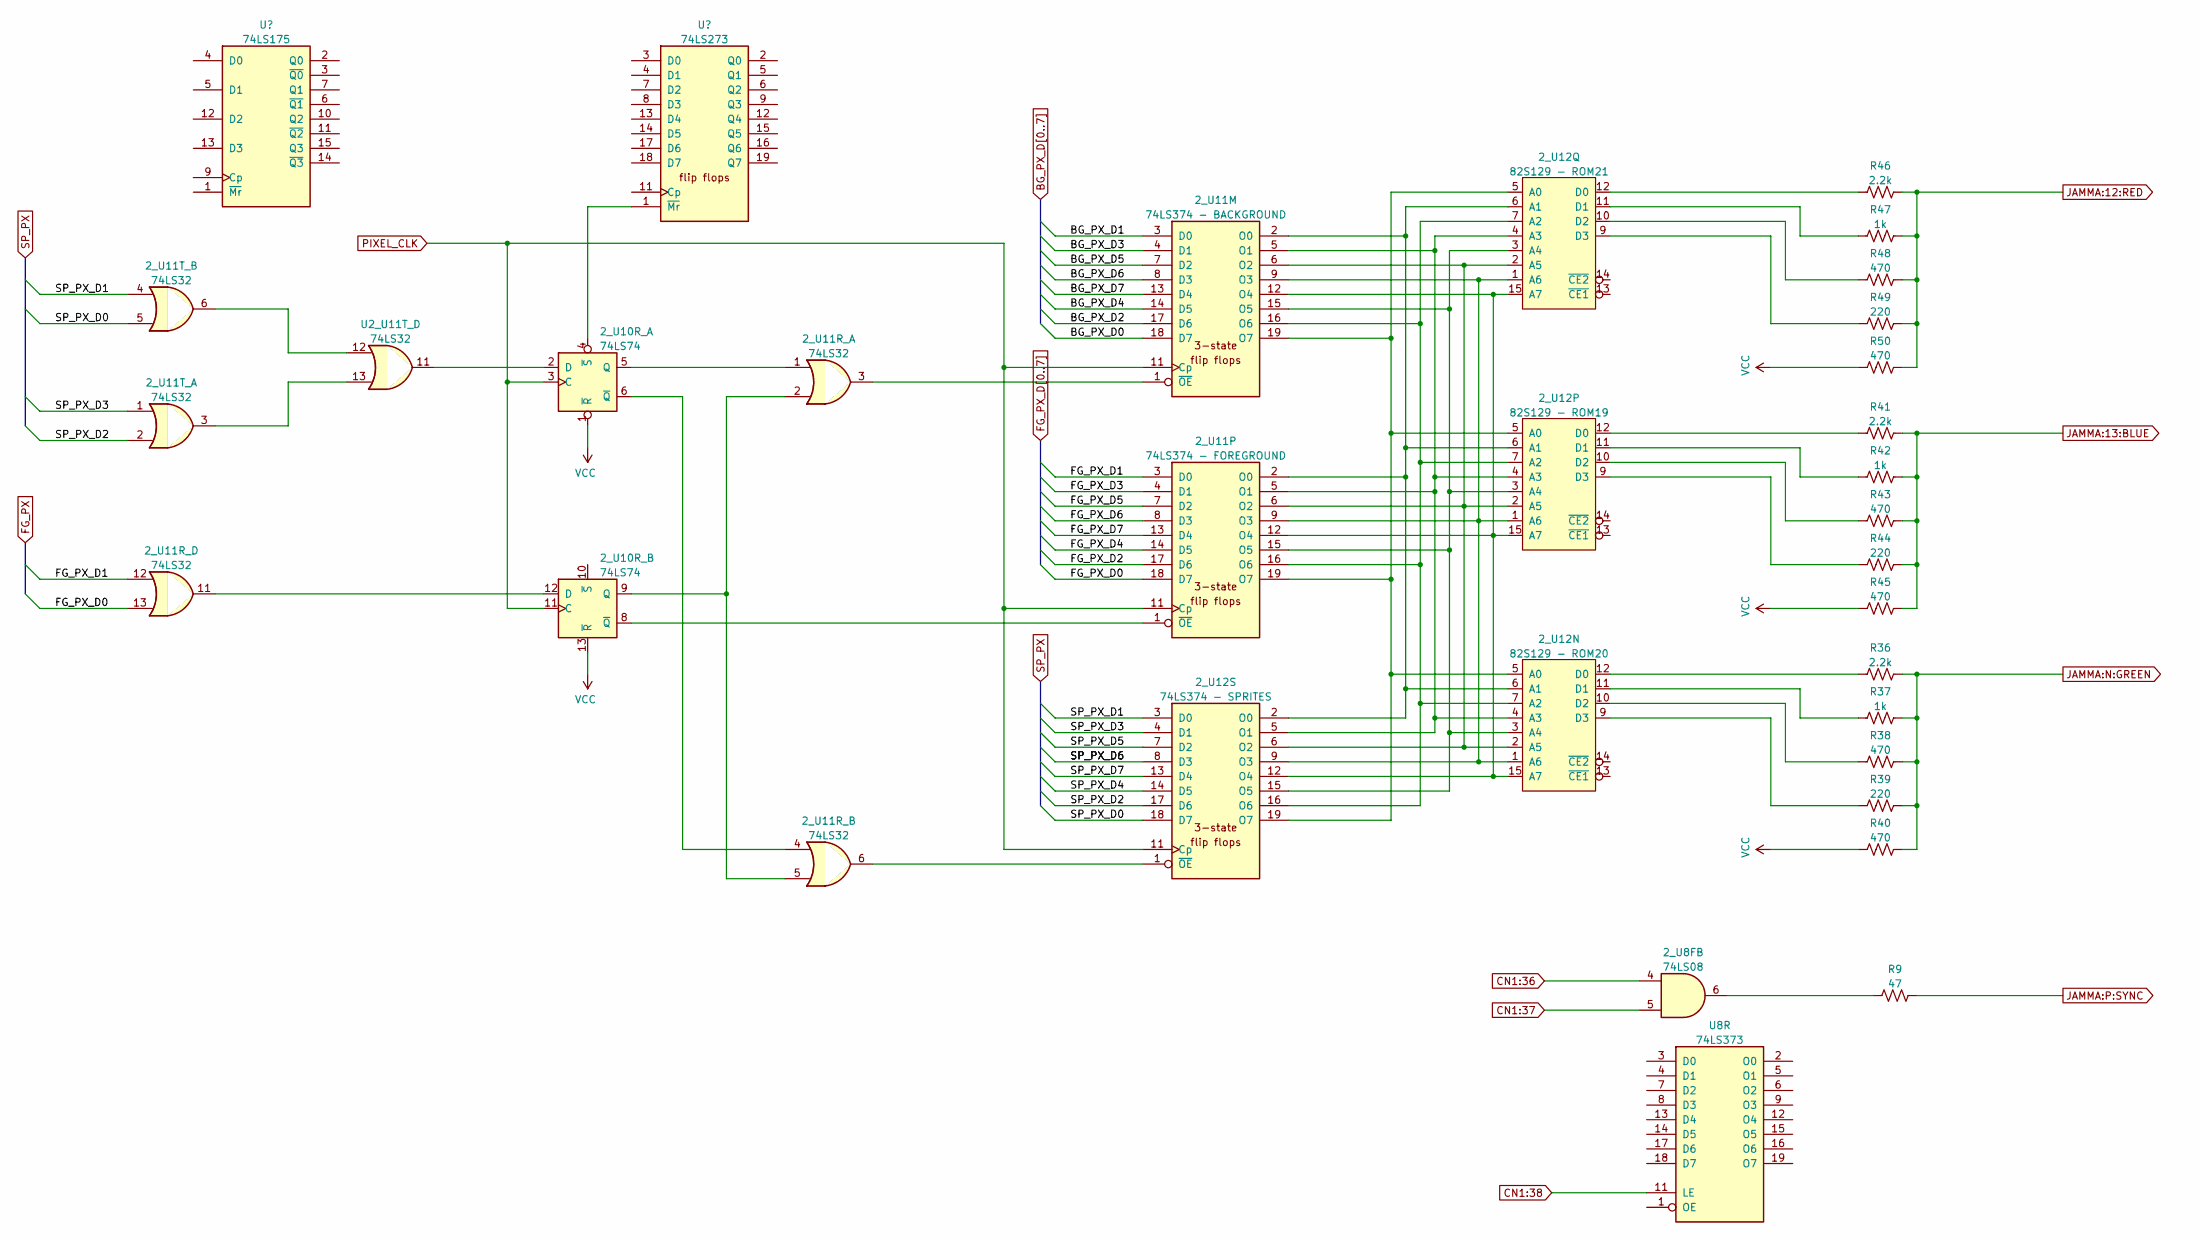
[picture p33: schematic video_out.kicad_sch]

Parts:
2_U8F: 74LS08
2_U10R_: 74LS74
2_U11M: 74LS374 - BACKGROUND
2_U11P: 74LS374 - FOREGROUND
2_U11R_, 2_U11T_: 74LS32
2_U12N: 82S129 - ROM20
2_U12P: 82S129 - ROM19
2_U12Q: 82S129 - ROM21
2_U12S: 74LS374 - SPRITES
R9: 47
R36, R41, R46: 2.2k
R37, R42, R47: 1k
R38, R40, R43, R45, R48, R50: 470
R39, R44, R49: 220
U2_U11T_: 74LS32
U8R: 74LS373

Connections:
BG_PX_D0: 2_U11M.18 (D7)
BG_PX_D1: 2_U11M.3 (D0)
BG_PX_D2: 2_U11M.17 (D6)
BG_PX_D3: 2_U11M.4 (D1)
BG_PX_D4: 2_U11M.14 (D5)
BG_PX_D5: 2_U11M.7 (D2)
BG_PX_D6: 2_U11M.8 (D3)
BG_PX_D7: 2_U11M.13 (D4)
CN1:36: 2_U8F.4
CN1:37: 2_U8F.5
CN1:38: U8R.11 (LE)
FG_PX_D0: 2_U11P.18 (D7), 2_U11R_.13
FG_PX_D1: 2_U11P.3 (D0), 2_U11R_.12
FG_PX_D2: 2_U11P.17 (D6)
FG_PX_D3: 2_U11P.4 (D1)
FG_PX_D4: 2_U11P.14 (D5)
FG_PX_D5: 2_U11P.7 (D2)
FG_PX_D6: 2_U11P.8 (D3)
FG_PX_D7: 2_U11P.13 (D4)
JAMMA:12:RED: R46.2, R47.2, R48.2, R49.2, R50.2
JAMMA:13:BLUE: R41.2, R42.2, R43.2, R44.2, R45.2
JAMMA:N:GREEN: R36.2, R37.2, R38.2, R39.2, R40.2
JAMMA:P:SYNC: R9.2
unnamed: 2_U8F.6, R9.1
unnamed: 2_U10R_.2 (D), U2_U11T_.11
unnamed: 2_U10R_.5 (Q), 2_U11R_.1
unnamed: 2_U10R_.6 (~Q), 2_U11R_.4
unnamed: 2_U10R_.8 (~Q), 2_U11P.1 (~OE)
unnamed: 2_U10R_.9 (Q), 2_U11R_.2, 2_U11R_.5
unnamed: 2_U10R_.12 (D), 2_U11R_.11
unnamed: 2_U11M.1 (~OE), 2_U11R_.3
unnamed: 2_U11M.2 (O0), 2_U11P.2 (O0), 2_U12N.6 (A1), 2_U12P.6 (A1), 2_U12Q.6 (A1), 2_U12S.2 (O0)
unnamed: 2_U11M.5 (O1), 2_U11P.5 (O1), 2_U12N.4 (A3), 2_U12P.4 (A3), 2_U12Q.4 (A3), 2_U12S.5 (O1)
unnamed: 2_U11M.6 (O2), 2_U11P.6 (O2), 2_U12N.2 (A5), 2_U12P.2 (A5), 2_U12Q.2 (A5), 2_U12S.6 (O2)
unnamed: 2_U11M.9 (O3), 2_U11P.9 (O3), 2_U12N.1 (A6), 2_U12P.1 (A6), 2_U12Q.1 (A6), 2_U12S.9 (O3)
unnamed: 2_U11M.12 (O4), 2_U11P.12 (O4), 2_U12N.15 (A7), 2_U12P.15 (A7), 2_U12Q.15 (A7), 2_U12S.12 (O4)
unnamed: 2_U11M.15 (O5), 2_U11P.15 (O5), 2_U12N.3 (A4), 2_U12P.3 (A4), 2_U12Q.3 (A4), 2_U12S.15 (O5)
unnamed: 2_U11M.16 (O6), 2_U11P.16 (O6), 2_U12N.7 (A2), 2_U12P.7 (A2), 2_U12Q.7 (A2), 2_U12S.16 (O6)
unnamed: 2_U11M.19 (O7), 2_U11P.19 (O7), 2_U12N.5 (A0), 2_U12P.5 (A0), 2_U12Q.5 (A0), 2_U12S.19 (O7)
unnamed: 2_U11R_.6, 2_U12S.1 (~OE)
unnamed: 2_U11T_.3, U2_U11T_.13
unnamed: 2_U11T_.6, U2_U11T_.12
unnamed: 2_U12N.9 (D3), R39.1
unnamed: 2_U12N.10 (D2), R38.1
unnamed: 2_U12N.11 (D1), R37.1
unnamed: 2_U12N.12 (D0), R36.1
unnamed: 2_U12P.9 (D3), R44.1
unnamed: 2_U12P.10 (D2), R43.1
unnamed: 2_U12P.11 (D1), R42.1
unnamed: 2_U12P.12 (D0), R41.1
unnamed: 2_U12Q.9 (D3), R49.1
unnamed: 2_U12Q.10 (D2), R48.1
unnamed: 2_U12Q.11 (D1), R47.1
unnamed: 2_U12Q.12 (D0), R46.1
PIXEL_CLK: 2_U10R_.3 (C), 2_U10R_.11 (C), 2_U11M.11 (Cp), 2_U11P.11 (Cp), 2_U12S.11 (Cp)
SP_PX_D0: 2_U11T_.5, 2_U12S.18 (D7)
SP_PX_D1: 2_U11T_.4, 2_U12S.3 (D0)
SP_PX_D2: 2_U11T_.2, 2_U12S.17 (D6)
SP_PX_D3: 2_U11T_.1, 2_U12S.4 (D1)
SP_PX_D4: 2_U12S.14 (D5)
SP_PX_D5: 2_U12S.7 (D2)
SP_PX_D6: 2_U12S.8 (D3)
SP_PX_D7: 2_U12S.13 (D4)
VCC: 2_U10R_.1 (~R), 2_U10R_.13 (~R), R40.1, R45.1, R50.1
