MiSTer-devel/Arcade-SlapFight_MiSTer/docs/KiCAD/SlapFight/vpixels.kicad_sch

## KiCad design docs/KiCAD/SlapFight/vpixels.kicad_sch (2022-12-26)

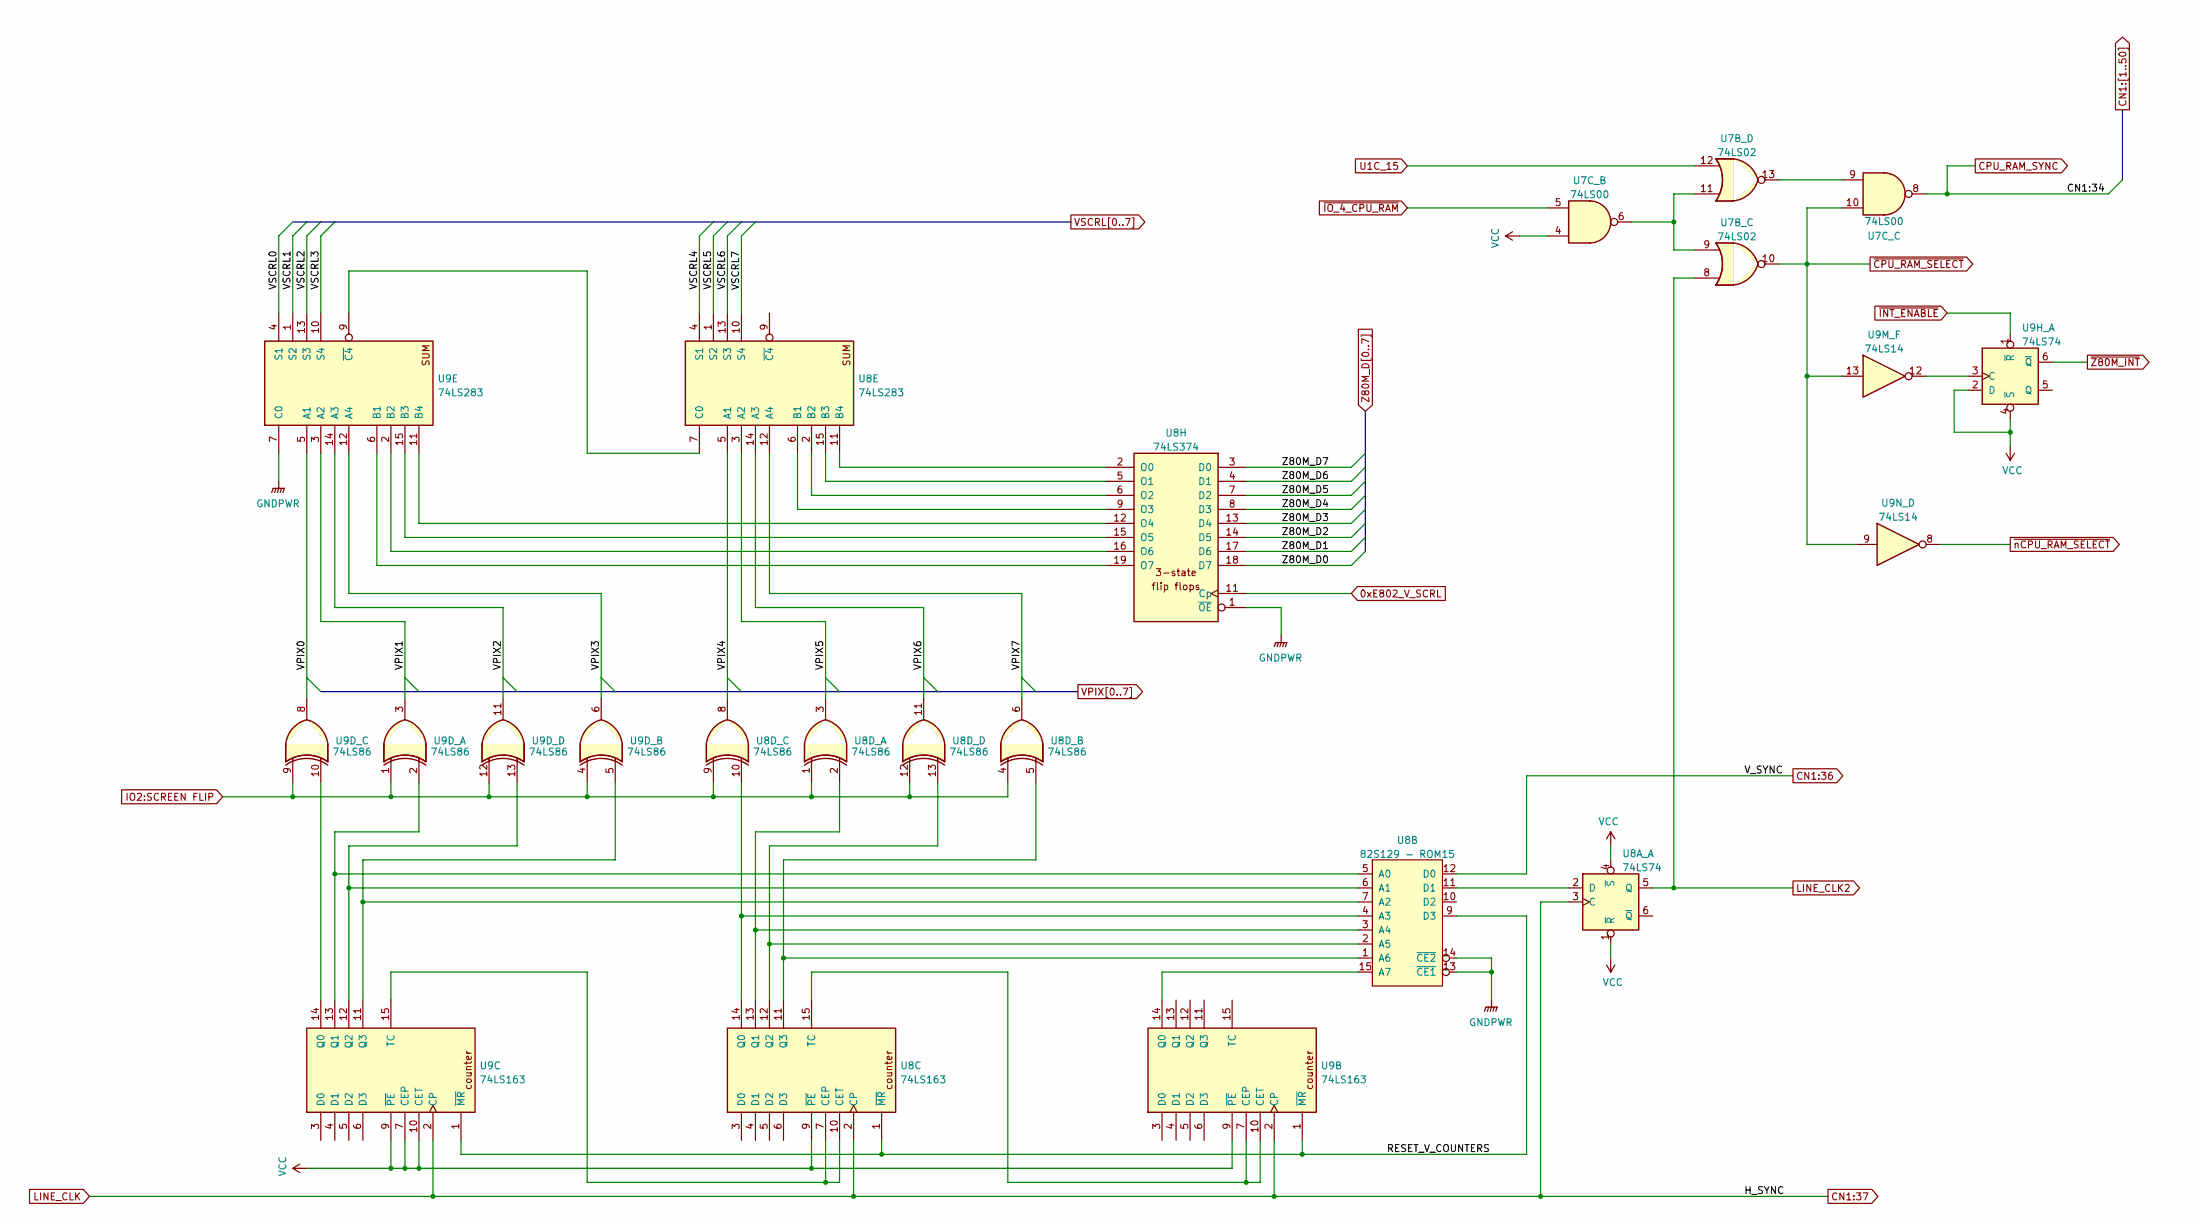
[picture p34: schematic vpixels.kicad_sch]

Parts:
U7B_: 74LS02
U7C_: 74LS00
U8A_, U9H_: 74LS74
U8B: 82S129 - ROM15
U8C, U9B, U9C: 74LS163
U8D_, U9D_: 74LS86
U8E, U9E: 74LS283
U8H: 74LS374
U9M_, U9N_: 74LS14

Connections:
0xE802_V_SCRL: U8H.11 (Cp)
CN1:36: U8B.12 (D0)
CN1:37: U8A_.3 (C), U8C.2 (CP), U9B.2 (CP), U9C.2 (CP)
CPU_RAM_SYNC: U7C_.8
GNDPWR: U8H.1 (~OE), U9E.7 (C0)
IO2:SCREEN FLIP: U8D_.1, U8D_.4, U8D_.9, U8D_.12, U9D_.1, U9D_.4, U9D_.9, U9D_.12
LINE_CLK2: U7B_.8, U8A_.5 (Q)
unnamed: U7B_.9, U7B_.11, U7C_.6
unnamed: U7B_.13, U7C_.9
unnamed: U8A_.2 (D), U8B.11 (D1)
unnamed: U8B.1 (A6), U8C.11 (Q3), U8D_.5
unnamed: U8B.2 (A5), U8C.12 (Q2), U8D_.13
unnamed: U8B.3 (A4), U8C.13 (Q1), U8D_.2
unnamed: U8B.4 (A3), U8C.14 (Q0), U8D_.10
unnamed: U8B.5 (A0), U9C.13 (Q1), U9D_.2
unnamed: U8B.6 (A1), U9C.12 (Q2), U9D_.13
unnamed: U8B.7 (A2), U9C.11 (Q3), U9D_.5
unnamed: U8B.13 (~CE1), U8B.14 (~CE2)
unnamed: U8B.15 (A7), U9B.14 (Q0)
unnamed: U8C.7 (CEP), U8C.10 (CET), U9C.15 (TC)
unnamed: U8C.15 (TC), U9B.7 (CEP), U9B.10 (CET)
unnamed: U8E.2 (B2), U8H.6 (O2)
unnamed: U8E.6 (B1), U8H.9 (O3)
unnamed: U8E.7 (C0), U9E.9 (~C4)
unnamed: U8E.11 (B4), U8H.2 (O0)
unnamed: U8E.15 (B3), U8H.5 (O1)
unnamed: U8H.12 (O4), U9E.11 (B4)
unnamed: U8H.15 (O5), U9E.15 (B3)
unnamed: U8H.16 (O6), U9E.2 (B2)
unnamed: U8H.19 (O7), U9E.6 (B1)
unnamed: U9C.14 (Q0), U9D_.10
unnamed: U9H_.3 (C), U9M_.12
RESET_V_COUNTERS: U8B.9 (D3), U8C.1 (~MR), U9B.1 (~MR), U9C.1 (~MR)
U1C_15: U7B_.12
VCC: U7C_.4, U8C.9 (~PE), U9B.9 (~PE), U9C.7 (CEP), U9C.9 (~PE), U9C.10 (CET), U9H_.2 (D), U9H_.4 (~S)
VPIX0: U9D_.8, U9E.5 (A1)
VPIX1: U9D_.3, U9E.3 (A2)
VPIX2: U9D_.11, U9E.14 (A3)
VPIX3: U9D_.6, U9E.12 (A4)
VPIX4: U8D_.8, U8E.5 (A1)
VPIX5: U8D_.3, U8E.3 (A2)
VPIX6: U8D_.11, U8E.14 (A3)
VPIX7: U8D_.6, U8E.12 (A4)
VSCRL0: U9E.4 (S1)
VSCRL1: U9E.1 (S2)
VSCRL2: U9E.13 (S3)
VSCRL3: U9E.10 (S4)
VSCRL4: U8E.4 (S1)
VSCRL5: U8E.1 (S2)
VSCRL6: U8E.13 (S3)
VSCRL7: U8E.10 (S4)
Z80M_D0: U8H.18 (D7)
Z80M_D1: U8H.17 (D6)
Z80M_D2: U8H.14 (D5)
Z80M_D3: U8H.13 (D4)
Z80M_D4: U8H.8 (D3)
Z80M_D5: U8H.7 (D2)
Z80M_D6: U8H.4 (D1)
Z80M_D7: U8H.3 (D0)
~CPU_RAM_SELECT: U7B_.10, U7C_.10, U9M_.13, U9N_.9
~INT_ENABLE: U9H_.1 (~R)
~IO_4_CPU_RAM: U7C_.5
~Z80M_INT: U9H_.6 (~Q)
~nCPU_RAM_SELECT: U9N_.8
