MiSTer-devel/Arcade-SlapFight_MiSTer/rtl/rom_loader.sv

//============================================================================
// 
//  SD card ROM loader and ROM selector for MISTer.
//  Copyright (C) 2019 Kitrinx (aka Rysha)
//
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
//============================================================================

// Rom layout for SlapFight:
// 0x00000 - 0x07FFF = eprom_1 - Main CPU Program
// 0x08000 - 0x0FFFF = eprom_2 - Main CPU Program
// 0x10000 - 0x11FFF = eprom_9 - Audio CPU Program
// 0x12000 - 0x13FFF = eprom_3 - Foreground - Chars
// 0x14000 - 0x15FFF = eprom_4 - Foreground - Chars
// 0x16000 - 0x1DFFF = eprom_5 - Background - Tiles
// 0x1E000 - 0x25FFF = eprom_6 - Background - Tiles
// 0x26000 - 0x2DFFF = eprom_7 - Background - Tiles
// 0x2E000 - 0x35FFF = eprom_8 - Background - Tiles


module selector
(
	input logic [24:0] ioctl_addr,
	output logic ep0_cs, ep0b_cs, ep1_cs, ep2_cs, ep3_cs, ep4_cs, ep5_cs, ep6_cs, ep7_cs, ep8_cs, ep9_cs, ep10_cs, ep11_cs, ep12_cs, ep13_cs,ep_dummy_cs,cp1_cs,cp2_cs,cp3_cs
);

	always_comb begin
		{ep0_cs, ep0b_cs, ep1_cs, ep2_cs, ep3_cs, ep4_cs, ep5_cs, ep6_cs, ep7_cs, ep8_cs, ep9_cs, ep10_cs, ep11_cs, ep12_cs, ep13_cs,ep_dummy_cs,cp1_cs,cp2_cs,cp3_cs} = 0;


		if     (ioctl_addr < 'h04000) ep0_cs = 1; // 0x4000 13   - Main CPU
		else if(ioctl_addr < 'h08000) ep0b_cs = 1;// 0x4000 13   - Main CPU
		else if(ioctl_addr < 'h10000) ep1_cs = 1; // 0x8000 14   - Main CPU
		else if(ioctl_addr < 'h12000) ep2_cs = 1; // 0x2000 14	- Audio CPU Program
		else if(ioctl_addr < 'h14000) ep3_cs = 1; // 0x2000 12   - Foreground - Chars
		else if(ioctl_addr < 'h16000) ep4_cs = 1; // 0x2000 12   - Foreground - Chars
		else if(ioctl_addr < 'h18000) ep_dummy_cs = 1; // 0x2000 12   - Foreground - Chars
		else if(ioctl_addr < 'h20000) ep5_cs = 1; // 0x8000 14   - Background - Tiles
		else if(ioctl_addr < 'h28000) ep6_cs = 1; // 0x8000 14	- Background - Tiles
		else if(ioctl_addr < 'h30000) ep7_cs = 1; // 0x8000 14	- Background - Tiles
		else if(ioctl_addr < 'h38000) ep8_cs = 1; // 0x8000 14	- Background - Tiles
		else if(ioctl_addr < 'h40000) ep9_cs = 1; // 0x8000 14	- Sprites
		else if(ioctl_addr < 'h48000) ep10_cs = 1; // 0x8000 14	- Sprites
		else if(ioctl_addr < 'h50000) ep11_cs = 1; // 0x8000 14	- Sprites
		else if(ioctl_addr < 'h58000) ep12_cs = 1; // 0x8000 14	- Sprites

		else if(ioctl_addr < 'h58100) cp1_cs = 1; // 0x8000 14	- Colour Prom #1
		else if(ioctl_addr < 'h58200) cp2_cs = 1; // 0x8000 14	- Colour Prom #2
		else if(ioctl_addr < 'h58300) cp3_cs = 1; // 0x8000 14	- Colour Prom #3

		else ep13_cs = 1; // 0x8000 14	- Background - Tiles

	end
endmodule

////////////
// EPROMS //
////////////

module eprom_0 //program
(
	input logic        CLK,
	input logic        CLK_DL,
	input logic        CEN,
	input logic [13:0] ADDR,
	input logic [24:0] ADDR_DL,
	input logic [7:0]  DATA_IN,
	input logic        CS_DL,
	input logic        WR,
	output logic [7:0] DATA
);

	dpram_dc #(.widthad_a(14)) eprom_0
	(
		.clock_a(CLK),
		.address_a(ADDR[13:0]),
		.q_a(DATA),
		.clock_b(CLK_DL),
		.address_b(ADDR_DL[13:0]),
		.data_b(DATA_IN),
		.wren_b(WR & CS_DL)
	);
endmodule


module eprom_0b //program
(
	input logic        CLK,
	input logic        CLK_DL,
	input logic        CEN,
	input logic [13:0] ADDR,
	input logic [24:0] ADDR_DL,
	input logic [7:0]  DATA_IN,
	input logic        CS_DL,
	input logic        WR,
	output logic [7:0] DATA
);

	dpram_dc #(.widthad_a(14)) eprom_0b
	(
		.clock_a(CLK),
		.address_a(ADDR[13:0]),
		.q_a(DATA),
		.clock_b(CLK_DL),
		.address_b(ADDR_DL[13:0]),
		.data_b(DATA_IN),
		.wren_b(WR & CS_DL)
	);
endmodule

module eprom_1  //program
(
	input logic        CLK,
	input logic        CLK_DL,
	input logic        CEN,	
	input logic [14:0] ADDR,
	input logic [24:0] ADDR_DL,
	input logic [7:0]  DATA_IN,
	input logic        CS_DL,
	input logic        WR,
	output logic [7:0] DATA
);
	
	dpram_dc #(.widthad_a(15)) eprom_1
	(
		.clock_a(CLK),
		.address_a(ADDR[14:0]),
		.q_a(DATA),
		.clock_b(CLK_DL),
		.address_b(ADDR_DL[14:0]),
		.data_b(DATA_IN),
		.wren_b(WR & CS_DL)
	);
endmodule

module eprom_2 //audio program
(
	input logic        CLK,
	input logic        CLK_DL,
	input logic [12:0] ADDR,
	input logic [24:0] ADDR_DL,
	input logic [7:0]  DATA_IN,
	input logic        CS_DL,
	input logic        WR,
	output logic [7:0] DATA
);

	dpram_dc #(.widthad_a(13)) eprom_2
	(
		.clock_a(CLK),
		.address_a(ADDR[12:0]),
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
	input logic        CS_DL,
	input logic        WR,
	output logic [3:0] DATA
);
	dpram_dc #(.widthad_a(8)) cprom_3
	(
		.clock_a(CLK),
		.address_a(ADDR),
		.q_a(DATA[3:0]),

		.clock_b(CLK_DL),
		.address_b(ADDR_DL[7:0]),
		.data_b(DATA_IN),
		.wren_b(WR & CS_DL)
	);
endmodule
